nico-malkov/variometer/software/nRF5_SDK_17.1.0/examples/peripheral/variometer_v143/dfu/vario1d5/config/sdk_config.h

/**
 * Copyright (c) 2017 - 2020, Nordic Semiconductor ASA
 *
 * All rights reserved.
 *
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
 * 3. Neither the name of Nordic Semiconductor ASA nor the names of its
 *    contributors may be used to endorse or promote products derived from this
 *    software without specific prior written permission.
 *
 * 4. This software, with or without modification, must only be used with a
 *    Nordic Semiconductor ASA integrated circuit.
 *
 * 5. Any software provided in binary form under this license must not be reverse
 *    engineered, decompiled, modified and/or disassembled.
 *
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
 */



#ifndef SDK_CONFIG_H
#define SDK_CONFIG_H
// <<< Use Configuration Wizard in Context Menu >>>\n
#ifdef USE_APP_CONFIG
#include "app_config.h"
#endif
// <h> nRF_Bootloader 

//==========================================================
// <h> nrf_bootloader - Bootloader settings

//==========================================================
// <h> Application integrity checks 

//==========================================================
// <q> NRF_BL_APP_CRC_CHECK_SKIPPED_ON_GPREGRET2  - Skip CRC integrity check of the application when bit 1 (0-indexed) is set in the GPREGRET2 register.
 

// <i> Only CRC checks can be skipped. For other boot validation types, the GPREGRET2 register is ignored.

#ifndef NRF_BL_APP_CRC_CHECK_SKIPPED_ON_GPREGRET2
#define NRF_BL_APP_CRC_CHECK_SKIPPED_ON_GPREGRET2 1
#endif

// <q> NRF_BL_APP_CRC_CHECK_SKIPPED_ON_SYSTEMOFF_RESET  - Skip integrity check of the application when waking up from the System Off state.
 

// <i> Only CRC checks can be skipped. For other boot validation types, the reset state is ignored.

#ifndef NRF_BL_APP_CRC_CHECK_SKIPPED_ON_SYSTEMOFF_RESET
#define NRF_BL_APP_CRC_CHECK_SKIPPED_ON_SYSTEMOFF_RESET 1
#endif

// <q> NRF_BL_APP_SIGNATURE_CHECK_REQUIRED  - Perform signature check on the app. Requires the signature to be sent in the init packet.
 

#ifndef NRF_BL_APP_SIGNATURE_CHECK_REQUIRED
#define NRF_BL_APP_SIGNATURE_CHECK_REQUIRED 0
#endif

// <q> NRF_BL_DFU_ALLOW_UPDATE_FROM_APP  - Whether to allow the app to receive firmware updates for the bootloader to activate.
 

// <i> Enable this to allow the app to instruct the bootloader to activate firmware.
// <i> The bootloader will do its own postvalidation.

#ifndef NRF_BL_DFU_ALLOW_UPDATE_FROM_APP
#define NRF_BL_DFU_ALLOW_UPDATE_FROM_APP 0
#endif

// </h> 
//==========================================================

// <h> DFU mode enter method 

//==========================================================
// <e> NRF_BL_DFU_ENTER_METHOD_BUTTON - Enter DFU mode on button press.
//==========================================================
#ifndef NRF_BL_DFU_ENTER_METHOD_BUTTON
#define NRF_BL_DFU_ENTER_METHOD_BUTTON 1
#endif
// <o> NRF_BL_DFU_ENTER_METHOD_BUTTON_PIN  - Button for entering DFU mode.
 
// <0=> 0 (P0.0) 
// <1=> 1 (P0.1) 
// <2=> 2 (P0.2) 
// <3=> 3 (P0.3) 
// <4=> 4 (P0.4) 
// <5=> 5 (P0.5) 
// <6=> 6 (P0.6) 
// <7=> 7 (P0.7) 
// <8=> 8 (P0.8) 
// <9=> 9 (P0.9) 
// <10=> 10 (P0.10) 
// <11=> 11 (P0.11) 
// <12=> 12 (P0.12) 
// <13=> 13 (P0.13) 
// <14=> 14 (P0.14) 
// <15=> 15 (P0.15) 
// <16=> 16 (P0.16) 
// <17=> 17 (P0.17) 
// <18=> 18 (P0.18) 
// <19=> 19 (P0.19) 
// <20=> 20 (P0.20) 
// <21=> 21 (P0.21) 
// <22=> 22 (P0.22) 
// <23=> 23 (P0.23) 
// <24=> 24 (P0.24) 
// <25=> 25 (P0.25) 
// <26=> 26 (P0.26) 
// <27=> 27 (P0.27) 
// <28=> 28 (P0.28) 
// <29=> 29 (P0.29) 
// <30=> 30 (P0.30) 
// <31=> 31 (P0.31) 
// <32=> 32 (P1.0) 
// <33=> 33 (P1.1) 
// <34=> 34 (P1.2) 
// <35=> 35 (P1.3) 
// <36=> 36 (P1.4) 
// <37=> 37 (P1.5) 
// <38=> 38 (P1.6) 
// <39=> 39 (P1.7) 
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

#ifndef NRF_BL_DFU_ENTER_METHOD_BUTTON_PIN
#define NRF_BL_DFU_ENTER_METHOD_BUTTON_PIN 25
#endif

// </e>

// <q> NRF_BL_DFU_ENTER_METHOD_PINRESET  - Enter DFU mode on pin reset.
 

#ifndef NRF_BL_DFU_ENTER_METHOD_PINRESET
#define NRF_BL_DFU_ENTER_METHOD_PINRESET 0
#endif

// <q> NRF_BL_DFU_ENTER_METHOD_GPREGRET  - Enter DFU mode when bit 0 is set in the NRF_POWER_GPREGRET register.
 

#ifndef NRF_BL_DFU_ENTER_METHOD_GPREGRET
#define NRF_BL_DFU_ENTER_METHOD_GPREGRET 1
#endif

// <q> NRF_BL_DFU_ENTER_METHOD_BUTTONLESS  - Enter DFU mode when the Boolean enter_buttonless_dfu in DFU settings is true.
 

#ifndef NRF_BL_DFU_ENTER_METHOD_BUTTONLESS
#define NRF_BL_DFU_ENTER_METHOD_BUTTONLESS 0
#endif

// </h> 
//==========================================================

// <h> DFU timers 

//==========================================================
// <o> NRF_BL_DFU_CONTINUATION_TIMEOUT_MS - Timeout in ms when expecting an update immediately.  <100-60000000> 


// <i> This timeout is used after updating the SoftDevice, when there is
// <i> already a valid application present. The bootloader will enter DFU mode
// <i> for a short time instead of booting the old application to allow the host
// <i> to immediately transfer a new application if it wishes.

#ifndef NRF_BL_DFU_CONTINUATION_TIMEOUT_MS
#define NRF_BL_DFU_CONTINUATION_TIMEOUT_MS 10000
#endif

// <o> NRF_BL_DFU_INACTIVITY_TIMEOUT_MS - Timeout in ms before automatically starting a valid application due to inactivity.  <0-60000000> 


// <i> If 0, no inactivity timer will be used. Values 1-99 are invalid.

#ifndef NRF_BL_DFU_INACTIVITY_TIMEOUT_MS
#define NRF_BL_DFU_INACTIVITY_TIMEOUT_MS 120000
#endif

// </h> 
//==========================================================

// <h> Watchdog timer 

//==========================================================
// <o> NRF_BL_WDT_MAX_SCHEDULER_LATENCY_MS - Maximum latency of the scheduler in miliseconds 
// <i> Maximum latency of the scheduler is compared with
// <i> watchdog counter reload value (CRV). If latency is big
// <i> enough, the watchdog will be fed from internal timer
// <i> handler along with feed from user function. If latency
// <i> is smaller than CRV, the watchdog will not be internally fed once
// <i> it will be externally fed. Maximum latency is mainly affected
// <i> by flash operations.

#ifndef NRF_BL_WDT_MAX_SCHEDULER_LATENCY_MS
#define NRF_BL_WDT_MAX_SCHEDULER_LATENCY_MS 10000
#endif

// </h> 
//==========================================================

// <h> Misc Bootloader settings 

//==========================================================
// <q> NRF_BL_DEBUG_PORT_DISABLE  - Disable access to the chip via the debug port.
 

// <i> Disable access to the chip via the debug port.
// <i> This modifies the APPROTECT and DEBUGCTRL registers.
// <i> Enable this option in production code if such
// <i> access should be prohibited. Read about the registers
// <i> for more details.

#ifndef NRF_BL_DEBUG_PORT_DISABLE
#define NRF_BL_DEBUG_PORT_DISABLE 0
#endif

// <o> NRF_BL_FW_COPY_PROGRESS_STORE_STEP - Number of pages copied after which progress in the settings page is updated. 
// <i> Progress stored in the settings page allows the bootloader to resume
// <i> copying the new firmware in case of interruption (reset).
// <i> If the value is small, then the resume point is more accurate. However,
// <i>  it also impacts negatively on flash wear.

#ifndef NRF_BL_FW_COPY_PROGRESS_STORE_STEP
#define NRF_BL_FW_COPY_PROGRESS_STORE_STEP 8
#endif

// <o> NRF_BL_RESET_DELAY_MS - Time to wait before resetting the bootloader. 
// <i> Time (in ms) to wait before resetting the bootloader after DFU has been completed or aborted. This allows more time for e.g. disconnecting the BLE link or writing logs.

#ifndef NRF_BL_RESET_DELAY_MS
#define NRF_BL_RESET_DELAY_MS 0
#endif

// </h> 
//==========================================================

// </h> 
//==========================================================

// </h> 
//==========================================================

// <h> nRF_Crypto 

//==========================================================
// <e> NRF_CRYPTO_ENABLED - nrf_crypto - Cryptography library.
//==========================================================
#ifndef NRF_CRYPTO_ENABLED
#define NRF_CRYPTO_ENABLED 1
#endif
// <o> NRF_CRYPTO_ALLOCATOR  - Memory allocator
 

// <i> Choose memory allocator used by nrf_crypto. Default is alloca if possible or nrf_malloc otherwise. If 'User macros' are selected, the user has to create 'nrf_crypto_allocator.h' file that contains NRF_CRYPTO_ALLOC, NRF_CRYPTO_FREE, and NRF_CRYPTO_ALLOC_ON_STACK.
// <0=> Default 
// <1=> User macros 
// <2=> On stack (alloca) 
// <3=> C dynamic memory (malloc) 
// <4=> SDK Memory Manager (nrf_malloc) 

#ifndef NRF_CRYPTO_ALLOCATOR
#define NRF_CRYPTO_ALLOCATOR 1
#endif

// <e> NRF_CRYPTO_BACKEND_CC310_BL_ENABLED - Enable the ARM Cryptocell CC310 reduced backend.

// <i> The CC310 hardware-accelerated cryptography backend with reduced functionality and footprint (only available on nRF52840).
//==========================================================
#ifndef NRF_CRYPTO_BACKEND_CC310_BL_ENABLED
#define NRF_CRYPTO_BACKEND_CC310_BL_ENABLED 1
#endif
// <q> NRF_CRYPTO_BACKEND_CC310_BL_ECC_SECP224R1_ENABLED  - Enable the secp224r1 elliptic curve support using CC310_BL.
 

#ifndef NRF_CRYPTO_BACKEND_CC310_BL_ECC_SECP224R1_ENABLED
#define NRF_CRYPTO_BACKEND_CC310_BL_ECC_SECP224R1_ENABLED 0
#endif

// <q> NRF_CRYPTO_BACKEND_CC310_BL_ECC_SECP256R1_ENABLED  - Enable the secp256r1 elliptic curve support using CC310_BL.
 

#ifndef NRF_CRYPTO_BACKEND_CC310_BL_ECC_SECP256R1_ENABLED
#define NRF_CRYPTO_BACKEND_CC310_BL_ECC_SECP256R1_ENABLED 1
#endif

// <q> NRF_CRYPTO_BACKEND_CC310_BL_HASH_SHA256_ENABLED  - CC310_BL SHA-256 hash functionality.
 

// <i> CC310_BL backend implementation for hardware-accelerated SHA-256.

#ifndef NRF_CRYPTO_BACKEND_CC310_BL_HASH_SHA256_ENABLED
#define NRF_CRYPTO_BACKEND_CC310_BL_HASH_SHA256_ENABLED 1
#endif

// <q> NRF_CRYPTO_BACKEND_CC310_BL_HASH_AUTOMATIC_RAM_BUFFER_ENABLED  - nrf_cc310_bl buffers to RAM before running hash operation
 

// <i> Enabling this makes hashing of addresses in FLASH range possible. Size of buffer allocated for hashing is set by NRF_CRYPTO_BACKEND_CC310_BL_HASH_AUTOMATIC_RAM_BUFFER_SIZE

#ifndef NRF_CRYPTO_BACKEND_CC310_BL_HASH_AUTOMATIC_RAM_BUFFER_ENABLED
#define NRF_CRYPTO_BACKEND_CC310_BL_HASH_AUTOMATIC_RAM_BUFFER_ENABLED 1
#endif

// <o> NRF_CRYPTO_BACKEND_CC310_BL_HASH_AUTOMATIC_RAM_BUFFER_SIZE - nrf_cc310_bl hash outputs digests in little endian 
// <i> Makes the nrf_cc310_bl hash functions output digests in little endian format. Only for use in nRF SDK DFU!

#ifndef NRF_CRYPTO_BACKEND_CC310_BL_HASH_AUTOMATIC_RAM_BUFFER_SIZE
#define NRF_CRYPTO_BACKEND_CC310_BL_HASH_AUTOMATIC_RAM_BUFFER_SIZE 4096
#endif

// <q> NRF_CRYPTO_BACKEND_CC310_BL_INTERRUPTS_ENABLED  - Enable Interrupts while support using CC310 bl.
 

// <i> Select a library version compatible with the configuration. When interrupts are disable, a version named _noint must be used

#ifndef NRF_CRYPTO_BACKEND_CC310_BL_INTERRUPTS_ENABLED
#define NRF_CRYPTO_BACKEND_CC310_BL_INTERRUPTS_ENABLED 1
#endif

// </e>

// <e> NRF_CRYPTO_BACKEND_CC310_ENABLED - Enable the ARM Cryptocell CC310 backend.

// <i> The CC310 hardware-accelerated cryptography backend (only available on nRF52840).
//==========================================================
#ifndef NRF_CRYPTO_BACKEND_CC310_ENABLED
#define NRF_CRYPTO_BACKEND_CC310_ENABLED 0
#endif
// <q> NRF_CRYPTO_BACKEND_CC310_AES_CBC_ENABLED  - Enable the AES CBC mode using CC310.
 

#ifndef NRF_CRYPTO_BACKEND_CC310_AES_CBC_ENABLED
#define NRF_CRYPTO_BACKEND_CC310_AES_CBC_ENABLED 1
#endif

// <q> NRF_CRYPTO_BACKEND_CC310_AES_CTR_ENABLED  - Enable the AES CTR mode using CC310.
 

#ifndef NRF_CRYPTO_BACKEND_CC310_AES_CTR_ENABLED
#define NRF_CRYPTO_BACKEND_CC310_AES_CTR_ENABLED 1
#endif

// <q> NRF_CRYPTO_BACKEND_CC310_AES_ECB_ENABLED  - Enable the AES ECB mode using CC310.
 

#ifndef NRF_CRYPTO_BACKEND_CC310_AES_ECB_ENABLED
#define NRF_CRYPTO_BACKEND_CC310_AES_ECB_ENABLED 1
#endif

// <q> NRF_CRYPTO_BACKEND_CC310_AES_CBC_MAC_ENABLED  - Enable the AES CBC_MAC mode using CC310.
 

#ifndef NRF_CRYPTO_BACKEND_CC310_AES_CBC_MAC_ENABLED
#define NRF_CRYPTO_BACKEND_CC310_AES_CBC_MAC_ENABLED 1
#endif

// <q> NRF_CRYPTO_BACKEND_CC310_AES_CMAC_ENABLED  - Enable the AES CMAC mode using CC310.
 

#ifndef NRF_CRYPTO_BACKEND_CC310_AES_CMAC_ENABLED
#define NRF_CRYPTO_BACKEND_CC310_AES_CMAC_ENABLED 1
#endif

// <q> NRF_CRYPTO_BACKEND_CC310_AES_CCM_ENABLED  - Enable the AES CCM mode using CC310.
 

#ifndef NRF_CRYPTO_BACKEND_CC310_AES_CCM_ENABLED
#define NRF_CRYPTO_BACKEND_CC310_AES_CCM_ENABLED 1
#endif

// <q> NRF_CRYPTO_BACKEND_CC310_AES_CCM_STAR_ENABLED  - Enable the AES CCM* mode using CC310.
 

#ifndef NRF_CRYPTO_BACKEND_CC310_AES_CCM_STAR_ENABLED
#define NRF_CRYPTO_BACKEND_CC310_AES_CCM_STAR_ENABLED 1
#endif

// <q> NRF_CRYPTO_BACKEND_CC310_CHACHA_POLY_ENABLED  - Enable the CHACHA-POLY mode using CC310.
 

#ifndef NRF_CRYPTO_BACKEND_CC310_CHACHA_POLY_ENABLED
#define NRF_CRYPTO_BACKEND_CC310_CHACHA_POLY_ENABLED 1
#endif

// <q> NRF_CRYPTO_BACKEND_CC310_ECC_SECP160R1_ENABLED  - Enable the secp160r1 elliptic curve support using CC310.
 

#ifndef NRF_CRYPTO_BACKEND_CC310_ECC_SECP160R1_ENABLED
#define NRF_CRYPTO_BACKEND_CC310_ECC_SECP160R1_ENABLED 1
#endif

// <q> NRF_CRYPTO_BACKEND_CC310_ECC_SECP160R2_ENABLED  - Enable the secp160r2 elliptic curve support using CC310.
 

#ifndef NRF_CRYPTO_BACKEND_CC310_ECC_SECP160R2_ENABLED
#define NRF_CRYPTO_BACKEND_CC310_ECC_SECP160R2_ENABLED 1
#endif

// <q> NRF_CRYPTO_BACKEND_CC310_ECC_SECP192R1_ENABLED  - Enable the secp192r1 elliptic curve support using CC310.
 

#ifndef NRF_CRYPTO_BACKEND_CC310_ECC_SECP192R1_ENABLED
#define NRF_CRYPTO_BACKEND_CC310_ECC_SECP192R1_ENABLED 1
#endif

// <q> NRF_CRYPTO_BACKEND_CC310_ECC_SECP224R1_ENABLED  - Enable the secp224r1 elliptic curve support using CC310.
 

#ifndef NRF_CRYPTO_BACKEND_CC310_ECC_SECP224R1_ENABLED
#define NRF_CRYPTO_BACKEND_CC310_ECC_SECP224R1_ENABLED 1
#endif

// <q> NRF_CRYPTO_BACKEND_CC310_ECC_SECP256R1_ENABLED  - Enable the secp256r1 elliptic curve support using CC310.
 

#ifndef NRF_CRYPTO_BACKEND_CC310_ECC_SECP256R1_ENABLED
#define NRF_CRYPTO_BACKEND_CC310_ECC_SECP256R1_ENABLED 1
#endif

// <q> NRF_CRYPTO_BACKEND_CC310_ECC_SECP384R1_ENABLED  - Enable the secp384r1 elliptic curve support using CC310.
 

#ifndef NRF_CRYPTO_BACKEND_CC310_ECC_SECP384R1_ENABLED
#define NRF_CRYPTO_BACKEND_CC310_ECC_SECP384R1_ENABLED 1
#endif

// <q> NRF_CRYPTO_BACKEND_CC310_ECC_SECP521R1_ENABLED  - Enable the secp521r1 elliptic curve support using CC310.
 

#ifndef NRF_CRYPTO_BACKEND_CC310_ECC_SECP521R1_ENABLED
#define NRF_CRYPTO_BACKEND_CC310_ECC_SECP521R1_ENABLED 1
#endif

// <q> NRF_CRYPTO_BACKEND_CC310_ECC_SECP160K1_ENABLED  - Enable the secp160k1 elliptic curve support using CC310.
 

#ifndef NRF_CRYPTO_BACKEND_CC310_ECC_SECP160K1_ENABLED
#define NRF_CRYPTO_BACKEND_CC310_ECC_SECP160K1_ENABLED 1
#endif

// <q> NRF_CRYPTO_BACKEND_CC310_ECC_SECP192K1_ENABLED  - Enable the secp192k1 elliptic curve support using CC310.
 

#ifndef NRF_CRYPTO_BACKEND_CC310_ECC_SECP192K1_ENABLED
#define NRF_CRYPTO_BACKEND_CC310_ECC_SECP192K1_ENABLED 1
#endif

// <q> NRF_CRYPTO_BACKEND_CC310_ECC_SECP224K1_ENABLED  - Enable the secp224k1 elliptic curve support using CC310.
 

#ifndef NRF_CRYPTO_BACKEND_CC310_ECC_SECP224K1_ENABLED
#define NRF_CRYPTO_BACKEND_CC310_ECC_SECP224K1_ENABLED 1
#endif

// <q> NRF_CRYPTO_BACKEND_CC310_ECC_SECP256K1_ENABLED  - Enable the secp256k1 elliptic curve support using CC310.
 

#ifndef NRF_CRYPTO_BACKEND_CC310_ECC_SECP256K1_ENABLED
#define NRF_CRYPTO_BACKEND_CC310_ECC_SECP256K1_ENABLED 1
#endif

// <q> NRF_CRYPTO_BACKEND_CC310_ECC_CURVE25519_ENABLED  - Enable the Curve25519 curve support using CC310.
 

#ifndef NRF_CRYPTO_BACKEND_CC310_ECC_CURVE25519_ENABLED
#define NRF_CRYPTO_BACKEND_CC310_ECC_CURVE25519_ENABLED 1
#endif

// <q> NRF_CRYPTO_BACKEND_CC310_ECC_ED25519_ENABLED  - Enable the Ed25519 curve support using CC310.
 

#ifndef NRF_CRYPTO_BACKEND_CC310_ECC_ED25519_ENABLED
#define NRF_CRYPTO_BACKEND_CC310_ECC_ED25519_ENABLED 1
#endif

// <q> NRF_CRYPTO_BACKEND_CC310_HASH_SHA256_ENABLED  - CC310 SHA-256 hash functionality.
 

// <i> CC310 backend implementation for hardware-accelerated SHA-256.

#ifndef NRF_CRYPTO_BACKEND_CC310_HASH_SHA256_ENABLED
#define NRF_CRYPTO_BACKEND_CC310_HASH_SHA256_ENABLED 1
#endif

// <q> NRF_CRYPTO_BACKEND_CC310_HASH_SHA512_ENABLED  - CC310 SHA-512 hash functionality
 

// <i> CC310 backend implementation for SHA-512 (in software).

#ifndef NRF_CRYPTO_BACKEND_CC310_HASH_SHA512_ENABLED
#define NRF_CRYPTO_BACKEND_CC310_HASH_SHA512_ENABLED 1
#endif

// <q> NRF_CRYPTO_BACKEND_CC310_HMAC_SHA256_ENABLED  - CC310 HMAC using SHA-256
 

// <i> CC310 backend implementation for HMAC using hardware-accelerated SHA-256.

#ifndef NRF_CRYPTO_BACKEND_CC310_HMAC_SHA256_ENABLED
#define NRF_CRYPTO_BACKEND_CC310_HMAC_SHA256_ENABLED 1
#endif

// <q> NRF_CRYPTO_BACKEND_CC310_HMAC_SHA512_ENABLED  - CC310 HMAC using SHA-512
 

// <i> CC310 backend implementation for HMAC using SHA-512 (in software).

#ifndef NRF_CRYPTO_BACKEND_CC310_HMAC_SHA512_ENABLED
#define NRF_CRYPTO_BACKEND_CC310_HMAC_SHA512_ENABLED 1
#endif

// <q> NRF_CRYPTO_BACKEND_CC310_RNG_ENABLED  - Enable RNG support using CC310.
 

#ifndef NRF_CRYPTO_BACKEND_CC310_RNG_ENABLED
#define NRF_CRYPTO_BACKEND_CC310_RNG_ENABLED 1
#endif

// <q> NRF_CRYPTO_BACKEND_CC310_INTERRUPTS_ENABLED  - Enable Interrupts while support using CC310.
 

// <i> Select a library version compatible with the configuration. When interrupts are disable, a version named _noint must be used

#ifndef NRF_CRYPTO_BACKEND_CC310_INTERRUPTS_ENABLED
#define NRF_CRYPTO_BACKEND_CC310_INTERRUPTS_ENABLED 1
#endif

// </e>

// <e> NRF_CRYPTO_BACKEND_CIFRA_ENABLED - Enable the Cifra backend.
//==========================================================
#ifndef NRF_CRYPTO_BACKEND_CIFRA_ENABLED
#define NRF_CRYPTO_BACKEND_CIFRA_ENABLED 0
#endif
// <q> NRF_CRYPTO_BACKEND_CIFRA_AES_EAX_ENABLED  - Enable the AES EAX mode using Cifra.
 

#ifndef NRF_CRYPTO_BACKEND_CIFRA_AES_EAX_ENABLED
#define NRF_CRYPTO_BACKEND_CIFRA_AES_EAX_ENABLED 1
#endif

// </e>

// <e> NRF_CRYPTO_BACKEND_MBEDTLS_ENABLED - Enable the mbed TLS backend.
//==========================================================
#ifndef NRF_CRYPTO_BACKEND_MBEDTLS_ENABLED
#define NRF_CRYPTO_BACKEND_MBEDTLS_ENABLED 0
#endif
// <q> NRF_CRYPTO_BACKEND_MBEDTLS_AES_CBC_ENABLED  - Enable the AES CBC mode mbed TLS.
 

#ifndef NRF_CRYPTO_BACKEND_MBEDTLS_AES_CBC_ENABLED
#define NRF_CRYPTO_BACKEND_MBEDTLS_AES_CBC_ENABLED 1
#endif

// <q> NRF_CRYPTO_BACKEND_MBEDTLS_AES_CTR_ENABLED  - Enable the AES CTR mode using mbed TLS.
 

#ifndef NRF_CRYPTO_BACKEND_MBEDTLS_AES_CTR_ENABLED
#define NRF_CRYPTO_BACKEND_MBEDTLS_AES_CTR_ENABLED 1
#endif

// <q> NRF_CRYPTO_BACKEND_MBEDTLS_AES_CFB_ENABLED  - Enable the AES CFB mode using mbed TLS.
 

#ifndef NRF_CRYPTO_BACKEND_MBEDTLS_AES_CFB_ENABLED
#define NRF_CRYPTO_BACKEND_MBEDTLS_AES_CFB_ENABLED 1
#endif

// <q> NRF_CRYPTO_BACKEND_MBEDTLS_AES_ECB_ENABLED  - Enable the AES ECB mode using mbed TLS.
 

#ifndef NRF_CRYPTO_BACKEND_MBEDTLS_AES_ECB_ENABLED
#define NRF_CRYPTO_BACKEND_MBEDTLS_AES_ECB_ENABLED 1
#endif

// <q> NRF_CRYPTO_BACKEND_MBEDTLS_AES_CBC_MAC_ENABLED  - Enable the AES CBC MAC mode using mbed TLS.
 

#ifndef NRF_CRYPTO_BACKEND_MBEDTLS_AES_CBC_MAC_ENABLED
#define NRF_CRYPTO_BACKEND_MBEDTLS_AES_CBC_MAC_ENABLED 1
#endif

// <q> NRF_CRYPTO_BACKEND_MBEDTLS_AES_CMAC_ENABLED  - Enable the AES CMAC mode using mbed TLS.
 

#ifndef NRF_CRYPTO_BACKEND_MBEDTLS_AES_CMAC_ENABLED
#define NRF_CRYPTO_BACKEND_MBEDTLS_AES_CMAC_ENABLED 1
#endif

// <q> NRF_CRYPTO_BACKEND_MBEDTLS_AES_CCM_ENABLED  - Enable the AES CCM mode using mbed TLS.
 

#ifndef NRF_CRYPTO_BACKEND_MBEDTLS_AES_CCM_ENABLED
#define NRF_CRYPTO_BACKEND_MBEDTLS_AES_CCM_ENABLED 1
#endif

// <q> NRF_CRYPTO_BACKEND_MBEDTLS_AES_GCM_ENABLED  - Enable the AES GCM mode using mbed TLS.
 

#ifndef NRF_CRYPTO_BACKEND_MBEDTLS_AES_GCM_ENABLED
#define NRF_CRYPTO_BACKEND_MBEDTLS_AES_GCM_ENABLED 1
#endif

// <q> NRF_CRYPTO_BACKEND_MBEDTLS_ECC_SECP192R1_ENABLED  - Enable secp192r1 (NIST 192-bit) curve
 

// <i> Enable this setting if you need secp192r1 (NIST 192-bit) support using MBEDTLS

#ifndef NRF_CRYPTO_BACKEND_MBEDTLS_ECC_SECP192R1_ENABLED
#define NRF_CRYPTO_BACKEND_MBEDTLS_ECC_SECP192R1_ENABLED 1
#endif

// <q> NRF_CRYPTO_BACKEND_MBEDTLS_ECC_SECP224R1_ENABLED  - Enable secp224r1 (NIST 224-bit) curve
 

// <i> Enable this setting if you need secp224r1 (NIST 224-bit) support using MBEDTLS

#ifndef NRF_CRYPTO_BACKEND_MBEDTLS_ECC_SECP224R1_ENABLED
#define NRF_CRYPTO_BACKEND_MBEDTLS_ECC_SECP224R1_ENABLED 1
#endif

// <q> NRF_CRYPTO_BACKEND_MBEDTLS_ECC_SECP256R1_ENABLED  - Enable secp256r1 (NIST 256-bit) curve
 

// <i> Enable this setting if you need secp256r1 (NIST 256-bit) support using MBEDTLS

#ifndef NRF_CRYPTO_BACKEND_MBEDTLS_ECC_SECP256R1_ENABLED
#define NRF_CRYPTO_BACKEND_MBEDTLS_ECC_SECP256R1_ENABLED 1
#endif

// <q> NRF_CRYPTO_BACKEND_MBEDTLS_ECC_SECP384R1_ENABLED  - Enable secp384r1 (NIST 384-bit) curve
 

// <i> Enable this setting if you need secp384r1 (NIST 384-bit) support using MBEDTLS

#ifndef NRF_CRYPTO_BACKEND_MBEDTLS_ECC_SECP384R1_ENABLED
#define NRF_CRYPTO_BACKEND_MBEDTLS_ECC_SECP384R1_ENABLED 1
#endif

// <q> NRF_CRYPTO_BACKEND_MBEDTLS_ECC_SECP521R1_ENABLED  - Enable secp521r1 (NIST 521-bit) curve
 

// <i> Enable this setting if you need secp521r1 (NIST 521-bit) support using MBEDTLS

#ifndef NRF_CRYPTO_BACKEND_MBEDTLS_ECC_SECP521R1_ENABLED
#define NRF_CRYPTO_BACKEND_MBEDTLS_ECC_SECP521R1_ENABLED 1
#endif

// <q> NRF_CRYPTO_BACKEND_MBEDTLS_ECC_SECP192K1_ENABLED  - Enable secp192k1 (Koblitz 192-bit) curve
 

// <i> Enable this setting if you need secp192k1 (Koblitz 192-bit) support using MBEDTLS

#ifndef NRF_CRYPTO_BACKEND_MBEDTLS_ECC_SECP192K1_ENABLED
#define NRF_CRYPTO_BACKEND_MBEDTLS_ECC_SECP192K1_ENABLED 1
#endif

// <q> NRF_CRYPTO_BACKEND_MBEDTLS_ECC_SECP224K1_ENABLED  - Enable secp224k1 (Koblitz 224-bit) curve
 

// <i> Enable this setting if you need secp224k1 (Koblitz 224-bit) support using MBEDTLS

#ifndef NRF_CRYPTO_BACKEND_MBEDTLS_ECC_SECP224K1_ENABLED
#define NRF_CRYPTO_BACKEND_MBEDTLS_ECC_SECP224K1_ENABLED 1
#endif

// <q> NRF_CRYPTO_BACKEND_MBEDTLS_ECC_SECP256K1_ENABLED  - Enable secp256k1 (Koblitz 256-bit) curve
 

// <i> Enable this setting if you need secp256k1 (Koblitz 256-bit) support using MBEDTLS

#ifndef NRF_CRYPTO_BACKEND_MBEDTLS_ECC_SECP256K1_ENABLED
#define NRF_CRYPTO_BACKEND_MBEDTLS_ECC_SECP256K1_ENABLED 1
#endif

// <q> NRF_CRYPTO_BACKEND_MBEDTLS_ECC_BP256R1_ENABLED  - Enable bp256r1 (Brainpool 256-bit) curve
 

// <i> Enable this setting if you need bp256r1 (Brainpool 256-bit) support using MBEDTLS

#ifndef NRF_CRYPTO_BACKEND_MBEDTLS_ECC_BP256R1_ENABLED
#define NRF_CRYPTO_BACKEND_MBEDTLS_ECC_BP256R1_ENABLED 1
#endif

// <q> NRF_CRYPTO_BACKEND_MBEDTLS_ECC_BP384R1_ENABLED  - Enable bp384r1 (Brainpool 384-bit) curve
 

// <i> Enable this setting if you need bp384r1 (Brainpool 384-bit) support using MBEDTLS

#ifndef NRF_CRYPTO_BACKEND_MBEDTLS_ECC_BP384R1_ENABLED
#define NRF_CRYPTO_BACKEND_MBEDTLS_ECC_BP384R1_ENABLED 1
#endif

// <q> NRF_CRYPTO_BACKEND_MBEDTLS_ECC_BP512R1_ENABLED  - Enable bp512r1 (Brainpool 512-bit) curve
 

// <i> Enable this setting if you need bp512r1 (Brainpool 512-bit) support using MBEDTLS

#ifndef NRF_CRYPTO_BACKEND_MBEDTLS_ECC_BP512R1_ENABLED
#define NRF_CRYPTO_BACKEND_MBEDTLS_ECC_BP512R1_ENABLED 1
#endif

// <q> NRF_CRYPTO_BACKEND_MBEDTLS_ECC_CURVE25519_ENABLED  - Enable Curve25519 curve
 

// <i> Enable this setting if you need Curve25519 support using MBEDTLS

#ifndef NRF_CRYPTO_BACKEND_MBEDTLS_ECC_CURVE25519_ENABLED
#define NRF_CRYPTO_BACKEND_MBEDTLS_ECC_CURVE25519_ENABLED 1
#endif

// <q> NRF_CRYPTO_BACKEND_MBEDTLS_HASH_SHA256_ENABLED  - Enable mbed TLS SHA-256 hash functionality.
 

// <i> mbed TLS backend implementation for SHA-256.

#ifndef NRF_CRYPTO_BACKEND_MBEDTLS_HASH_SHA256_ENABLED
#define NRF_CRYPTO_BACKEND_MBEDTLS_HASH_SHA256_ENABLED 1
#endif

// <q> NRF_CRYPTO_BACKEND_MBEDTLS_HASH_SHA512_ENABLED  - Enable mbed TLS SHA-512 hash functionality.
 

// <i> mbed TLS backend implementation for SHA-512.

#ifndef NRF_CRYPTO_BACKEND_MBEDTLS_HASH_SHA512_ENABLED
#define NRF_CRYPTO_BACKEND_MBEDTLS_HASH_SHA512_ENABLED 1
#endif

// <q> NRF_CRYPTO_BACKEND_MBEDTLS_HMAC_SHA256_ENABLED  - Enable mbed TLS HMAC using SHA-256.
 

// <i> mbed TLS backend implementation for HMAC using SHA-256.

#ifndef NRF_CRYPTO_BACKEND_MBEDTLS_HMAC_SHA256_ENABLED
#define NRF_CRYPTO_BACKEND_MBEDTLS_HMAC_SHA256_ENABLED 1
#endif

// <q> NRF_CRYPTO_BACKEND_MBEDTLS_HMAC_SHA512_ENABLED  - Enable mbed TLS HMAC using SHA-512.
 

// <i> mbed TLS backend implementation for HMAC using SHA-512.

#ifndef NRF_CRYPTO_BACKEND_MBEDTLS_HMAC_SHA512_ENABLED
#define NRF_CRYPTO_BACKEND_MBEDTLS_HMAC_SHA512_ENABLED 1
#endif

// </e>

// <e> NRF_CRYPTO_BACKEND_MICRO_ECC_ENABLED - Enable the micro-ecc backend.
//==========================================================
#ifndef NRF_CRYPTO_BACKEND_MICRO_ECC_ENABLED
#define NRF_CRYPTO_BACKEND_MICRO_ECC_ENABLED 0
#endif
// <q> NRF_CRYPTO_BACKEND_MICRO_ECC_ECC_SECP192R1_ENABLED  - Enable secp192r1 (NIST 192-bit) curve
 

// <i> Enable this setting if you need secp192r1 (NIST 192-bit) support using micro-ecc

#ifndef NRF_CRYPTO_BACKEND_MICRO_ECC_ECC_SECP192R1_ENABLED
#define NRF_CRYPTO_BACKEND_MICRO_ECC_ECC_SECP192R1_ENABLED 1
#endif

// <q> NRF_CRYPTO_BACKEND_MICRO_ECC_ECC_SECP224R1_ENABLED  - Enable secp224r1 (NIST 224-bit) curve
 

// <i> Enable this setting if you need secp224r1 (NIST 224-bit) support using micro-ecc

#ifndef NRF_CRYPTO_BACKEND_MICRO_ECC_ECC_SECP224R1_ENABLED
#define NRF_CRYPTO_BACKEND_MICRO_ECC_ECC_SECP224R1_ENABLED 1
#endif

// <q> NRF_CRYPTO_BACKEND_MICRO_ECC_ECC_SECP256R1_ENABLED  - Enable secp256r1 (NIST 256-bit) curve
 

// <i> Enable this setting if you need secp256r1 (NIST 256-bit) support using micro-ecc

#ifndef NRF_CRYPTO_BACKEND_MICRO_ECC_ECC_SECP256R1_ENABLED
#define NRF_CRYPTO_BACKEND_MICRO_ECC_ECC_SECP256R1_ENABLED 1
#endif

// <q> NRF_CRYPTO_BACKEND_MICRO_ECC_ECC_SECP256K1_ENABLED  - Enable secp256k1 (Koblitz 256-bit) curve
 

// <i> Enable this setting if you need secp256k1 (Koblitz 256-bit) support using micro-ecc

#ifndef NRF_CRYPTO_BACKEND_MICRO_ECC_ECC_SECP256K1_ENABLED
#define NRF_CRYPTO_BACKEND_MICRO_ECC_ECC_SECP256K1_ENABLED 1
#endif

// </e>

// <e> NRF_CRYPTO_BACKEND_NRF_HW_RNG_ENABLED - Enable the nRF HW RNG backend.

// <i> The nRF HW backend provide access to RNG peripheral in nRF5x devices.
//==========================================================
#ifndef NRF_CRYPTO_BACKEND_NRF_HW_RNG_ENABLED
#define NRF_CRYPTO_BACKEND_NRF_HW_RNG_ENABLED 0
#endif
// <q> NRF_CRYPTO_BACKEND_NRF_HW_RNG_MBEDTLS_CTR_DRBG_ENABLED  - Enable mbed TLS CTR-DRBG algorithm.
 

// <i> Enable mbed TLS CTR-DRBG standardized by NIST (NIST SP 800-90A Rev. 1). The nRF HW RNG is used as an entropy source for seeding.

#ifndef NRF_CRYPTO_BACKEND_NRF_HW_RNG_MBEDTLS_CTR_DRBG_ENABLED
#define NRF_CRYPTO_BACKEND_NRF_HW_RNG_MBEDTLS_CTR_DRBG_ENABLED 1
#endif

// </e>

// <e> NRF_CRYPTO_BACKEND_NRF_SW_ENABLED - Enable the legacy nRFx sw for crypto.

// <i> The nRF SW cryptography backend (only used in bootloader context).
//==========================================================
#ifndef NRF_CRYPTO_BACKEND_NRF_SW_ENABLED
#define NRF_CRYPTO_BACKEND_NRF_SW_ENABLED 0
#endif
// <q> NRF_CRYPTO_BACKEND_NRF_SW_HASH_SHA256_ENABLED  - nRF SW hash backend support for SHA-256
 

// <i> The nRF SW backend provide access to nRF SDK legacy hash implementation of SHA-256.

#ifndef NRF_CRYPTO_BACKEND_NRF_SW_HASH_SHA256_ENABLED
#define NRF_CRYPTO_BACKEND_NRF_SW_HASH_SHA256_ENABLED 1
#endif

// </e>

// <e> NRF_CRYPTO_BACKEND_OBERON_ENABLED - Enable the Oberon backend

// <i> The Oberon backend
//==========================================================
#ifndef NRF_CRYPTO_BACKEND_OBERON_ENABLED
#define NRF_CRYPTO_BACKEND_OBERON_ENABLED 0
#endif
// <q> NRF_CRYPTO_BACKEND_OBERON_CHACHA_POLY_ENABLED  - Enable the CHACHA-POLY mode using Oberon.
 

#ifndef NRF_CRYPTO_BACKEND_OBERON_CHACHA_POLY_ENABLED
#define NRF_CRYPTO_BACKEND_OBERON_CHACHA_POLY_ENABLED 0
#endif

// <q> NRF_CRYPTO_BACKEND_OBERON_ECC_SECP256R1_ENABLED  - Enable secp256r1 curve
 

// <i> Enable this setting if you need secp256r1 curve support using Oberon library

#ifndef NRF_CRYPTO_BACKEND_OBERON_ECC_SECP256R1_ENABLED
#define NRF_CRYPTO_BACKEND_OBERON_ECC_SECP256R1_ENABLED 1
#endif

// <q> NRF_CRYPTO_BACKEND_OBERON_ECC_CURVE25519_ENABLED  - Enable Curve25519 ECDH
 

// <i> Enable this setting if you need Curve25519 ECDH support using Oberon library

#ifndef NRF_CRYPTO_BACKEND_OBERON_ECC_CURVE25519_ENABLED
#define NRF_CRYPTO_BACKEND_OBERON_ECC_CURVE25519_ENABLED 0
#endif

// <q> NRF_CRYPTO_BACKEND_OBERON_ECC_ED25519_ENABLED  - Enable Ed25519 signature scheme
 

// <i> Enable this setting if you need Ed25519 support using Oberon library

#ifndef NRF_CRYPTO_BACKEND_OBERON_ECC_ED25519_ENABLED
#define NRF_CRYPTO_BACKEND_OBERON_ECC_ED25519_ENABLED 0
#endif

// <q> NRF_CRYPTO_BACKEND_OBERON_HASH_SHA256_ENABLED  - Oberon SHA-256 hash functionality
 

// <i> Oberon backend implementation for SHA-256.

#ifndef NRF_CRYPTO_BACKEND_OBERON_HASH_SHA256_ENABLED
#define NRF_CRYPTO_BACKEND_OBERON_HASH_SHA256_ENABLED 1
#endif

// <q> NRF_CRYPTO_BACKEND_OBERON_HASH_SHA512_ENABLED  - Oberon SHA-512 hash functionality
 

// <i> Oberon backend implementation for SHA-512.

#ifndef NRF_CRYPTO_BACKEND_OBERON_HASH_SHA512_ENABLED
#define NRF_CRYPTO_BACKEND_OBERON_HASH_SHA512_ENABLED 0
#endif

// <q> NRF_CRYPTO_BACKEND_OBERON_HMAC_SHA256_ENABLED  - Oberon HMAC using SHA-256
 

// <i> Oberon backend implementation for HMAC using SHA-256.

#ifndef NRF_CRYPTO_BACKEND_OBERON_HMAC_SHA256_ENABLED
#define NRF_CRYPTO_BACKEND_OBERON_HMAC_SHA256_ENABLED 0
#endif

// <q> NRF_CRYPTO_BACKEND_OBERON_HMAC_SHA512_ENABLED  - Oberon HMAC using SHA-512
 

// <i> Oberon backend implementation for HMAC using SHA-512.

#ifndef NRF_CRYPTO_BACKEND_OBERON_HMAC_SHA512_ENABLED
#define NRF_CRYPTO_BACKEND_OBERON_HMAC_SHA512_ENABLED 0
#endif

// </e>

// <e> NRF_CRYPTO_BACKEND_OPTIGA_ENABLED - Enable the nrf_crypto Optiga Trust X backend.

// <i> Enables the nrf_crypto backend for Optiga Trust X devices.
//==========================================================
#ifndef NRF_CRYPTO_BACKEND_OPTIGA_ENABLED
#define NRF_CRYPTO_BACKEND_OPTIGA_ENABLED 0
#endif
// <q> NRF_CRYPTO_BACKEND_OPTIGA_RNG_ENABLED  - Optiga backend support for RNG
 

// <i> The Optiga backend provide external chip RNG.

#ifndef NRF_CRYPTO_BACKEND_OPTIGA_RNG_ENABLED
#define NRF_CRYPTO_BACKEND_OPTIGA_RNG_ENABLED 0
#endif

// <q> NRF_CRYPTO_BACKEND_OPTIGA_ECC_SECP256R1_ENABLED  - Optiga backend support for ECC secp256r1
 

// <i> The Optiga backend provide external chip ECC using secp256r1.

#ifndef NRF_CRYPTO_BACKEND_OPTIGA_ECC_SECP256R1_ENABLED
#define NRF_CRYPTO_BACKEND_OPTIGA_ECC_SECP256R1_ENABLED 1
#endif

// </e>

// <q> NRF_CRYPTO_CURVE25519_BIG_ENDIAN_ENABLED  - Big-endian byte order in raw Curve25519 data
 

// <i> Enable big-endian byte order in Curve25519 API, if set to 1. Use little-endian, if set to 0.

#ifndef NRF_CRYPTO_CURVE25519_BIG_ENDIAN_ENABLED
#define NRF_CRYPTO_CURVE25519_BIG_ENDIAN_ENABLED 0
#endif

// </e>

// <h> nrf_crypto_rng - RNG Configuration

//==========================================================
// <q> NRF_CRYPTO_RNG_STATIC_MEMORY_BUFFERS_ENABLED  - Use static memory buffers for context and temporary init buffer.
 

// <i> Always recommended when using the nRF HW RNG as the context and temporary buffers are small. Consider disabling if using the CC310 RNG in a RAM constrained application. In this case, memory must be provided to nrf_crypto_rng_init, or it can be allocated internally provided that NRF_CRYPTO_ALLOCATOR does not allocate memory on the stack.

#ifndef NRF_CRYPTO_RNG_STATIC_MEMORY_BUFFERS_ENABLED
#define NRF_CRYPTO_RNG_STATIC_MEMORY_BUFFERS_ENABLED 1
#endif

// <q> NRF_CRYPTO_RNG_AUTO_INIT_ENABLED  - Initialize the RNG module automatically when nrf_crypto is initialized.
 

// <i> Automatic initialization is only supported with static or internally allocated context and temporary memory.

#ifndef NRF_CRYPTO_RNG_AUTO_INIT_ENABLED
#define NRF_CRYPTO_RNG_AUTO_INIT_ENABLED 1
#endif

// </h> 
//==========================================================

// </h> 
//==========================================================

// <h> nRF_DFU 

//==========================================================
// <h> DFU security - nrf_dfu_validation - DFU validation

//==========================================================
// <q> NRF_DFU_APP_ACCEPT_SAME_VERSION  - Whether to accept application upgrades with the same version as the current application.
 

// <i> This applies to application updates, and possibly to SoftDevice updates.
// <i> Bootloader upgrades always require higher versions. SoftDevice upgrades
// <i> look at the sd_req field independently of this config.
// <i> Disabling this protects against replay attacks wearing out the flash of the device.
// <i> This config only has an effect when NRF_DFU_APP_DOWNGRADE_PREVENTION is enabled.

#ifndef NRF_DFU_APP_ACCEPT_SAME_VERSION
#define NRF_DFU_APP_ACCEPT_SAME_VERSION 1
#endif

// <q> NRF_DFU_APP_DOWNGRADE_PREVENTION  - Check the firmware version and SoftDevice requirements of application (and SoftDevice) updates.
 

// <i> Whether to check the incoming version against the version of the existing app and/or
// <i> the incoming SoftDevice requirements against the existing SoftDevice.
// <i> This applies to application updates, and possibly to SoftDevice updates.
// <i> Disabling this causes the checks to always ignore the incoming firmware version and
// <i> to ignore the SoftDevice requirements if the first requirement is 0.
// <i> This does not apply the bootloader updates. If the bootloader depends on the SoftDevice
// <i> e.g. for BLE transport, this does not apply to SoftDevice updates.
// <i> See @ref lib_bootloader_dfu_validation for more information.
// <i> When signed updates are required, version checking should always be enabled.

#ifndef NRF_DFU_APP_DOWNGRADE_PREVENTION
#define NRF_DFU_APP_DOWNGRADE_PREVENTION 1
#endif

// <q> NRF_DFU_EXTERNAL_APP_VERSIONING  - Require versioning for external applications.
 

// <i> This configuration is only used if NRF_DFU_SUPPORTS_EXTERNAL_APP is set to 1.
// <i> Setting this will require that any FW images using the FW upgrade type 
// <i> DFU_FW_TYPE_EXTERNAL_APPLICATION must follow a monotonic versioning scheme
// <i> where the FW version of an upgrade must always be larger than the previously stored 
// <i> FW version.

#ifndef NRF_DFU_EXTERNAL_APP_VERSIONING
#define NRF_DFU_EXTERNAL_APP_VERSIONING 1
#endif

// <q> NRF_DFU_FORCE_DUAL_BANK_APP_UPDATES  - Accept only dual-bank application updates.
 

// <i> If not enabled then if there is not enough space to perform dual-bank update
// <i> application is deleted and single-bank update is performed. In case it is considered
// <i> security concern user can prefer to discard update request rather than overwrite
// <i> current application.

#ifndef NRF_DFU_FORCE_DUAL_BANK_APP_UPDATES
#define NRF_DFU_FORCE_DUAL_BANK_APP_UPDATES 0
#endif

// <o> NRF_DFU_HW_VERSION - Device hardware version. 
// <i> This is used to determine if given update is targeting the device.
// <i> It is checked against the hw_version value in the init packet

#ifndef NRF_DFU_HW_VERSION
#define NRF_DFU_HW_VERSION 52
#endif

// <q> NRF_DFU_REQUIRE_SIGNED_APP_UPDATE  - Require a valid signature to update the application or SoftDevice.
 

#ifndef NRF_DFU_REQUIRE_SIGNED_APP_UPDATE
#define NRF_DFU_REQUIRE_SIGNED_APP_UPDATE 1
#endif

// <q> NRF_DFU_SINGLE_BANK_APP_UPDATES  - Place the application and the SoftDevice directly where they are supposed to be.
 

// <i> Note that this creates security concerns when signing and  version checks
// <i> are enabled. An attacker will be able to delete (but not replace)
// <i> the current app or SoftDevice without knowing the signature key.

#ifndef NRF_DFU_SINGLE_BANK_APP_UPDATES
#define NRF_DFU_SINGLE_BANK_APP_UPDATES 0
#endif

// </h> 
//==========================================================

// <q> NRF_DFU_SETTINGS_COMPATIBILITY_MODE  - nrf_dfu_settings - DFU Settings
 

#ifndef NRF_DFU_SETTINGS_COMPATIBILITY_MODE
#define NRF_DFU_SETTINGS_COMPATIBILITY_MODE 1
#endif

// <h> nrf_dfu - Device Firmware Upgrade

//==========================================================
// <h> DFU transport 

//==========================================================
// <e> NRF_DFU_TRANSPORT_ANT - ANT transport settings
//==========================================================
#ifndef NRF_DFU_TRANSPORT_ANT
#define NRF_DFU_TRANSPORT_ANT 0
#endif
// <o> NRF_DFU_ANT_MTU - MTU size used for firmware bursts. 
// <i> Sets the maximum burst size used for DFU write commands.

#ifndef NRF_DFU_ANT_MTU
#define NRF_DFU_ANT_MTU 1024
#endif

// <h> ANT DFU buffers 

//==========================================================
// <e> NRF_DFU_ANT_BUFFERS_OVERRIDE 

// <i> Check this option to override the default number of buffers.
//==========================================================
#ifndef NRF_DFU_ANT_BUFFERS_OVERRIDE
#define NRF_DFU_ANT_BUFFERS_OVERRIDE 0
#endif
// <o> NRF_DFU_ANT_BUFFERS - Number of buffers in the ANT transport. 
// <i> Number of buffers to store incoming data while it is being written to flash.
// <i> Reduce this value to save RAM. If this value is too low, the DFU process will fail.

#ifndef NRF_DFU_ANT_BUFFERS
#define NRF_DFU_ANT_BUFFERS 8
#endif

// </e>

// </h> 
//==========================================================

// <h> ANT DFU Channel Configuration 

//==========================================================
// <o> NRF_DFU_ANT_RF_FREQ - DFU RF channel. 
#ifndef NRF_DFU_ANT_RF_FREQ
#define NRF_DFU_ANT_RF_FREQ 66
#endif

// <o> NRF_DFU_ANT_DEV_TYPE - Device type field to use for DFU channel id. 
#ifndef NRF_DFU_ANT_DEV_TYPE
#define NRF_DFU_ANT_DEV_TYPE 10
#endif

// <o> NRF_DFU_ANT_CHANNEL_PERIOD - Channel period of DFU ANT channel. 
#ifndef NRF_DFU_ANT_CHANNEL_PERIOD
#define NRF_DFU_ANT_CHANNEL_PERIOD 2048
#endif

// </h> 
//==========================================================

// </e>

// <e> NRF_DFU_TRANSPORT_BLE - BLE transport settings
//==========================================================
#ifndef NRF_DFU_TRANSPORT_BLE
#define NRF_DFU_TRANSPORT_BLE 1
#endif
// <q> NRF_DFU_BLE_SKIP_SD_INIT  - Skip the SoftDevice and interrupt vector table initialization.
 

#ifndef NRF_DFU_BLE_SKIP_SD_INIT
#define NRF_DFU_BLE_SKIP_SD_INIT 0
#endif

// <s> NRF_DFU_BLE_ADV_NAME - Default advertising name.
#ifndef NRF_DFU_BLE_ADV_NAME
#define NRF_DFU_BLE_ADV_NAME "Vario DFU"
#endif

// <o> NRF_DFU_BLE_ADV_INTERVAL - Advertising interval (in units of 0.625 ms) 
#ifndef NRF_DFU_BLE_ADV_INTERVAL
#define NRF_DFU_BLE_ADV_INTERVAL 40
#endif

// <h> BLE DFU security 

//==========================================================
// <q> NRF_DFU_BLE_REQUIRES_BONDS  - Require bond with peer.
 

#ifndef NRF_DFU_BLE_REQUIRES_BONDS
#define NRF_DFU_BLE_REQUIRES_BONDS 0
#endif

// </h> 
//==========================================================

// <h> BLE DFU connection 

//==========================================================
// <o> NRF_DFU_BLE_MIN_CONN_INTERVAL - Minimum connection interval (units). 
// <i> Minimum GAP connection interval, in 1.25 ms units.

#ifndef NRF_DFU_BLE_MIN_CONN_INTERVAL
#define NRF_DFU_BLE_MIN_CONN_INTERVAL 12
#endif

// <o> NRF_DFU_BLE_MAX_CONN_INTERVAL - Maximum connection interval (units). 
// <i> Maximum GAP connection interval, in 1.25 ms units.

#ifndef NRF_DFU_BLE_MAX_CONN_INTERVAL
#define NRF_DFU_BLE_MAX_CONN_INTERVAL 12
#endif

// <o> NRF_DFU_BLE_CONN_SUP_TIMEOUT_MS - Supervision timeout (ms). 
// <i> GAP connection supervision timeout, in milliseconds.

#ifndef NRF_DFU_BLE_CONN_SUP_TIMEOUT_MS
#define NRF_DFU_BLE_CONN_SUP_TIMEOUT_MS 6000
#endif

// </h> 
//==========================================================

// <h> BLE DFU buffers 

//==========================================================
// <e> NRF_DFU_BLE_BUFFERS_OVERRIDE 

// <i> Check this option to override the default number of buffers.
//==========================================================
#ifndef NRF_DFU_BLE_BUFFERS_OVERRIDE
#define NRF_DFU_BLE_BUFFERS_OVERRIDE 0
#endif
// <o> NRF_DFU_BLE_BUFFERS - Number of buffers in the BLE transport. 
// <i> Number of buffers to store incoming data while it is being written to flash.
// <i> Reduce this value to save RAM. If this value is too low, the DFU process will fail.

#ifndef NRF_DFU_BLE_BUFFERS
#define NRF_DFU_BLE_BUFFERS 8
#endif

// </e>

// </h> 
//==========================================================

// </e>

// </h> 
//==========================================================

// <h> DFU protocol 

//==========================================================
// <q> NRF_DFU_PROTOCOL_FW_VERSION_MSG  - Firmware version message support.
 

// <i> Firmware version message support.
// <i> If disabled, firmware version requests will return NRF_DFU_RES_CODE_OP_CODE_NOT_SUPPORTED.

#ifndef NRF_DFU_PROTOCOL_FW_VERSION_MSG
#define NRF_DFU_PROTOCOL_FW_VERSION_MSG 1
#endif

// <q> NRF_DFU_PROTOCOL_REDUCED  - Reduced protocol opcode selection.
 

// <i> Only support a minimal set of opcodes; return NRF_DFU_RES_CODE_OP_CODE_NOT_SUPPORTED 
// <i> for unsupported opcodes. The supported opcodes are:NRF_DFU_OP_OBJECT_CREATE, 
// <i> NRF_DFU_OP_OBJECT_EXECUTE, NRF_DFU_OP_OBJECT_SELECT, NRF_DFU_OP_OBJECT_WRITE, 
// <i> NRF_DFU_OP_CRC_GET, NRF_DFU_OP_RECEIPT_NOTIF_SET, and NRF_DFU_OP_ABORT. 
// <i> This reduced feature set is used by the BLE transport to reduce flash usage.

#ifndef NRF_DFU_PROTOCOL_REDUCED
#define NRF_DFU_PROTOCOL_REDUCED 1
#endif

// <q> NRF_DFU_PROTOCOL_VERSION_MSG  - Protocol version message support.
 

// <i> Protocol version message support.
// <i> If disabled, protocol version requests will return NRF_DFU_RES_CODE_OP_CODE_NOT_SUPPORTED.

#ifndef NRF_DFU_PROTOCOL_VERSION_MSG
#define NRF_DFU_PROTOCOL_VERSION_MSG 1
#endif

// </h> 
//==========================================================

// <h> Misc DFU settings 

//==========================================================
// <o> NRF_DFU_APP_DATA_AREA_SIZE - The size (in bytes) of the flash area reserved for application data. 
// <i> This area is found at the end of the application area, next to the start of
// <i> the bootloader. This area will not be erased by the bootloader during a
// <i> firmware upgrade. The size must be a multiple of the flash page size.

#ifndef NRF_DFU_APP_DATA_AREA_SIZE
#define NRF_DFU_APP_DATA_AREA_SIZE 12288
#endif

// <q> NRF_DFU_IN_APP  - Specifies that this code is in the app, not the bootloader, so some settings are off-limits.
 

// <i> Enable this to disable writing to areas of the settings that are protected
// <i> by the bootlader. If this is not enabled in the app, certain settings write
// <i> operations will cause HardFaults or will be ignored. Enabling this option
// <i> also causes postvalidation to be disabled since this is meant to be done
// <i> in the bootloader. NRF_BL_DFU_ALLOW_UPDATE_FROM_APP must be enabled in the bootloader.

#ifndef NRF_DFU_IN_APP
#define NRF_DFU_IN_APP 0
#endif

// <q> NRF_DFU_SAVE_PROGRESS_IN_FLASH  - Save DFU progress in flash.
 

// <i> Save DFU progress to flash so that it can be resumed if interrupted, instead of being restarted.
// <i> Keep this setting disabled to maximize transfer speed and minimize flash wear.
// <i> The init packet is always saved in flash, regardless of this setting.

#ifndef NRF_DFU_SAVE_PROGRESS_IN_FLASH
#define NRF_DFU_SAVE_PROGRESS_IN_FLASH 0
#endif

// <q> NRF_DFU_SUPPORTS_EXTERNAL_APP  - [Experimental] Support for external app.
 

// <i> External apps are apps that will not be activated. They can 
// <i> e.g. be apps to be sent to a third party. External app updates 
// <i> are verified upon reception, but will remain in bank 1, and 
// <i> will never be booted. An external app will be overwritten if 
// <i> a new DFU procedure is performed. Note: This functionality is 
// <i> experimental and not yet used in any examples.

#ifndef NRF_DFU_SUPPORTS_EXTERNAL_APP
#define NRF_DFU_SUPPORTS_EXTERNAL_APP 0
#endif

// </h> 
//==========================================================

// </h> 
//==========================================================

// </h> 
//==========================================================

// <h> nRF_Libraries 

//==========================================================
// <e> APP_SCHEDULER_ENABLED - app_scheduler - Events scheduler
//==========================================================
#ifndef APP_SCHEDULER_ENABLED
#define APP_SCHEDULER_ENABLED 1
#endif
// <q> APP_SCHEDULER_WITH_PAUSE  - Enabling pause feature
 

#ifndef APP_SCHEDULER_WITH_PAUSE
#define APP_SCHEDULER_WITH_PAUSE 0
#endif

// <q> APP_SCHEDULER_WITH_PROFILER  - Enabling scheduler profiling
 

#ifndef APP_SCHEDULER_WITH_PROFILER
#define APP_SCHEDULER_WITH_PROFILER 0
#endif

// </e>

// <q> CRC32_ENABLED  - crc32 - CRC32 calculation routines
 

#ifndef CRC32_ENABLED
#define CRC32_ENABLED 1
#endif

// <e> MEM_MANAGER_ENABLED - mem_manager - Dynamic memory allocator
//==========================================================
#ifndef MEM_MANAGER_ENABLED
#define MEM_MANAGER_ENABLED 1
#endif
// <o> MEMORY_MANAGER_SMALL_BLOCK_COUNT - Size of each memory blocks identified as 'small' block.  <0-255> 


#ifndef MEMORY_MANAGER_SMALL_BLOCK_COUNT
#define MEMORY_MANAGER_SMALL_BLOCK_COUNT 1
#endif

// <o> MEMORY_MANAGER_SMALL_BLOCK_SIZE -  Size of each memory blocks identified as 'small' block. 
// <i>  Size of each memory blocks identified as 'small' block. Memory block are recommended to be word-sized.

#ifndef MEMORY_MANAGER_SMALL_BLOCK_SIZE
#define MEMORY_MANAGER_SMALL_BLOCK_SIZE 32
#endif

// <o> MEMORY_MANAGER_MEDIUM_BLOCK_COUNT - Size of each memory blocks identified as 'medium' block.  <0-255> 


#ifndef MEMORY_MANAGER_MEDIUM_BLOCK_COUNT
#define MEMORY_MANAGER_MEDIUM_BLOCK_COUNT 0
#endif

// <o> MEMORY_MANAGER_MEDIUM_BLOCK_SIZE -  Size of each memory blocks identified as 'medium' block. 
// <i>  Size of each memory blocks identified as 'medium' block. Memory block are recommended to be word-sized.

#ifndef MEMORY_MANAGER_MEDIUM_BLOCK_SIZE
#define MEMORY_MANAGER_MEDIUM_BLOCK_SIZE 256
#endif

// <o> MEMORY_MANAGER_LARGE_BLOCK_COUNT - Size of each memory blocks identified as 'large' block.  <0-255> 


#ifndef MEMORY_MANAGER_LARGE_BLOCK_COUNT
#define MEMORY_MANAGER_LARGE_BLOCK_COUNT 0
#endif

// <o> MEMORY_MANAGER_LARGE_BLOCK_SIZE -  Size of each memory blocks identified as 'large' block. 
// <i>  Size of each memory blocks identified as 'large' block. Memory block are recommended to be word-sized.

#ifndef MEMORY_MANAGER_LARGE_BLOCK_SIZE
#define MEMORY_MANAGER_LARGE_BLOCK_SIZE 256
#endif

// <o> MEMORY_MANAGER_XLARGE_BLOCK_COUNT - Size of each memory blocks identified as 'extra large' block.  <0-255> 


#ifndef MEMORY_MANAGER_XLARGE_BLOCK_COUNT
#define MEMORY_MANAGER_XLARGE_BLOCK_COUNT 0
#endif

// <o> MEMORY_MANAGER_XLARGE_BLOCK_SIZE -  Size of each memory blocks identified as 'extra large' block. 
// <i>  Size of each memory blocks identified as 'extra large' block. Memory block are recommended to be word-sized.

#ifndef MEMORY_MANAGER_XLARGE_BLOCK_SIZE
#define MEMORY_MANAGER_XLARGE_BLOCK_SIZE 1320
#endif

// <o> MEMORY_MANAGER_XXLARGE_BLOCK_COUNT - Size of each memory blocks identified as 'extra extra large' block.  <0-255> 


#ifndef MEMORY_MANAGER_XXLARGE_BLOCK_COUNT
#define MEMORY_MANAGER_XXLARGE_BLOCK_COUNT 0
#endif

// <o> MEMORY_MANAGER_XXLARGE_BLOCK_SIZE -  Size of each memory blocks identified as 'extra extra large' block. 
// <i>  Size of each memory blocks identified as 'extra extra large' block. Memory block are recommended to be word-sized.

#ifndef MEMORY_MANAGER_XXLARGE_BLOCK_SIZE
#define MEMORY_MANAGER_XXLARGE_BLOCK_SIZE 3444
#endif

// <o> MEMORY_MANAGER_XSMALL_BLOCK_COUNT - Size of each memory blocks identified as 'extra small' block.  <0-255> 


#ifndef MEMORY_MANAGER_XSMALL_BLOCK_COUNT
#define MEMORY_MANAGER_XSMALL_BLOCK_COUNT 0
#endif

// <o> MEMORY_MANAGER_XSMALL_BLOCK_SIZE -  Size of each memory blocks identified as 'extra small' block. 
// <i>  Size of each memory blocks identified as 'extra large' block. Memory block are recommended to be word-sized.

#ifndef MEMORY_MANAGER_XSMALL_BLOCK_SIZE
#define MEMORY_MANAGER_XSMALL_BLOCK_SIZE 64
#endif

// <o> MEMORY_MANAGER_XXSMALL_BLOCK_COUNT - Size of each memory blocks identified as 'extra extra small' block.  <0-255> 


#ifndef MEMORY_MANAGER_XXSMALL_BLOCK_COUNT
#define MEMORY_MANAGER_XXSMALL_BLOCK_COUNT 0
#endif

// <o> MEMORY_MANAGER_XXSMALL_BLOCK_SIZE -  Size of each memory blocks identified as 'extra extra small' block. 
// <i>  Size of each memory blocks identified as 'extra extra small' block. Memory block are recommended to be word-sized.

#ifndef MEMORY_MANAGER_XXSMALL_BLOCK_SIZE
#define MEMORY_MANAGER_XXSMALL_BLOCK_SIZE 32
#endif

// <e> MEM_MANAGER_CONFIG_LOG_ENABLED - Enables logging in the module.
//==========================================================
#ifndef MEM_MANAGER_CONFIG_LOG_ENABLED
#define MEM_MANAGER_CONFIG_LOG_ENABLED 0
#endif
// <o> MEM_MANAGER_CONFIG_LOG_LEVEL  - Default Severity level
 
// <0=> Off 
// <1=> Error 
// <2=> Warning 
// <3=> Info 
// <4=> Debug 

#ifndef MEM_MANAGER_CONFIG_LOG_LEVEL
#define MEM_MANAGER_CONFIG_LOG_LEVEL 3
#endif

// <o> MEM_MANAGER_CONFIG_INFO_COLOR  - ANSI escape code prefix.
 
// <0=> Default 
// <1=> Black 
// <2=> Red 
// <3=> Green 
// <4=> Yellow 
// <5=> Blue 
// <6=> Magenta 
// <7=> Cyan 
// <8=> White 

#ifndef MEM_MANAGER_CONFIG_INFO_COLOR
#define MEM_MANAGER_CONFIG_INFO_COLOR 0
#endif

// <o> MEM_MANAGER_CONFIG_DEBUG_COLOR  - ANSI escape code prefix.
 
// <0=> Default 
// <1=> Black 
// <2=> Red 
// <3=> Green 
// <4=> Yellow 
// <5=> Blue 
// <6=> Magenta 
// <7=> Cyan 
// <8=> White 

#ifndef MEM_MANAGER_CONFIG_DEBUG_COLOR
#define MEM_MANAGER_CONFIG_DEBUG_COLOR 0
#endif

// </e>

// <q> MEM_MANAGER_DISABLE_API_PARAM_CHECK  - Disable API parameter checks in the module.
 

#ifndef MEM_MANAGER_DISABLE_API_PARAM_CHECK
#define MEM_MANAGER_DISABLE_API_PARAM_CHECK 0
#endif

// </e>

// <e> NRF_BALLOC_ENABLED - nrf_balloc - Block allocator module
//==========================================================
#ifndef NRF_BALLOC_ENABLED
#define NRF_BALLOC_ENABLED 1
#endif
// <e> NRF_BALLOC_CONFIG_DEBUG_ENABLED - Enables debug mode in the module.
//==========================================================
#ifndef NRF_BALLOC_CONFIG_DEBUG_ENABLED
#define NRF_BALLOC_CONFIG_DEBUG_ENABLED 0
#endif
// <o> NRF_BALLOC_CONFIG_HEAD_GUARD_WORDS - Number of words used as head guard.  <0-255> 


#ifndef NRF_BALLOC_CONFIG_HEAD_GUARD_WORDS
#define NRF_BALLOC_CONFIG_HEAD_GUARD_WORDS 1
#endif

// <o> NRF_BALLOC_CONFIG_TAIL_GUARD_WORDS - Number of words used as tail guard.  <0-255> 


#ifndef NRF_BALLOC_CONFIG_TAIL_GUARD_WORDS
#define NRF_BALLOC_CONFIG_TAIL_GUARD_WORDS 1
#endif

// <q> NRF_BALLOC_CONFIG_BASIC_CHECKS_ENABLED  - Enables basic checks in this module.
 

#ifndef NRF_BALLOC_CONFIG_BASIC_CHECKS_ENABLED
#define NRF_BALLOC_CONFIG_BASIC_CHECKS_ENABLED 0
#endif

// <q> NRF_BALLOC_CONFIG_DOUBLE_FREE_CHECK_ENABLED  - Enables double memory free check in this module.
 

#ifndef NRF_BALLOC_CONFIG_DOUBLE_FREE_CHECK_ENABLED
#define NRF_BALLOC_CONFIG_DOUBLE_FREE_CHECK_ENABLED 0
#endif

// <q> NRF_BALLOC_CONFIG_DATA_TRASHING_CHECK_ENABLED  - Enables free memory corruption check in this module.
 

#ifndef NRF_BALLOC_CONFIG_DATA_TRASHING_CHECK_ENABLED
#define NRF_BALLOC_CONFIG_DATA_TRASHING_CHECK_ENABLED 0
#endif

// <q> NRF_BALLOC_CLI_CMDS  - Enable CLI commands specific to the module
 

#ifndef NRF_BALLOC_CLI_CMDS
#define NRF_BALLOC_CLI_CMDS 0
#endif

// </e>

// </e>

// <e> NRF_FSTORAGE_ENABLED - nrf_fstorage - Flash abstraction library
//==========================================================
#ifndef NRF_FSTORAGE_ENABLED
#define NRF_FSTORAGE_ENABLED 1
#endif
// <h> nrf_fstorage - Common settings

// <i> Common settings to all fstorage implementations
//==========================================================
// <q> NRF_FSTORAGE_PARAM_CHECK_DISABLED  - Disable user input validation
 

// <i> If selected, use ASSERT to validate user input.
// <i> This effectively removes user input validation in production code.
// <i> Recommended setting: OFF, only enable this setting if size is a major concern.

#ifndef NRF_FSTORAGE_PARAM_CHECK_DISABLED
#define NRF_FSTORAGE_PARAM_CHECK_DISABLED 1
#endif

// </h> 
//==========================================================

// <h> nrf_fstorage_sd - Implementation using the SoftDevice

// <i> Configuration options for the fstorage implementation using the SoftDevice
//==========================================================
// <o> NRF_FSTORAGE_SD_QUEUE_SIZE - Size of the internal queue of operations 
// <i> Increase this value if API calls frequently return the error @ref NRF_ERROR_NO_MEM.

#ifndef NRF_FSTORAGE_SD_QUEUE_SIZE
#define NRF_FSTORAGE_SD_QUEUE_SIZE 16
#endif

// <o> NRF_FSTORAGE_SD_MAX_RETRIES - Maximum number of attempts at executing an operation when the SoftDevice is busy 
// <i> Increase this value if events frequently return the @ref NRF_ERROR_TIMEOUT error.
// <i> The SoftDevice might fail to schedule flash access due to high BLE activity.

#ifndef NRF_FSTORAGE_SD_MAX_RETRIES
#define NRF_FSTORAGE_SD_MAX_RETRIES 8
#endif

// <o> NRF_FSTORAGE_SD_MAX_WRITE_SIZE - Maximum number of bytes to be written to flash in a single operation 
// <i> This value must be a multiple of four.
// <i> Lowering this value can increase the chances of the SoftDevice being able to execute flash operations in between radio activity.
// <i> This value is bound by the maximum number of bytes that can be written to flash in a single call to @ref sd_flash_write.
// <i> That is 1024 bytes for nRF51 ICs and 4096 bytes for nRF52 ICs.

#ifndef NRF_FSTORAGE_SD_MAX_WRITE_SIZE
#define NRF_FSTORAGE_SD_MAX_WRITE_SIZE 20
#endif

// </h> 
//==========================================================

// </e>

// <q> NRF_MEMOBJ_ENABLED  - nrf_memobj - Linked memory allocator module
 

#ifndef NRF_MEMOBJ_ENABLED
#define NRF_MEMOBJ_ENABLED 1
#endif

// <e> NRF_QUEUE_ENABLED - nrf_queue - Queue module
//==========================================================
#ifndef NRF_QUEUE_ENABLED
#define NRF_QUEUE_ENABLED 0
#endif
// <q> NRF_QUEUE_CLI_CMDS  - Enable CLI commands specific to the module
 

#ifndef NRF_QUEUE_CLI_CMDS
#define NRF_QUEUE_CLI_CMDS 0
#endif

// </e>

// <q> NRF_SECTION_ITER_ENABLED  - nrf_section_iter - Section iterator
 

#ifndef NRF_SECTION_ITER_ENABLED
#define NRF_SECTION_ITER_ENABLED 1
#endif

// <q> NRF_STRERROR_ENABLED  - nrf_strerror - Library for converting error code to string.
 

#ifndef NRF_STRERROR_ENABLED
#define NRF_STRERROR_ENABLED 1
#endif

// <h> nrf_fprintf - fprintf function.

//==========================================================
// <q> NRF_FPRINTF_ENABLED  - Enable/disable fprintf module.
 

#ifndef NRF_FPRINTF_ENABLED
#define NRF_FPRINTF_ENABLED 1
#endif

// <q> NRF_FPRINTF_FLAG_AUTOMATIC_CR_ON_LF_ENABLED  - For each printed LF, function will add CR.
 

#ifndef NRF_FPRINTF_FLAG_AUTOMATIC_CR_ON_LF_ENABLED
#define NRF_FPRINTF_FLAG_AUTOMATIC_CR_ON_LF_ENABLED 1
#endif

// <q> NRF_FPRINTF_DOUBLE_ENABLED  - Enable IEEE-754 double precision formatting.
 

#ifndef NRF_FPRINTF_DOUBLE_ENABLED
#define NRF_FPRINTF_DOUBLE_ENABLED 0
#endif

// </h> 
//==========================================================

// </h> 
//==========================================================

// <h> nRF_Log 

//==========================================================
// <e> NRF_LOG_ENABLED - nrf_log - Logger
//==========================================================
#ifndef NRF_LOG_ENABLED
#define NRF_LOG_ENABLED 0
#endif
// <h> Log message pool - Configuration of log message pool

//==========================================================
// <o> NRF_LOG_MSGPOOL_ELEMENT_SIZE - Size of a single element in the pool of memory objects. 
// <i> If a small value is set, then performance of logs processing
// <i> is degraded because data is fragmented. Bigger value impacts
// <i> RAM memory utilization. The size is set to fit a message with
// <i> a timestamp and up to 2 arguments in a single memory object.

#ifndef NRF_LOG_MSGPOOL_ELEMENT_SIZE
#define NRF_LOG_MSGPOOL_ELEMENT_SIZE 20
#endif

// <o> NRF_LOG_MSGPOOL_ELEMENT_COUNT - Number of elements in the pool of memory objects 
// <i> If a small value is set, then it may lead to a deadlock
// <i> in certain cases if backend has high latency and holds
// <i> multiple messages for long time. Bigger value impacts
// <i> RAM memory usage.

#ifndef NRF_LOG_MSGPOOL_ELEMENT_COUNT
#define NRF_LOG_MSGPOOL_ELEMENT_COUNT 8
#endif

// </h> 
//==========================================================

// <q> NRF_LOG_ALLOW_OVERFLOW  - Configures behavior when circular buffer is full.
 

// <i> If set then oldest logs are overwritten. Otherwise a 
// <i> marker is injected informing about overflow.

#ifndef NRF_LOG_ALLOW_OVERFLOW
#define NRF_LOG_ALLOW_OVERFLOW 1
#endif

// <o> NRF_LOG_BUFSIZE  - Size of the buffer for storing logs (in bytes).
 

// <i> Must be power of 2 and multiple of 4.
// <i> If NRF_LOG_DEFERRED = 0 then buffer size can be reduced to minimum.
// <128=> 128 
// <256=> 256 
// <512=> 512 
// <1024=> 1024 
// <2048=> 2048 
// <4096=> 4096 
// <8192=> 8192 
// <16384=> 16384 

#ifndef NRF_LOG_BUFSIZE
#define NRF_LOG_BUFSIZE 1024
#endif

// <q> NRF_LOG_CLI_CMDS  - Enable CLI commands for the module.
 

#ifndef NRF_LOG_CLI_CMDS
#define NRF_LOG_CLI_CMDS 0
#endif

// <o> NRF_LOG_DEFAULT_LEVEL  - Default Severity level
 
// <0=> Off 
// <1=> Error 
// <2=> Warning 
// <3=> Info 
// <4=> Debug 

#ifndef NRF_LOG_DEFAULT_LEVEL
#define NRF_LOG_DEFAULT_LEVEL 3
#endif

// <q> NRF_LOG_DEFERRED  - Enable deffered logger.
 

// <i> Log data is buffered and can be processed in idle.

#ifndef NRF_LOG_DEFERRED
#define NRF_LOG_DEFERRED 1
#endif

// <q> NRF_LOG_FILTERS_ENABLED  - Enable dynamic filtering of logs.
 

#ifndef NRF_LOG_FILTERS_ENABLED
#define NRF_LOG_FILTERS_ENABLED 0
#endif

// <q> NRF_LOG_NON_DEFFERED_CRITICAL_REGION_ENABLED  - Enable use of critical region for non deffered mode when flushing logs.
 

// <i> When enabled NRF_LOG_FLUSH is called from critical section when non deffered mode is used.
// <i> Log output will never be corrupted as access to the log backend is exclusive
// <i> but system will spend significant amount of time in critical section

#ifndef NRF_LOG_NON_DEFFERED_CRITICAL_REGION_ENABLED
#define NRF_LOG_NON_DEFFERED_CRITICAL_REGION_ENABLED 0
#endif

// <o> NRF_LOG_STR_PUSH_BUFFER_SIZE  - Size of the buffer dedicated for strings stored using @ref NRF_LOG_PUSH.
 
// <16=> 16 
// <32=> 32 
// <64=> 64 
// <128=> 128 
// <256=> 256 
// <512=> 512 
// <1024=> 1024 

#ifndef NRF_LOG_STR_PUSH_BUFFER_SIZE
#define NRF_LOG_STR_PUSH_BUFFER_SIZE 128
#endif

// <o> NRF_LOG_STR_PUSH_BUFFER_SIZE  - Size of the buffer dedicated for strings stored using @ref NRF_LOG_PUSH.
 
// <16=> 16 
// <32=> 32 
// <64=> 64 
// <128=> 128 
// <256=> 256 
// <512=> 512 
// <1024=> 1024 

#ifndef NRF_LOG_STR_PUSH_BUFFER_SIZE
#define NRF_LOG_STR_PUSH_BUFFER_SIZE 128
#endif

// <e> NRF_LOG_USES_COLORS - If enabled then ANSI escape code for colors is prefixed to every string
//==========================================================
#ifndef NRF_LOG_USES_COLORS
#define NRF_LOG_USES_COLORS 0
#endif
// <o> NRF_LOG_COLOR_DEFAULT  - ANSI escape code prefix.
 
// <0=> Default 
// <1=> Black 
// <2=> Red 
// <3=> Green 
// <4=> Yellow 
// <5=> Blue 
// <6=> Magenta 
// <7=> Cyan 
// <8=> White 

#ifndef NRF_LOG_COLOR_DEFAULT
#define NRF_LOG_COLOR_DEFAULT 0
#endif

// <o> NRF_LOG_ERROR_COLOR  - ANSI escape code prefix.
 
// <0=> Default 
// <1=> Black 
// <2=> Red 
// <3=> Green 
// <4=> Yellow 
// <5=> Blue 
// <6=> Magenta 
// <7=> Cyan 
// <8=> White 

#ifndef NRF_LOG_ERROR_COLOR
#define NRF_LOG_ERROR_COLOR 2
#endif

// <o> NRF_LOG_WARNING_COLOR  - ANSI escape code prefix.
 
// <0=> Default 
// <1=> Black 
// <2=> Red 
// <3=> Green 
// <4=> Yellow 
// <5=> Blue 
// <6=> Magenta 
// <7=> Cyan 
// <8=> White 

#ifndef NRF_LOG_WARNING_COLOR
#define NRF_LOG_WARNING_COLOR 4
#endif

// </e>

// <e> NRF_LOG_USES_TIMESTAMP - Enable timestamping

// <i> Function for getting the timestamp is provided by the user
//==========================================================
#ifndef NRF_LOG_USES_TIMESTAMP
#define NRF_LOG_USES_TIMESTAMP 0
#endif
// <o> NRF_LOG_TIMESTAMP_DEFAULT_FREQUENCY - Default frequency of the timestamp (in Hz) or 0 to use app_timer frequency. 
#ifndef NRF_LOG_TIMESTAMP_DEFAULT_FREQUENCY
#define NRF_LOG_TIMESTAMP_DEFAULT_FREQUENCY 0
#endif

// </e>

// <h> nrf_log module configuration 

//==========================================================
// <h> nrf_log in nRF_Core 

//==========================================================
// <e> NRF_MPU_LIB_CONFIG_LOG_ENABLED - Enables logging in the module.
//==========================================================
#ifndef NRF_MPU_LIB_CONFIG_LOG_ENABLED
#define NRF_MPU_LIB_CONFIG_LOG_ENABLED 0
#endif
// <o> NRF_MPU_LIB_CONFIG_LOG_LEVEL  - Default Severity level
 
// <0=> Off 
// <1=> Error 
// <2=> Warning 
// <3=> Info 
// <4=> Debug 

#ifndef NRF_MPU_LIB_CONFIG_LOG_LEVEL
#define NRF_MPU_LIB_CONFIG_LOG_LEVEL 3
#endif

// <o> NRF_MPU_LIB_CONFIG_INFO_COLOR  - ANSI escape code prefix.
 
// <0=> Default 
// <1=> Black 
// <2=> Red 
// <3=> Green 
// <4=> Yellow 
// <5=> Blue 
// <6=> Magenta 
// <7=> Cyan 
// <8=> White 

#ifndef NRF_MPU_LIB_CONFIG_INFO_COLOR
#define NRF_MPU_LIB_CONFIG_INFO_COLOR 0
#endif

// <o> NRF_MPU_LIB_CONFIG_DEBUG_COLOR  - ANSI escape code prefix.
 
// <0=> Default 
// <1=> Black 
// <2=> Red 
// <3=> Green 
// <4=> Yellow 
// <5=> Blue 
// <6=> Magenta 
// <7=> Cyan 
// <8=> White 

#ifndef NRF_MPU_LIB_CONFIG_DEBUG_COLOR
#define NRF_MPU_LIB_CONFIG_DEBUG_COLOR 0
#endif

// </e>

// <e> NRF_STACK_GUARD_CONFIG_LOG_ENABLED - Enables logging in the module.
//==========================================================
#ifndef NRF_STACK_GUARD_CONFIG_LOG_ENABLED
#define NRF_STACK_GUARD_CONFIG_LOG_ENABLED 0
#endif
// <o> NRF_STACK_GUARD_CONFIG_LOG_LEVEL  - Default Severity level
 
// <0=> Off 
// <1=> Error 
// <2=> Warning 
// <3=> Info 
// <4=> Debug 

#ifndef NRF_STACK_GUARD_CONFIG_LOG_LEVEL
#define NRF_STACK_GUARD_CONFIG_LOG_LEVEL 3
#endif

// <o> NRF_STACK_GUARD_CONFIG_INFO_COLOR  - ANSI escape code prefix.
 
// <0=> Default 
// <1=> Black 
// <2=> Red 
// <3=> Green 
// <4=> Yellow 
// <5=> Blue 
// <6=> Magenta 
// <7=> Cyan 
// <8=> White 

#ifndef NRF_STACK_GUARD_CONFIG_INFO_COLOR
#define NRF_STACK_GUARD_CONFIG_INFO_COLOR 0
#endif

// <o> NRF_STACK_GUARD_CONFIG_DEBUG_COLOR  - ANSI escape code prefix.
 
// <0=> Default 
// <1=> Black 
// <2=> Red 
// <3=> Green 
// <4=> Yellow 
// <5=> Blue 
// <6=> Magenta 
// <7=> Cyan 
// <8=> White 

#ifndef NRF_STACK_GUARD_CONFIG_DEBUG_COLOR
#define NRF_STACK_GUARD_CONFIG_DEBUG_COLOR 0
#endif

// </e>

// <e> TASK_MANAGER_CONFIG_LOG_ENABLED - Enables logging in the module.
//==========================================================
#ifndef TASK_MANAGER_CONFIG_LOG_ENABLED
#define TASK_MANAGER_CONFIG_LOG_ENABLED 0
#endif
// <o> TASK_MANAGER_CONFIG_LOG_LEVEL  - Default Severity level
 
// <0=> Off 
// <1=> Error 
// <2=> Warning 
// <3=> Info 
// <4=> Debug 

#ifndef TASK_MANAGER_CONFIG_LOG_LEVEL
#define TASK_MANAGER_CONFIG_LOG_LEVEL 3
#endif

// <o> TASK_MANAGER_CONFIG_INFO_COLOR  - ANSI escape code prefix.
 
// <0=> Default 
// <1=> Black 
// <2=> Red 
// <3=> Green 
// <4=> Yellow 
// <5=> Blue 
// <6=> Magenta 
// <7=> Cyan 
// <8=> White 

#ifndef TASK_MANAGER_CONFIG_INFO_COLOR
#define TASK_MANAGER_CONFIG_INFO_COLOR 0
#endif

// <o> TASK_MANAGER_CONFIG_DEBUG_COLOR  - ANSI escape code prefix.
 
// <0=> Default 
// <1=> Black 
// <2=> Red 
// <3=> Green 
// <4=> Yellow 
// <5=> Blue 
// <6=> Magenta 
// <7=> Cyan 
// <8=> White 

#ifndef TASK_MANAGER_CONFIG_DEBUG_COLOR
#define TASK_MANAGER_CONFIG_DEBUG_COLOR 0
#endif

// </e>

// </h> 
//==========================================================

// <h> nrf_log in nRF_Drivers 

//==========================================================
// <e> CLOCK_CONFIG_LOG_ENABLED - Enables logging in the module.
//==========================================================
#ifndef CLOCK_CONFIG_LOG_ENABLED
#define CLOCK_CONFIG_LOG_ENABLED 0
#endif
// <o> CLOCK_CONFIG_LOG_LEVEL  - Default Severity level
 
// <0=> Off 
// <1=> Error 
// <2=> Warning 
// <3=> Info 
// <4=> Debug 

#ifndef CLOCK_CONFIG_LOG_LEVEL
#define CLOCK_CONFIG_LOG_LEVEL 3
#endif

// <o> CLOCK_CONFIG_INFO_COLOR  - ANSI escape code prefix.
 
// <0=> Default 
// <1=> Black 
// <2=> Red 
// <3=> Green 
// <4=> Yellow 
// <5=> Blue 
// <6=> Magenta 
// <7=> Cyan 
// <8=> White 

#ifndef CLOCK_CONFIG_INFO_COLOR
#define CLOCK_CONFIG_INFO_COLOR 0
#endif

// <o> CLOCK_CONFIG_DEBUG_COLOR  - ANSI escape code prefix.
 
// <0=> Default 
// <1=> Black 
// <2=> Red 
// <3=> Green 
// <4=> Yellow 
// <5=> Blue 
// <6=> Magenta 
// <7=> Cyan 
// <8=> White 

#ifndef CLOCK_CONFIG_DEBUG_COLOR
#define CLOCK_CONFIG_DEBUG_COLOR 0
#endif

// </e>

// <e> COMP_CONFIG_LOG_ENABLED - Enables logging in the module.
//==========================================================
#ifndef COMP_CONFIG_LOG_ENABLED
#define COMP_CONFIG_LOG_ENABLED 0
#endif
// <o> COMP_CONFIG_LOG_LEVEL  - Default Severity level
 
// <0=> Off 
// <1=> Error 
// <2=> Warning 
// <3=> Info 
// <4=> Debug 

#ifndef COMP_CONFIG_LOG_LEVEL
#define COMP_CONFIG_LOG_LEVEL 3
#endif

// <o> COMP_CONFIG_INFO_COLOR  - ANSI escape code prefix.
 
// <0=> Default 
// <1=> Black 
// <2=> Red 
// <3=> Green 
// <4=> Yellow 
// <5=> Blue 
// <6=> Magenta 
// <7=> Cyan 
// <8=> White 

#ifndef COMP_CONFIG_INFO_COLOR
#define COMP_CONFIG_INFO_COLOR 0
#endif

// <o> COMP_CONFIG_DEBUG_COLOR  - ANSI escape code prefix.
 
// <0=> Default 
// <1=> Black 
// <2=> Red 
// <3=> Green 
// <4=> Yellow 
// <5=> Blue 
// <6=> Magenta 
// <7=> Cyan 
// <8=> White 

#ifndef COMP_CONFIG_DEBUG_COLOR
#define COMP_CONFIG_DEBUG_COLOR 0
#endif

// </e>

// <e> GPIOTE_CONFIG_LOG_ENABLED - Enables logging in the module.
//==========================================================
#ifndef GPIOTE_CONFIG_LOG_ENABLED
#define GPIOTE_CONFIG_LOG_ENABLED 0
#endif
// <o> GPIOTE_CONFIG_LOG_LEVEL  - Default Severity level
 
// <0=> Off 
// <1=> Error 
// <2=> Warning 
// <3=> Info 
// <4=> Debug 

#ifndef GPIOTE_CONFIG_LOG_LEVEL
#define GPIOTE_CONFIG_LOG_LEVEL 3
#endif

// <o> GPIOTE_CONFIG_INFO_COLOR  - ANSI escape code prefix.
 
// <0=> Default 
// <1=> Black 
// <2=> Red 
// <3=> Green 
// <4=> Yellow 
// <5=> Blue 
// <6=> Magenta 
// <7=> Cyan 
// <8=> White 

#ifndef GPIOTE_CONFIG_INFO_COLOR
#define GPIOTE_CONFIG_INFO_COLOR 0
#endif

// <o> GPIOTE_CONFIG_DEBUG_COLOR  - ANSI escape code prefix.
 
// <0=> Default 
// <1=> Black 
// <2=> Red 
// <3=> Green 
// <4=> Yellow 
// <5=> Blue 
// <6=> Magenta 
// <7=> Cyan 
// <8=> White 

#ifndef GPIOTE_CONFIG_DEBUG_COLOR
#define GPIOTE_CONFIG_DEBUG_COLOR 0
#endif

// </e>

// <e> LPCOMP_CONFIG_LOG_ENABLED - Enables logging in the module.
//==========================================================
#ifndef LPCOMP_CONFIG_LOG_ENABLED
#define LPCOMP_CONFIG_LOG_ENABLED 0
#endif
// <o> LPCOMP_CONFIG_LOG_LEVEL  - Default Severity level
 
// <0=> Off 
// <1=> Error 
// <2=> Warning 
// <3=> Info 
// <4=> Debug 

#ifndef LPCOMP_CONFIG_LOG_LEVEL
#define LPCOMP_CONFIG_LOG_LEVEL 3
#endif

// <o> LPCOMP_CONFIG_INFO_COLOR  - ANSI escape code prefix.
 
// <0=> Default 
// <1=> Black 
// <2=> Red 
// <3=> Green 
// <4=> Yellow 
// <5=> Blue 
// <6=> Magenta 
// <7=> Cyan 
// <8=> White 

#ifndef LPCOMP_CONFIG_INFO_COLOR
#define LPCOMP_CONFIG_INFO_COLOR 0
#endif

// <o> LPCOMP_CONFIG_DEBUG_COLOR  - ANSI escape code prefix.
 
// <0=> Default 
// <1=> Black 
// <2=> Red 
// <3=> Green 
// <4=> Yellow 
// <5=> Blue 
// <6=> Magenta 
// <7=> Cyan 
// <8=> White 

#ifndef LPCOMP_CONFIG_DEBUG_COLOR
#define LPCOMP_CONFIG_DEBUG_COLOR 0
#endif

// </e>

// <e> MAX3421E_HOST_CONFIG_LOG_ENABLED - Enable logging in the module
//==========================================================
#ifndef MAX3421E_HOST_CONFIG_LOG_ENABLED
#define MAX3421E_HOST_CONFIG_LOG_ENABLED 0
#endif
// <o> MAX3421E_HOST_CONFIG_LOG_LEVEL  - Default Severity level
 
// <0=> Off 
// <1=> Error 
// <2=> Warning 
// <3=> Info 
// <4=> Debug 

#ifndef MAX3421E_HOST_CONFIG_LOG_LEVEL
#define MAX3421E_HOST_CONFIG_LOG_LEVEL 3
#endif

// <o> MAX3421E_HOST_CONFIG_INFO_COLOR  - ANSI escape code prefix.
 
// <0=> Default 
// <1=> Black 
// <2=> Red 
// <3=> Green 
// <4=> Yellow 
// <5=> Blue 
// <6=> Magenta 
// <7=> Cyan 
// <8=> White 

#ifndef MAX3421E_HOST_CONFIG_INFO_COLOR
#define MAX3421E_HOST_CONFIG_INFO_COLOR 0
#endif

// <o> MAX3421E_HOST_CONFIG_DEBUG_COLOR  - ANSI escape code prefix.
 
// <0=> Default 
// <1=> Black 
// <2=> Red 
// <3=> Green 
// <4=> Yellow 
// <5=> Blue 
// <6=> Magenta 
// <7=> Cyan 
// <8=> White 

#ifndef MAX3421E_HOST_CONFIG_DEBUG_COLOR
#define MAX3421E_HOST_CONFIG_DEBUG_COLOR 0
#endif

// </e>

// <e> NRFX_USBD_CONFIG_LOG_ENABLED - Enable logging in the module
//==========================================================
#ifndef NRFX_USBD_CONFIG_LOG_ENABLED
#define NRFX_USBD_CONFIG_LOG_ENABLED 0
#endif
// <o> NRFX_USBD_CONFIG_LOG_LEVEL  - Default Severity level
 
// <0=> Off 
// <1=> Error 
// <2=> Warning 
// <3=> Info 
// <4=> Debug 

#ifndef NRFX_USBD_CONFIG_LOG_LEVEL
#define NRFX_USBD_CONFIG_LOG_LEVEL 3
#endif

// <o> NRFX_USBD_CONFIG_INFO_COLOR  - ANSI escape code prefix.
 
// <0=> Default 
// <1=> Black 
// <2=> Red 
// <3=> Green 
// <4=> Yellow 
// <5=> Blue 
// <6=> Magenta 
// <7=> Cyan 
// <8=> White 

#ifndef NRFX_USBD_CONFIG_INFO_COLOR
#define NRFX_USBD_CONFIG_INFO_COLOR 0
#endif

// <o> NRFX_USBD_CONFIG_DEBUG_COLOR  - ANSI escape code prefix.
 
// <0=> Default 
// <1=> Black 
// <2=> Red 
// <3=> Green 
// <4=> Yellow 
// <5=> Blue 
// <6=> Magenta 
// <7=> Cyan 
// <8=> White 

#ifndef NRFX_USBD_CONFIG_DEBUG_COLOR
#define NRFX_USBD_CONFIG_DEBUG_COLOR 0
#endif

// </e>

// <e> PDM_CONFIG_LOG_ENABLED - Enables logging in the module.
//==========================================================
#ifndef PDM_CONFIG_LOG_ENABLED
#define PDM_CONFIG_LOG_ENABLED 0
#endif
// <o> PDM_CONFIG_LOG_LEVEL  - Default Severity level
 
// <0=> Off 
// <1=> Error 
// <2=> Warning 
// <3=> Info 
// <4=> Debug 

#ifndef PDM_CONFIG_LOG_LEVEL
#define PDM_CONFIG_LOG_LEVEL 3
#endif

// <o> PDM_CONFIG_INFO_COLOR  - ANSI escape code prefix.
 
// <0=> Default 
// <1=> Black 
// <2=> Red 
// <3=> Green 
// <4=> Yellow 
// <5=> Blue 
// <6=> Magenta 
// <7=> Cyan 
// <8=> White 

#ifndef PDM_CONFIG_INFO_COLOR
#define PDM_CONFIG_INFO_COLOR 0
#endif

// <o> PDM_CONFIG_DEBUG_COLOR  - ANSI escape code prefix.
 
// <0=> Default 
// <1=> Black 
// <2=> Red 
// <3=> Green 
// <4=> Yellow 
// <5=> Blue 
// <6=> Magenta 
// <7=> Cyan 
// <8=> White 

#ifndef PDM_CONFIG_DEBUG_COLOR
#define PDM_CONFIG_DEBUG_COLOR 0
#endif

// </e>

// <e> PPI_CONFIG_LOG_ENABLED - Enables logging in the module.
//==========================================================
#ifndef PPI_CONFIG_LOG_ENABLED
#define PPI_CONFIG_LOG_ENABLED 0
#endif
// <o> PPI_CONFIG_LOG_LEVEL  - Default Severity level
 
// <0=> Off 
// <1=> Error 
// <2=> Warning 
// <3=> Info 
// <4=> Debug 

#ifndef PPI_CONFIG_LOG_LEVEL
#define PPI_CONFIG_LOG_LEVEL 3
#endif

// <o> PPI_CONFIG_INFO_COLOR  - ANSI escape code prefix.
 
// <0=> Default 
// <1=> Black 
// <2=> Red 
// <3=> Green 
// <4=> Yellow 
// <5=> Blue 
// <6=> Magenta 
// <7=> Cyan 
// <8=> White 

#ifndef PPI_CONFIG_INFO_COLOR
#define PPI_CONFIG_INFO_COLOR 0
#endif

// <o> PPI_CONFIG_DEBUG_COLOR  - ANSI escape code prefix.
 
// <0=> Default 
// <1=> Black 
// <2=> Red 
// <3=> Green 
// <4=> Yellow 
// <5=> Blue 
// <6=> Magenta 
// <7=> Cyan 
// <8=> White 

#ifndef PPI_CONFIG_DEBUG_COLOR
#define PPI_CONFIG_DEBUG_COLOR 0
#endif

// </e>

// <e> PWM_CONFIG_LOG_ENABLED - Enables logging in the module.
//==========================================================
#ifndef PWM_CONFIG_LOG_ENABLED
#define PWM_CONFIG_LOG_ENABLED 0
#endif
// <o> PWM_CONFIG_LOG_LEVEL  - Default Severity level
 
// <0=> Off 
// <1=> Error 
// <2=> Warning 
// <3=> Info 
// <4=> Debug 

#ifndef PWM_CONFIG_LOG_LEVEL
#define PWM_CONFIG_LOG_LEVEL 3
#endif

// <o> PWM_CONFIG_INFO_COLOR  - ANSI escape code prefix.
 
// <0=> Default 
// <1=> Black 
// <2=> Red 
// <3=> Green 
// <4=> Yellow 
// <5=> Blue 
// <6=> Magenta 
// <7=> Cyan 
// <8=> White 

#ifndef PWM_CONFIG_INFO_COLOR
#define PWM_CONFIG_INFO_COLOR 0
#endif

// <o> PWM_CONFIG_DEBUG_COLOR  - ANSI escape code prefix.
 
// <0=> Default 
// <1=> Black 
// <2=> Red 
// <3=> Green 
// <4=> Yellow 
// <5=> Blue 
// <6=> Magenta 
// <7=> Cyan 
// <8=> White 

#ifndef PWM_CONFIG_DEBUG_COLOR
#define PWM_CONFIG_DEBUG_COLOR 0
#endif

// </e>

// <e> QDEC_CONFIG_LOG_ENABLED - Enables logging in the module.
//==========================================================
#ifndef QDEC_CONFIG_LOG_ENABLED
#define QDEC_CONFIG_LOG_ENABLED 0
#endif
// <o> QDEC_CONFIG_LOG_LEVEL  - Default Severity level
 
// <0=> Off 
// <1=> Error 
// <2=> Warning 
// <3=> Info 
// <4=> Debug 

#ifndef QDEC_CONFIG_LOG_LEVEL
#define QDEC_CONFIG_LOG_LEVEL 3
#endif

// <o> QDEC_CONFIG_INFO_COLOR  - ANSI escape code prefix.
 
// <0=> Default 
// <1=> Black 
// <2=> Red 
// <3=> Green 
// <4=> Yellow 
// <5=> Blue 
// <6=> Magenta 
// <7=> Cyan 
// <8=> White 

#ifndef QDEC_CONFIG_INFO_COLOR
#define QDEC_CONFIG_INFO_COLOR 0
#endif

// <o> QDEC_CONFIG_DEBUG_COLOR  - ANSI escape code prefix.
 
// <0=> Default 
// <1=> Black 
// <2=> Red 
// <3=> Green 
// <4=> Yellow 
// <5=> Blue 
// <6=> Magenta 
// <7=> Cyan 
// <8=> White 

#ifndef QDEC_CONFIG_DEBUG_COLOR
#define QDEC_CONFIG_DEBUG_COLOR 0
#endif

// </e>

// <e> RNG_CONFIG_LOG_ENABLED - Enables logging in the module.
//==========================================================
#ifndef RNG_CONFIG_LOG_ENABLED
#define RNG_CONFIG_LOG_ENABLED 0
#endif
// <o> RNG_CONFIG_LOG_LEVEL  - Default Severity level
 
// <0=> Off 
// <1=> Error 
// <2=> Warning 
// <3=> Info 
// <4=> Debug 

#ifndef RNG_CONFIG_LOG_LEVEL
#define RNG_CONFIG_LOG_LEVEL 3
#endif

// <o> RNG_CONFIG_INFO_COLOR  - ANSI escape code prefix.
 
// <0=> Default 
// <1=> Black 
// <2=> Red 
// <3=> Green 
// <4=> Yellow 
// <5=> Blue 
// <6=> Magenta 
// <7=> Cyan 
// <8=> White 

#ifndef RNG_CONFIG_INFO_COLOR
#define RNG_CONFIG_INFO_COLOR 0
#endif

// <o> RNG_CONFIG_DEBUG_COLOR  - ANSI escape code prefix.
 
// <0=> Default 
// <1=> Black 
// <2=> Red 
// <3=> Green 
// <4=> Yellow 
// <5=> Blue 
// <6=> Magenta 
// <7=> Cyan 
// <8=> White 

#ifndef RNG_CONFIG_DEBUG_COLOR
#define RNG_CONFIG_DEBUG_COLOR 0
#endif

// <q> RNG_CONFIG_RANDOM_NUMBER_LOG_ENABLED  - Enables logging of random numbers.
 

#ifndef RNG_CONFIG_RANDOM_NUMBER_LOG_ENABLED
#define RNG_CONFIG_RANDOM_NUMBER_LOG_ENABLED 0
#endif

// </e>

// <e> RTC_CONFIG_LOG_ENABLED - Enables logging in the module.
//==========================================================
#ifndef RTC_CONFIG_LOG_ENABLED
#define RTC_CONFIG_LOG_ENABLED 0
#endif
// <o> RTC_CONFIG_LOG_LEVEL  - Default Severity level
 
// <0=> Off 
// <1=> Error 
// <2=> Warning 
// <3=> Info 
// <4=> Debug 

#ifndef RTC_CONFIG_LOG_LEVEL
#define RTC_CONFIG_LOG_LEVEL 3
#endif

// <o> RTC_CONFIG_INFO_COLOR  - ANSI escape code prefix.
 
// <0=> Default 
// <1=> Black 
// <2=> Red 
// <3=> Green 
// <4=> Yellow 
// <5=> Blue 
// <6=> Magenta 
// <7=> Cyan 
// <8=> White 

#ifndef RTC_CONFIG_INFO_COLOR
#define RTC_CONFIG_INFO_COLOR 0
#endif

// <o> RTC_CONFIG_DEBUG_COLOR  - ANSI escape code prefix.
 
// <0=> Default 
// <1=> Black 
// <2=> Red 
// <3=> Green 
// <4=> Yellow 
// <5=> Blue 
// <6=> Magenta 
// <7=> Cyan 
// <8=> White 

#ifndef RTC_CONFIG_DEBUG_COLOR
#define RTC_CONFIG_DEBUG_COLOR 0
#endif

// </e>

// <e> SAADC_CONFIG_LOG_ENABLED - Enables logging in the module.
//==========================================================
#ifndef SAADC_CONFIG_LOG_ENABLED
#define SAADC_CONFIG_LOG_ENABLED 0
#endif
// <o> SAADC_CONFIG_LOG_LEVEL  - Default Severity level
 
// <0=> Off 
// <1=> Error 
// <2=> Warning 
// <3=> Info 
// <4=> Debug 

#ifndef SAADC_CONFIG_LOG_LEVEL
#define SAADC_CONFIG_LOG_LEVEL 3
#endif

// <o> SAADC_CONFIG_INFO_COLOR  - ANSI escape code prefix.
 
// <0=> Default 
// <1=> Black 
// <2=> Red 
// <3=> Green 
// <4=> Yellow 
// <5=> Blue 
// <6=> Magenta 
// <7=> Cyan 
// <8=> White 

#ifndef SAADC_CONFIG_INFO_COLOR
#define SAADC_CONFIG_INFO_COLOR 0
#endif

// <o> SAADC_CONFIG_DEBUG_COLOR  - ANSI escape code prefix.
 
// <0=> Default 
// <1=> Black 
// <2=> Red 
// <3=> Green 
// <4=> Yellow 
// <5=> Blue 
// <6=> Magenta 
// <7=> Cyan 
// <8=> White 

#ifndef SAADC_CONFIG_DEBUG_COLOR
#define SAADC_CONFIG_DEBUG_COLOR 0
#endif

// </e>

// <e> SPIS_CONFIG_LOG_ENABLED - Enables logging in the module.
//==========================================================
#ifndef SPIS_CONFIG_LOG_ENABLED
#define SPIS_CONFIG_LOG_ENABLED 0
#endif
// <o> SPIS_CONFIG_LOG_LEVEL  - Default Severity level
 
// <0=> Off 
// <1=> Error 
// <2=> Warning 
// <3=> Info 
// <4=> Debug 

#ifndef SPIS_CONFIG_LOG_LEVEL
#define SPIS_CONFIG_LOG_LEVEL 3
#endif

// <o> SPIS_CONFIG_INFO_COLOR  - ANSI escape code prefix.
 
// <0=> Default 
// <1=> Black 
// <2=> Red 
// <3=> Green 
// <4=> Yellow 
// <5=> Blue 
// <6=> Magenta 
// <7=> Cyan 
// <8=> White 

#ifndef SPIS_CONFIG_INFO_COLOR
#define SPIS_CONFIG_INFO_COLOR 0
#endif

// <o> SPIS_CONFIG_DEBUG_COLOR  - ANSI escape code prefix.
 
// <0=> Default 
// <1=> Black 
// <2=> Red 
// <3=> Green 
// <4=> Yellow 
// <5=> Blue 
// <6=> Magenta 
// <7=> Cyan 
// <8=> White 

#ifndef SPIS_CONFIG_DEBUG_COLOR
#define SPIS_CONFIG_DEBUG_COLOR 0
#endif

// </e>

// <e> SPI_CONFIG_LOG_ENABLED - Enables logging in the module.
//==========================================================
#ifndef SPI_CONFIG_LOG_ENABLED
#define SPI_CONFIG_LOG_ENABLED 0
#endif
// <o> SPI_CONFIG_LOG_LEVEL  - Default Severity level
 
// <0=> Off 
// <1=> Error 
// <2=> Warning 
// <3=> Info 
// <4=> Debug 

#ifndef SPI_CONFIG_LOG_LEVEL
#define SPI_CONFIG_LOG_LEVEL 3
#endif

// <o> SPI_CONFIG_INFO_COLOR  - ANSI escape code prefix.
 
// <0=> Default 
// <1=> Black 
// <2=> Red 
// <3=> Green 
// <4=> Yellow 
// <5=> Blue 
// <6=> Magenta 
// <7=> Cyan 
// <8=> White 

#ifndef SPI_CONFIG_INFO_COLOR
#define SPI_CONFIG_INFO_COLOR 0
#endif

// <o> SPI_CONFIG_DEBUG_COLOR  - ANSI escape code prefix.
 
// <0=> Default 
// <1=> Black 
// <2=> Red 
// <3=> Green 
// <4=> Yellow 
// <5=> Blue 
// <6=> Magenta 
// <7=> Cyan 
// <8=> White 

#ifndef SPI_CONFIG_DEBUG_COLOR
#define SPI_CONFIG_DEBUG_COLOR 0
#endif

// </e>

// <e> TIMER_CONFIG_LOG_ENABLED - Enables logging in the module.
//==========================================================
#ifndef TIMER_CONFIG_LOG_ENABLED
#define TIMER_CONFIG_LOG_ENABLED 0
#endif
// <o> TIMER_CONFIG_LOG_LEVEL  - Default Severity level
 
// <0=> Off 
// <1=> Error 
// <2=> Warning 
// <3=> Info 
// <4=> Debug 

#ifndef TIMER_CONFIG_LOG_LEVEL
#define TIMER_CONFIG_LOG_LEVEL 3
#endif

// <o> TIMER_CONFIG_INFO_COLOR  - ANSI escape code prefix.
 
// <0=> Default 
// <1=> Black 
// <2=> Red 
// <3=> Green 
// <4=> Yellow 
// <5=> Blue 
// <6=> Magenta 
// <7=> Cyan 
// <8=> White 

#ifndef TIMER_CONFIG_INFO_COLOR
#define TIMER_CONFIG_INFO_COLOR 0
#endif

// <o> TIMER_CONFIG_DEBUG_COLOR  - ANSI escape code prefix.
 
// <0=> Default 
// <1=> Black 
// <2=> Red 
// <3=> Green 
// <4=> Yellow 
// <5=> Blue 
// <6=> Magenta 
// <7=> Cyan 
// <8=> White 

#ifndef TIMER_CONFIG_DEBUG_COLOR
#define TIMER_CONFIG_DEBUG_COLOR 0
#endif

// </e>

// <e> TWIS_CONFIG_LOG_ENABLED - Enables logging in the module.
//==========================================================
#ifndef TWIS_CONFIG_LOG_ENABLED
#define TWIS_CONFIG_LOG_ENABLED 0
#endif
// <o> TWIS_CONFIG_LOG_LEVEL  - Default Severity level
 
// <0=> Off 
// <1=> Error 
// <2=> Warning 
// <3=> Info 
// <4=> Debug 

#ifndef TWIS_CONFIG_LOG_LEVEL
#define TWIS_CONFIG_LOG_LEVEL 3
#endif

// <o> TWIS_CONFIG_INFO_COLOR  - ANSI escape code prefix.
 
// <0=> Default 
// <1=> Black 
// <2=> Red 
// <3=> Green 
// <4=> Yellow 
// <5=> Blue 
// <6=> Magenta 
// <7=> Cyan 
// <8=> White 

#ifndef TWIS_CONFIG_INFO_COLOR
#define TWIS_CONFIG_INFO_COLOR 0
#endif

// <o> TWIS_CONFIG_DEBUG_COLOR  - ANSI escape code prefix.
 
// <0=> Default 
// <1=> Black 
// <2=> Red 
// <3=> Green 
// <4=> Yellow 
// <5=> Blue 
// <6=> Magenta 
// <7=> Cyan 
// <8=> White 

#ifndef TWIS_CONFIG_DEBUG_COLOR
#define TWIS_CONFIG_DEBUG_COLOR 0
#endif

// </e>

// <e> TWI_CONFIG_LOG_ENABLED - Enables logging in the module.
//==========================================================
#ifndef TWI_CONFIG_LOG_ENABLED
#define TWI_CONFIG_LOG_ENABLED 0
#endif
// <o> TWI_CONFIG_LOG_LEVEL  - Default Severity level
 
// <0=> Off 
// <1=> Error 
// <2=> Warning 
// <3=> Info 
// <4=> Debug 

#ifndef TWI_CONFIG_LOG_LEVEL
#define TWI_CONFIG_LOG_LEVEL 3
#endif

// <o> TWI_CONFIG_INFO_COLOR  - ANSI escape code prefix.
 
// <0=> Default 
// <1=> Black 
// <2=> Red 
// <3=> Green 
// <4=> Yellow 
// <5=> Blue 
// <6=> Magenta 
// <7=> Cyan 
// <8=> White 

#ifndef TWI_CONFIG_INFO_COLOR
#define TWI_CONFIG_INFO_COLOR 0
#endif

// <o> TWI_CONFIG_DEBUG_COLOR  - ANSI escape code prefix.
 
// <0=> Default 
// <1=> Black 
// <2=> Red 
// <3=> Green 
// <4=> Yellow 
// <5=> Blue 
// <6=> Magenta 
// <7=> Cyan 
// <8=> White 

#ifndef TWI_CONFIG_DEBUG_COLOR
#define TWI_CONFIG_DEBUG_COLOR 0
#endif

// </e>

// <e> UART_CONFIG_LOG_ENABLED - Enables logging in the module.
//==========================================================
#ifndef UART_CONFIG_LOG_ENABLED
#define UART_CONFIG_LOG_ENABLED 0
#endif
// <o> UART_CONFIG_LOG_LEVEL  - Default Severity level
 
// <0=> Off 
// <1=> Error 
// <2=> Warning 
// <3=> Info 
// <4=> Debug 

#ifndef UART_CONFIG_LOG_LEVEL
#define UART_CONFIG_LOG_LEVEL 3
#endif

// <o> UART_CONFIG_INFO_COLOR  - ANSI escape code prefix.
 
// <0=> Default 
// <1=> Black 
// <2=> Red 
// <3=> Green 
// <4=> Yellow 
// <5=> Blue 
// <6=> Magenta 
// <7=> Cyan 
// <8=> White 

#ifndef UART_CONFIG_INFO_COLOR
#define UART_CONFIG_INFO_COLOR 0
#endif

// <o> UART_CONFIG_DEBUG_COLOR  - ANSI escape code prefix.
 
// <0=> Default 
// <1=> Black 
// <2=> Red 
// <3=> Green 
// <4=> Yellow 
// <5=> Blue 
// <6=> Magenta 
// <7=> Cyan 
// <8=> White 

#ifndef UART_CONFIG_DEBUG_COLOR
#define UART_CONFIG_DEBUG_COLOR 0
#endif

// </e>

// <e> USBD_CONFIG_LOG_ENABLED - Enable logging in the module
//==========================================================
#ifndef USBD_CONFIG_LOG_ENABLED
#define USBD_CONFIG_LOG_ENABLED 0
#endif
// <o> USBD_CONFIG_LOG_LEVEL  - Default Severity level
 
// <0=> Off 
// <1=> Error 
// <2=> Warning 
// <3=> Info 
// <4=> Debug 

#ifndef USBD_CONFIG_LOG_LEVEL
#define USBD_CONFIG_LOG_LEVEL 3
#endif

// <o> USBD_CONFIG_INFO_COLOR  - ANSI escape code prefix.
 
// <0=> Default 
// <1=> Black 
// <2=> Red 
// <3=> Green 
// <4=> Yellow 
// <5=> Blue 
// <6=> Magenta 
// <7=> Cyan 
// <8=> White 

#ifndef USBD_CONFIG_INFO_COLOR
#define USBD_CONFIG_INFO_COLOR 0
#endif

// <o> USBD_CONFIG_DEBUG_COLOR  - ANSI escape code prefix.
 
// <0=> Default 
// <1=> Black 
// <2=> Red 
// <3=> Green 
// <4=> Yellow 
// <5=> Blue 
// <6=> Magenta 
// <7=> Cyan 
// <8=> White 

#ifndef USBD_CONFIG_DEBUG_COLOR
#define USBD_CONFIG_DEBUG_COLOR 0
#endif

// </e>

// <e> WDT_CONFIG_LOG_ENABLED - Enables logging in the module.
//==========================================================
#ifndef WDT_CONFIG_LOG_ENABLED
#define WDT_CONFIG_LOG_ENABLED 0
#endif
// <o> WDT_CONFIG_LOG_LEVEL  - Default Severity level
 
// <0=> Off 
// <1=> Error 
// <2=> Warning 
// <3=> Info 
// <4=> Debug 

#ifndef WDT_CONFIG_LOG_LEVEL
#define WDT_CONFIG_LOG_LEVEL 3
#endif

// <o> WDT_CONFIG_INFO_COLOR  - ANSI escape code prefix.
 
// <0=> Default 
// <1=> Black 
// <2=> Red 
// <3=> Green 
// <4=> Yellow 
// <5=> Blue 
// <6=> Magenta 
// <7=> Cyan 
// <8=> White 

#ifndef WDT_CONFIG_INFO_COLOR
#define WDT_CONFIG_INFO_COLOR 0
#endif

// <o> WDT_CONFIG_DEBUG_COLOR  - ANSI escape code prefix.
 
// <0=> Default 
// <1=> Black 
// <2=> Red 
// <3=> Green 
// <4=> Yellow 
// <5=> Blue 
// <6=> Magenta 
// <7=> Cyan 
// <8=> White 

#ifndef WDT_CONFIG_DEBUG_COLOR
#define WDT_CONFIG_DEBUG_COLOR 0
#endif

// </e>

// </h> 
//==========================================================

// <h> nrf_log in nRF_Libraries 

//==========================================================
// <e> APP_BUTTON_CONFIG_LOG_ENABLED - Enables logging in the module.
//==========================================================
#ifndef APP_BUTTON_CONFIG_LOG_ENABLED
#define APP_BUTTON_CONFIG_LOG_ENABLED 0
#endif
// <o> APP_BUTTON_CONFIG_LOG_LEVEL  - Default Severity level
 
// <0=> Off 
// <1=> Error 
// <2=> Warning 
// <3=> Info 
// <4=> Debug 

#ifndef APP_BUTTON_CONFIG_LOG_LEVEL
#define APP_BUTTON_CONFIG_LOG_LEVEL 3
#endif

// <o> APP_BUTTON_CONFIG_INITIAL_LOG_LEVEL  - Initial severity level if dynamic filtering is enabled.
 

// <i> If module generates a lot of logs, initial log level can
// <i> be decreased to prevent flooding. Severity level can be
// <i> increased on instance basis.
// <0=> Off 
// <1=> Error 
// <2=> Warning 
// <3=> Info 
// <4=> Debug 

#ifndef APP_BUTTON_CONFIG_INITIAL_LOG_LEVEL
#define APP_BUTTON_CONFIG_INITIAL_LOG_LEVEL 3
#endif

// <o> APP_BUTTON_CONFIG_INFO_COLOR  - ANSI escape code prefix.
 
// <0=> Default 
// <1=> Black 
// <2=> Red 
// <3=> Green 
// <4=> Yellow 
// <5=> Blue 
// <6=> Magenta 
// <7=> Cyan 
// <8=> White 

#ifndef APP_BUTTON_CONFIG_INFO_COLOR
#define APP_BUTTON_CONFIG_INFO_COLOR 0
#endif

// <o> APP_BUTTON_CONFIG_DEBUG_COLOR  - ANSI escape code prefix.
 
// <0=> Default 
// <1=> Black 
// <2=> Red 
// <3=> Green 
// <4=> Yellow 
// <5=> Blue 
// <6=> Magenta 
// <7=> Cyan 
// <8=> White 

#ifndef APP_BUTTON_CONFIG_DEBUG_COLOR
#define APP_BUTTON_CONFIG_DEBUG_COLOR 0
#endif

// </e>

// <e> APP_TIMER_CONFIG_LOG_ENABLED - Enables logging in the module.
//==========================================================
#ifndef APP_TIMER_CONFIG_LOG_ENABLED
#define APP_TIMER_CONFIG_LOG_ENABLED 0
#endif
// <o> APP_TIMER_CONFIG_LOG_LEVEL  - Default Severity level
 
// <0=> Off 
// <1=> Error 
// <2=> Warning 
// <3=> Info 
// <4=> Debug 

#ifndef APP_TIMER_CONFIG_LOG_LEVEL
#define APP_TIMER_CONFIG_LOG_LEVEL 3
#endif

// <o> APP_TIMER_CONFIG_INITIAL_LOG_LEVEL  - Initial severity level if dynamic filtering is enabled.
 

// <i> If module generates a lot of logs, initial log level can
// <i> be decreased to prevent flooding. Severity level can be
// <i> increased on instance basis.
// <0=> Off 
// <1=> Error 
// <2=> Warning 
// <3=> Info 
// <4=> Debug 

#ifndef APP_TIMER_CONFIG_INITIAL_LOG_LEVEL
#define APP_TIMER_CONFIG_INITIAL_LOG_LEVEL 3
#endif

// <o> APP_TIMER_CONFIG_INFO_COLOR  - ANSI escape code prefix.
 
// <0=> Default 
// <1=> Black 
// <2=> Red 
// <3=> Green 
// <4=> Yellow 
// <5=> Blue 
// <6=> Magenta 
// <7=> Cyan 
// <8=> White 

#ifndef APP_TIMER_CONFIG_INFO_COLOR
#define APP_TIMER_CONFIG_INFO_COLOR 0
#endif

// <o> APP_TIMER_CONFIG_DEBUG_COLOR  - ANSI escape code prefix.
 
// <0=> Default 
// <1=> Black 
// <2=> Red 
// <3=> Green 
// <4=> Yellow 
// <5=> Blue 
// <6=> Magenta 
// <7=> Cyan 
// <8=> White 

#ifndef APP_TIMER_CONFIG_DEBUG_COLOR
#define APP_TIMER_CONFIG_DEBUG_COLOR 0
#endif

// </e>

// <e> APP_USBD_CDC_ACM_CONFIG_LOG_ENABLED - Enables logging in the module.
//==========================================================
#ifndef APP_USBD_CDC_ACM_CONFIG_LOG_ENABLED
#define APP_USBD_CDC_ACM_CONFIG_LOG_ENABLED 0
#endif
// <o> APP_USBD_CDC_ACM_CONFIG_LOG_LEVEL  - Default Severity level
 
// <0=> Off 
// <1=> Error 
// <2=> Warning 
// <3=> Info 
// <4=> Debug 

#ifndef APP_USBD_CDC_ACM_CONFIG_LOG_LEVEL
#define APP_USBD_CDC_ACM_CONFIG_LOG_LEVEL 3
#endif

// <o> APP_USBD_CDC_ACM_CONFIG_INFO_COLOR  - ANSI escape code prefix.
 
// <0=> Default 
// <1=> Black 
// <2=> Red 
// <3=> Green 
// <4=> Yellow 
// <5=> Blue 
// <6=> Magenta 
// <7=> Cyan 
// <8=> White 

#ifndef APP_USBD_CDC_ACM_CONFIG_INFO_COLOR
#define APP_USBD_CDC_ACM_CONFIG_INFO_COLOR 0
#endif

// <o> APP_USBD_CDC_ACM_CONFIG_DEBUG_COLOR  - ANSI escape code prefix.
 
// <0=> Default 
// <1=> Black 
// <2=> Red 
// <3=> Green 
// <4=> Yellow 
// <5=> Blue 
// <6=> Magenta 
// <7=> Cyan 
// <8=> White 

#ifndef APP_USBD_CDC_ACM_CONFIG_DEBUG_COLOR
#define APP_USBD_CDC_ACM_CONFIG_DEBUG_COLOR 0
#endif

// </e>

// <e> APP_USBD_CONFIG_LOG_ENABLED - Enable logging in the module.
//==========================================================
#ifndef APP_USBD_CONFIG_LOG_ENABLED
#define APP_USBD_CONFIG_LOG_ENABLED 0
#endif
// <o> APP_USBD_CONFIG_LOG_LEVEL  - Default Severity level
 
// <0=> Off 
// <1=> Error 
// <2=> Warning 
// <3=> Info 
// <4=> Debug 

#ifndef APP_USBD_CONFIG_LOG_LEVEL
#define APP_USBD_CONFIG_LOG_LEVEL 3
#endif

// <o> APP_USBD_CONFIG_INFO_COLOR  - ANSI escape code prefix.
 
// <0=> Default 
// <1=> Black 
// <2=> Red 
// <3=> Green 
// <4=> Yellow 
// <5=> Blue 
// <6=> Magenta 
// <7=> Cyan 
// <8=> White 

#ifndef APP_USBD_CONFIG_INFO_COLOR
#define APP_USBD_CONFIG_INFO_COLOR 0
#endif

// <o> APP_USBD_CONFIG_DEBUG_COLOR  - ANSI escape code prefix.
 
// <0=> Default 
// <1=> Black 
// <2=> Red 
// <3=> Green 
// <4=> Yellow 
// <5=> Blue 
// <6=> Magenta 
// <7=> Cyan 
// <8=> White 

#ifndef APP_USBD_CONFIG_DEBUG_COLOR
#define APP_USBD_CONFIG_DEBUG_COLOR 0
#endif

// </e>

// <e> APP_USBD_DUMMY_CONFIG_LOG_ENABLED - Enables logging in the module.
//==========================================================
#ifndef APP_USBD_DUMMY_CONFIG_LOG_ENABLED
#define APP_USBD_DUMMY_CONFIG_LOG_ENABLED 0
#endif
// <o> APP_USBD_DUMMY_CONFIG_LOG_LEVEL  - Default Severity level
 
// <0=> Off 
// <1=> Error 
// <2=> Warning 
// <3=> Info 
// <4=> Debug 

#ifndef APP_USBD_DUMMY_CONFIG_LOG_LEVEL
#define APP_USBD_DUMMY_CONFIG_LOG_LEVEL 3
#endif

// <o> APP_USBD_DUMMY_CONFIG_INFO_COLOR  - ANSI escape code prefix.
 
// <0=> Default 
// <1=> Black 
// <2=> Red 
// <3=> Green 
// <4=> Yellow 
// <5=> Blue 
// <6=> Magenta 
// <7=> Cyan 
// <8=> White 

#ifndef APP_USBD_DUMMY_CONFIG_INFO_COLOR
#define APP_USBD_DUMMY_CONFIG_INFO_COLOR 0
#endif

// <o> APP_USBD_DUMMY_CONFIG_DEBUG_COLOR  - ANSI escape code prefix.
 
// <0=> Default 
// <1=> Black 
// <2=> Red 
// <3=> Green 
// <4=> Yellow 
// <5=> Blue 
// <6=> Magenta 
// <7=> Cyan 
// <8=> White 

#ifndef APP_USBD_DUMMY_CONFIG_DEBUG_COLOR
#define APP_USBD_DUMMY_CONFIG_DEBUG_COLOR 0
#endif

// </e>

// <e> APP_USBD_MSC_CONFIG_LOG_ENABLED - Enables logging in the module.
//==========================================================
#ifndef APP_USBD_MSC_CONFIG_LOG_ENABLED
#define APP_USBD_MSC_CONFIG_LOG_ENABLED 0
#endif
// <o> APP_USBD_MSC_CONFIG_LOG_LEVEL  - Default Severity level
 
// <0=> Off 
// <1=> Error 
// <2=> Warning 
// <3=> Info 
// <4=> Debug 

#ifndef APP_USBD_MSC_CONFIG_LOG_LEVEL
#define APP_USBD_MSC_CONFIG_LOG_LEVEL 3
#endif

// <o> APP_USBD_MSC_CONFIG_INFO_COLOR  - ANSI escape code prefix.
 
// <0=> Default 
// <1=> Black 
// <2=> Red 
// <3=> Green 
// <4=> Yellow 
// <5=> Blue 
// <6=> Magenta 
// <7=> Cyan 
// <8=> White 

#ifndef APP_USBD_MSC_CONFIG_INFO_COLOR
#define APP_USBD_MSC_CONFIG_INFO_COLOR 0
#endif

// <o> APP_USBD_MSC_CONFIG_DEBUG_COLOR  - ANSI escape code prefix.
 
// <0=> Default 
// <1=> Black 
// <2=> Red 
// <3=> Green 
// <4=> Yellow 
// <5=> Blue 
// <6=> Magenta 
// <7=> Cyan 
// <8=> White 

#ifndef APP_USBD_MSC_CONFIG_DEBUG_COLOR
#define APP_USBD_MSC_CONFIG_DEBUG_COLOR 0
#endif

// </e>

// <e> APP_USBD_NRF_DFU_TRIGGER_CONFIG_LOG_ENABLED - Enables logging in the module.
//==========================================================
#ifndef APP_USBD_NRF_DFU_TRIGGER_CONFIG_LOG_ENABLED
#define APP_USBD_NRF_DFU_TRIGGER_CONFIG_LOG_ENABLED 0
#endif
// <o> APP_USBD_NRF_DFU_TRIGGER_CONFIG_LOG_LEVEL  - Default Severity level
 
// <0=> Off 
// <1=> Error 
// <2=> Warning 
// <3=> Info 
// <4=> Debug 

#ifndef APP_USBD_NRF_DFU_TRIGGER_CONFIG_LOG_LEVEL
#define APP_USBD_NRF_DFU_TRIGGER_CONFIG_LOG_LEVEL 3
#endif

// <o> APP_USBD_NRF_DFU_TRIGGER_CONFIG_INFO_COLOR  - ANSI escape code prefix.
 
// <0=> Default 
// <1=> Black 
// <2=> Red 
// <3=> Green 
// <4=> Yellow 
// <5=> Blue 
// <6=> Magenta 
// <7=> Cyan 
// <8=> White 

#ifndef APP_USBD_NRF_DFU_TRIGGER_CONFIG_INFO_COLOR
#define APP_USBD_NRF_DFU_TRIGGER_CONFIG_INFO_COLOR 0
#endif

// <o> APP_USBD_NRF_DFU_TRIGGER_CONFIG_DEBUG_COLOR  - ANSI escape code prefix.
 
// <0=> Default 
// <1=> Black 
// <2=> Red 
// <3=> Green 
// <4=> Yellow 
// <5=> Blue 
// <6=> Magenta 
// <7=> Cyan 
// <8=> White 

#ifndef APP_USBD_NRF_DFU_TRIGGER_CONFIG_DEBUG_COLOR
#define APP_USBD_NRF_DFU_TRIGGER_CONFIG_DEBUG_COLOR 0
#endif

// </e>

// <e> NRF_ATFIFO_CONFIG_LOG_ENABLED - Enables logging in the module.
//==========================================================
#ifndef NRF_ATFIFO_CONFIG_LOG_ENABLED
#define NRF_ATFIFO_CONFIG_LOG_ENABLED 0
#endif
// <o> NRF_ATFIFO_CONFIG_LOG_LEVEL  - Default Severity level
 
// <0=> Off 
// <1=> Error 
// <2=> Warning 
// <3=> Info 
// <4=> Debug 

#ifndef NRF_ATFIFO_CONFIG_LOG_LEVEL
#define NRF_ATFIFO_CONFIG_LOG_LEVEL 3
#endif

// <o> NRF_ATFIFO_CONFIG_LOG_INIT_FILTER_LEVEL  - Initial severity level if dynamic filtering is enabled
 
// <0=> Off 
// <1=> Error 
// <2=> Warning 
// <3=> Info 
// <4=> Debug 

#ifndef NRF_ATFIFO_CONFIG_LOG_INIT_FILTER_LEVEL
#define NRF_ATFIFO_CONFIG_LOG_INIT_FILTER_LEVEL 3
#endif

// <o> NRF_ATFIFO_CONFIG_INFO_COLOR  - ANSI escape code prefix.
 
// <0=> Default 
// <1=> Black 
// <2=> Red 
// <3=> Green 
// <4=> Yellow 
// <5=> Blue 
// <6=> Magenta 
// <7=> Cyan 
// <8=> White 

#ifndef NRF_ATFIFO_CONFIG_INFO_COLOR
#define NRF_ATFIFO_CONFIG_INFO_COLOR 0
#endif

// <o> NRF_ATFIFO_CONFIG_DEBUG_COLOR  - ANSI escape code prefix.
 
// <0=> Default 
// <1=> Black 
// <2=> Red 
// <3=> Green 
// <4=> Yellow 
// <5=> Blue 
// <6=> Magenta 
// <7=> Cyan 
// <8=> White 

#ifndef NRF_ATFIFO_CONFIG_DEBUG_COLOR
#define NRF_ATFIFO_CONFIG_DEBUG_COLOR 0
#endif

// </e>

// <e> NRF_BALLOC_CONFIG_LOG_ENABLED - Enables logging in the module.
//==========================================================
#ifndef NRF_BALLOC_CONFIG_LOG_ENABLED
#define NRF_BALLOC_CONFIG_LOG_ENABLED 0
#endif
// <o> NRF_BALLOC_CONFIG_LOG_LEVEL  - Default Severity level
 
// <0=> Off 
// <1=> Error 
// <2=> Warning 
// <3=> Info 
// <4=> Debug 

#ifndef NRF_BALLOC_CONFIG_LOG_LEVEL
#define NRF_BALLOC_CONFIG_LOG_LEVEL 3
#endif

// <o> NRF_BALLOC_CONFIG_INITIAL_LOG_LEVEL  - Initial severity level if dynamic filtering is enabled.
 

// <i> If module generates a lot of logs, initial log level can
// <i> be decreased to prevent flooding. Severity level can be
// <i> increased on instance basis.
// <0=> Off 
// <1=> Error 
// <2=> Warning 
// <3=> Info 
// <4=> Debug 

#ifndef NRF_BALLOC_CONFIG_INITIAL_LOG_LEVEL
#define NRF_BALLOC_CONFIG_INITIAL_LOG_LEVEL 3
#endif

// <o> NRF_BALLOC_CONFIG_INFO_COLOR  - ANSI escape code prefix.
 
// <0=> Default 
// <1=> Black 
// <2=> Red 
// <3=> Green 
// <4=> Yellow 
// <5=> Blue 
// <6=> Magenta 
// <7=> Cyan 
// <8=> White 

#ifndef NRF_BALLOC_CONFIG_INFO_COLOR
#define NRF_BALLOC_CONFIG_INFO_COLOR 0
#endif

// <o> NRF_BALLOC_CONFIG_DEBUG_COLOR  - ANSI escape code prefix.
 
// <0=> Default 
// <1=> Black 
// <2=> Red 
// <3=> Green 
// <4=> Yellow 
// <5=> Blue 
// <6=> Magenta 
// <7=> Cyan 
// <8=> White 

#ifndef NRF_BALLOC_CONFIG_DEBUG_COLOR
#define NRF_BALLOC_CONFIG_DEBUG_COLOR 0
#endif

// </e>

// <e> NRF_BLOCK_DEV_EMPTY_CONFIG_LOG_ENABLED - Enables logging in the module.
//==========================================================
#ifndef NRF_BLOCK_DEV_EMPTY_CONFIG_LOG_ENABLED
#define NRF_BLOCK_DEV_EMPTY_CONFIG_LOG_ENABLED 0
#endif
// <o> NRF_BLOCK_DEV_EMPTY_CONFIG_LOG_LEVEL  - Default Severity level
 
// <0=> Off 
// <1=> Error 
// <2=> Warning 
// <3=> Info 
// <4=> Debug 

#ifndef NRF_BLOCK_DEV_EMPTY_CONFIG_LOG_LEVEL
#define NRF_BLOCK_DEV_EMPTY_CONFIG_LOG_LEVEL 3
#endif

// <o> NRF_BLOCK_DEV_EMPTY_CONFIG_LOG_INIT_FILTER_LEVEL  - Initial severity level if dynamic filtering is enabled
 
// <0=> Off 
// <1=> Error 
// <2=> Warning 
// <3=> Info 
// <4=> Debug 

#ifndef NRF_BLOCK_DEV_EMPTY_CONFIG_LOG_INIT_FILTER_LEVEL
#define NRF_BLOCK_DEV_EMPTY_CONFIG_LOG_INIT_FILTER_LEVEL 3
#endif

// <o> NRF_BLOCK_DEV_EMPTY_CONFIG_INFO_COLOR  - ANSI escape code prefix.
 
// <0=> Default 
// <1=> Black 
// <2=> Red 
// <3=> Green 
// <4=> Yellow 
// <5=> Blue 
// <6=> Magenta 
// <7=> Cyan 
// <8=> White 

#ifndef NRF_BLOCK_DEV_EMPTY_CONFIG_INFO_COLOR
#define NRF_BLOCK_DEV_EMPTY_CONFIG_INFO_COLOR 0
#endif

// <o> NRF_BLOCK_DEV_EMPTY_CONFIG_DEBUG_COLOR  - ANSI escape code prefix.
 
// <0=> Default 
// <1=> Black 
// <2=> Red 
// <3=> Green 
// <4=> Yellow 
// <5=> Blue 
// <6=> Magenta 
// <7=> Cyan 
// <8=> White 

#ifndef NRF_BLOCK_DEV_EMPTY_CONFIG_DEBUG_COLOR
#define NRF_BLOCK_DEV_EMPTY_CONFIG_DEBUG_COLOR 0
#endif

// </e>

// <e> NRF_BLOCK_DEV_QSPI_CONFIG_LOG_ENABLED - Enables logging in the module.
//==========================================================
#ifndef NRF_BLOCK_DEV_QSPI_CONFIG_LOG_ENABLED
#define NRF_BLOCK_DEV_QSPI_CONFIG_LOG_ENABLED 0
#endif
// <o> NRF_BLOCK_DEV_QSPI_CONFIG_LOG_LEVEL  - Default Severity level
 
// <0=> Off 
// <1=> Error 
// <2=> Warning 
// <3=> Info 
// <4=> Debug 

#ifndef NRF_BLOCK_DEV_QSPI_CONFIG_LOG_LEVEL
#define NRF_BLOCK_DEV_QSPI_CONFIG_LOG_LEVEL 3
#endif

// <o> NRF_BLOCK_DEV_QSPI_CONFIG_LOG_INIT_FILTER_LEVEL  - Initial severity level if dynamic filtering is enabled
 
// <0=> Off 
// <1=> Error 
// <2=> Warning 
// <3=> Info 
// <4=> Debug 

#ifndef NRF_BLOCK_DEV_QSPI_CONFIG_LOG_INIT_FILTER_LEVEL
#define NRF_BLOCK_DEV_QSPI_CONFIG_LOG_INIT_FILTER_LEVEL 3
#endif

// <o> NRF_BLOCK_DEV_QSPI_CONFIG_INFO_COLOR  - ANSI escape code prefix.
 
// <0=> Default 
// <1=> Black 
// <2=> Red 
// <3=> Green 
// <4=> Yellow 
// <5=> Blue 
// <6=> Magenta 
// <7=> Cyan 
// <8=> White 

#ifndef NRF_BLOCK_DEV_QSPI_CONFIG_INFO_COLOR
#define NRF_BLOCK_DEV_QSPI_CONFIG_INFO_COLOR 0
#endif

// <o> NRF_BLOCK_DEV_QSPI_CONFIG_DEBUG_COLOR  - ANSI escape code prefix.
 
// <0=> Default 
// <1=> Black 
// <2=> Red 
// <3=> Green 
// <4=> Yellow 
// <5=> Blue 
// <6=> Magenta 
// <7=> Cyan 
// <8=> White 

#ifndef NRF_BLOCK_DEV_QSPI_CONFIG_DEBUG_COLOR
#define NRF_BLOCK_DEV_QSPI_CONFIG_DEBUG_COLOR 0
#endif

// </e>

// <e> NRF_BLOCK_DEV_RAM_CONFIG_LOG_ENABLED - Enables logging in the module.
//==========================================================
#ifndef NRF_BLOCK_DEV_RAM_CONFIG_LOG_ENABLED
#define NRF_BLOCK_DEV_RAM_CONFIG_LOG_ENABLED 0
#endif
// <o> NRF_BLOCK_DEV_RAM_CONFIG_LOG_LEVEL  - Default Severity level
 
// <0=> Off 
// <1=> Error 
// <2=> Warning 
// <3=> Info 
// <4=> Debug 

#ifndef NRF_BLOCK_DEV_RAM_CONFIG_LOG_LEVEL
#define NRF_BLOCK_DEV_RAM_CONFIG_LOG_LEVEL 3
#endif

// <o> NRF_BLOCK_DEV_RAM_CONFIG_LOG_INIT_FILTER_LEVEL  - Initial severity level if dynamic filtering is enabled
 
// <0=> Off 
// <1=> Error 
// <2=> Warning 
// <3=> Info 
// <4=> Debug 

#ifndef NRF_BLOCK_DEV_RAM_CONFIG_LOG_INIT_FILTER_LEVEL
#define NRF_BLOCK_DEV_RAM_CONFIG_LOG_INIT_FILTER_LEVEL 3
#endif

// <o> NRF_BLOCK_DEV_RAM_CONFIG_INFO_COLOR  - ANSI escape code prefix.
 
// <0=> Default 
// <1=> Black 
// <2=> Red 
// <3=> Green 
// <4=> Yellow 
// <5=> Blue 
// <6=> Magenta 
// <7=> Cyan 
// <8=> White 

#ifndef NRF_BLOCK_DEV_RAM_CONFIG_INFO_COLOR
#define NRF_BLOCK_DEV_RAM_CONFIG_INFO_COLOR 0
#endif

// <o> NRF_BLOCK_DEV_RAM_CONFIG_DEBUG_COLOR  - ANSI escape code prefix.
 
// <0=> Default 
// <1=> Black 
// <2=> Red 
// <3=> Green 
// <4=> Yellow 
// <5=> Blue 
// <6=> Magenta 
// <7=> Cyan 
// <8=> White 

#ifndef NRF_BLOCK_DEV_RAM_CONFIG_DEBUG_COLOR
#define NRF_BLOCK_DEV_RAM_CONFIG_DEBUG_COLOR 0
#endif

// </e>

// <e> NRF_CLI_BLE_UART_CONFIG_LOG_ENABLED - Enables logging in the module.
//==========================================================
#ifndef NRF_CLI_BLE_UART_CONFIG_LOG_ENABLED
#define NRF_CLI_BLE_UART_CONFIG_LOG_ENABLED 0
#endif
// <o> NRF_CLI_BLE_UART_CONFIG_LOG_LEVEL  - Default Severity level
 
// <0=> Off 
// <1=> Error 
// <2=> Warning 
// <3=> Info 
// <4=> Debug 

#ifndef NRF_CLI_BLE_UART_CONFIG_LOG_LEVEL
#define NRF_CLI_BLE_UART_CONFIG_LOG_LEVEL 3
#endif

// <o> NRF_CLI_BLE_UART_CONFIG_INFO_COLOR  - ANSI escape code prefix.
 
// <0=> Default 
// <1=> Black 
// <2=> Red 
// <3=> Green 
// <4=> Yellow 
// <5=> Blue 
// <6=> Magenta 
// <7=> Cyan 
// <8=> White 

#ifndef NRF_CLI_BLE_UART_CONFIG_INFO_COLOR
#define NRF_CLI_BLE_UART_CONFIG_INFO_COLOR 0
#endif

// <o> NRF_CLI_BLE_UART_CONFIG_DEBUG_COLOR  - ANSI escape code prefix.
 
// <0=> Default 
// <1=> Black 
// <2=> Red 
// <3=> Green 
// <4=> Yellow 
// <5=> Blue 
// <6=> Magenta 
// <7=> Cyan 
// <8=> White 

#ifndef NRF_CLI_BLE_UART_CONFIG_DEBUG_COLOR
#define NRF_CLI_BLE_UART_CONFIG_DEBUG_COLOR 0
#endif

// </e>

// <e> NRF_CLI_LIBUARTE_CONFIG_LOG_ENABLED - Enables logging in the module.
//==========================================================
#ifndef NRF_CLI_LIBUARTE_CONFIG_LOG_ENABLED
#define NRF_CLI_LIBUARTE_CONFIG_LOG_ENABLED 0
#endif
// <o> NRF_CLI_LIBUARTE_CONFIG_LOG_LEVEL  - Default Severity level
 
// <0=> Off 
// <1=> Error 
// <2=> Warning 
// <3=> Info 
// <4=> Debug 

#ifndef NRF_CLI_LIBUARTE_CONFIG_LOG_LEVEL
#define NRF_CLI_LIBUARTE_CONFIG_LOG_LEVEL 3
#endif

// <o> NRF_CLI_LIBUARTE_CONFIG_INFO_COLOR  - ANSI escape code prefix.
 
// <0=> Default 
// <1=> Black 
// <2=> Red 
// <3=> Green 
// <4=> Yellow 
// <5=> Blue 
// <6=> Magenta 
// <7=> Cyan 
// <8=> White 

#ifndef NRF_CLI_LIBUARTE_CONFIG_INFO_COLOR
#define NRF_CLI_LIBUARTE_CONFIG_INFO_COLOR 0
#endif

// <o> NRF_CLI_LIBUARTE_CONFIG_DEBUG_COLOR  - ANSI escape code prefix.
 
// <0=> Default 
// <1=> Black 
// <2=> Red 
// <3=> Green 
// <4=> Yellow 
// <5=> Blue 
// <6=> Magenta 
// <7=> Cyan 
// <8=> White 

#ifndef NRF_CLI_LIBUARTE_CONFIG_DEBUG_COLOR
#define NRF_CLI_LIBUARTE_CONFIG_DEBUG_COLOR 0
#endif

// </e>

// <e> NRF_CLI_UART_CONFIG_LOG_ENABLED - Enables logging in the module.
//==========================================================
#ifndef NRF_CLI_UART_CONFIG_LOG_ENABLED
#define NRF_CLI_UART_CONFIG_LOG_ENABLED 0
#endif
// <o> NRF_CLI_UART_CONFIG_LOG_LEVEL  - Default Severity level
 
// <0=> Off 
// <1=> Error 
// <2=> Warning 
// <3=> Info 
// <4=> Debug 

#ifndef NRF_CLI_UART_CONFIG_LOG_LEVEL
#define NRF_CLI_UART_CONFIG_LOG_LEVEL 3
#endif

// <o> NRF_CLI_UART_CONFIG_INFO_COLOR  - ANSI escape code prefix.
 
// <0=> Default 
// <1=> Black 
// <2=> Red 
// <3=> Green 
// <4=> Yellow 
// <5=> Blue 
// <6=> Magenta 
// <7=> Cyan 
// <8=> White 

#ifndef NRF_CLI_UART_CONFIG_INFO_COLOR
#define NRF_CLI_UART_CONFIG_INFO_COLOR 0
#endif

// <o> NRF_CLI_UART_CONFIG_DEBUG_COLOR  - ANSI escape code prefix.
 
// <0=> Default 
// <1=> Black 
// <2=> Red 
// <3=> Green 
// <4=> Yellow 
// <5=> Blue 
// <6=> Magenta 
// <7=> Cyan 
// <8=> White 

#ifndef NRF_CLI_UART_CONFIG_DEBUG_COLOR
#define NRF_CLI_UART_CONFIG_DEBUG_COLOR 0
#endif

// </e>

// <e> NRF_LIBUARTE_CONFIG_LOG_ENABLED - Enables logging in the module.
//==========================================================
#ifndef NRF_LIBUARTE_CONFIG_LOG_ENABLED
#define NRF_LIBUARTE_CONFIG_LOG_ENABLED 0
#endif
// <o> NRF_LIBUARTE_CONFIG_LOG_LEVEL  - Default Severity level
 
// <0=> Off 
// <1=> Error 
// <2=> Warning 
// <3=> Info 
// <4=> Debug 

#ifndef NRF_LIBUARTE_CONFIG_LOG_LEVEL
#define NRF_LIBUARTE_CONFIG_LOG_LEVEL 3
#endif

// <o> NRF_LIBUARTE_CONFIG_INFO_COLOR  - ANSI escape code prefix.
 
// <0=> Default 
// <1=> Black 
// <2=> Red 
// <3=> Green 
// <4=> Yellow 
// <5=> Blue 
// <6=> Magenta 
// <7=> Cyan 
// <8=> White 

#ifndef NRF_LIBUARTE_CONFIG_INFO_COLOR
#define NRF_LIBUARTE_CONFIG_INFO_COLOR 0
#endif

// <o> NRF_LIBUARTE_CONFIG_DEBUG_COLOR  - ANSI escape code prefix.
 
// <0=> Default 
// <1=> Black 
// <2=> Red 
// <3=> Green 
// <4=> Yellow 
// <5=> Blue 
// <6=> Magenta 
// <7=> Cyan 
// <8=> White 

#ifndef NRF_LIBUARTE_CONFIG_DEBUG_COLOR
#define NRF_LIBUARTE_CONFIG_DEBUG_COLOR 0
#endif

// </e>

// <e> NRF_MEMOBJ_CONFIG_LOG_ENABLED - Enables logging in the module.
//==========================================================
#ifndef NRF_MEMOBJ_CONFIG_LOG_ENABLED
#define NRF_MEMOBJ_CONFIG_LOG_ENABLED 0
#endif
// <o> NRF_MEMOBJ_CONFIG_LOG_LEVEL  - Default Severity level
 
// <0=> Off 
// <1=> Error 
// <2=> Warning 
// <3=> Info 
// <4=> Debug 

#ifndef NRF_MEMOBJ_CONFIG_LOG_LEVEL
#define NRF_MEMOBJ_CONFIG_LOG_LEVEL 3
#endif

// <o> NRF_MEMOBJ_CONFIG_INFO_COLOR  - ANSI escape code prefix.
 
// <0=> Default 
// <1=> Black 
// <2=> Red 
// <3=> Green 
// <4=> Yellow 
// <5=> Blue 
// <6=> Magenta 
// <7=> Cyan 
// <8=> White 

#ifndef NRF_MEMOBJ_CONFIG_INFO_COLOR
#define NRF_MEMOBJ_CONFIG_INFO_COLOR 0
#endif

// <o> NRF_MEMOBJ_CONFIG_DEBUG_COLOR  - ANSI escape code prefix.
 
// <0=> Default 
// <1=> Black 
// <2=> Red 
// <3=> Green 
// <4=> Yellow 
// <5=> Blue 
// <6=> Magenta 
// <7=> Cyan 
// <8=> White 

#ifndef NRF_MEMOBJ_CONFIG_DEBUG_COLOR
#define NRF_MEMOBJ_CONFIG_DEBUG_COLOR 0
#endif

// </e>

// <e> NRF_PWR_MGMT_CONFIG_LOG_ENABLED - Enables logging in the module.
//==========================================================
#ifndef NRF_PWR_MGMT_CONFIG_LOG_ENABLED
#define NRF_PWR_MGMT_CONFIG_LOG_ENABLED 0
#endif
// <o> NRF_PWR_MGMT_CONFIG_LOG_LEVEL  - Default Severity level
 
// <0=> Off 
// <1=> Error 
// <2=> Warning 
// <3=> Info 
// <4=> Debug 

#ifndef NRF_PWR_MGMT_CONFIG_LOG_LEVEL
#define NRF_PWR_MGMT_CONFIG_LOG_LEVEL 3
#endif

// <o> NRF_PWR_MGMT_CONFIG_INFO_COLOR  - ANSI escape code prefix.
 
// <0=> Default 
// <1=> Black 
// <2=> Red 
// <3=> Green 
// <4=> Yellow 
// <5=> Blue 
// <6=> Magenta 
// <7=> Cyan 
// <8=> White 

#ifndef NRF_PWR_MGMT_CONFIG_INFO_COLOR
#define NRF_PWR_MGMT_CONFIG_INFO_COLOR 0
#endif

// <o> NRF_PWR_MGMT_CONFIG_DEBUG_COLOR  - ANSI escape code prefix.
 
// <0=> Default 
// <1=> Black 
// <2=> Red 
// <3=> Green 
// <4=> Yellow 
// <5=> Blue 
// <6=> Magenta 
// <7=> Cyan 
// <8=> White 

#ifndef NRF_PWR_MGMT_CONFIG_DEBUG_COLOR
#define NRF_PWR_MGMT_CONFIG_DEBUG_COLOR 0
#endif

// </e>

// <e> NRF_QUEUE_CONFIG_LOG_ENABLED - Enables logging in the module.
//==========================================================
#ifndef NRF_QUEUE_CONFIG_LOG_ENABLED
#define NRF_QUEUE_CONFIG_LOG_ENABLED 0
#endif
// <o> NRF_QUEUE_CONFIG_LOG_LEVEL  - Default Severity level
 
// <0=> Off 
// <1=> Error 
// <2=> Warning 
// <3=> Info 
// <4=> Debug 

#ifndef NRF_QUEUE_CONFIG_LOG_LEVEL
#define NRF_QUEUE_CONFIG_LOG_LEVEL 3
#endif

// <o> NRF_QUEUE_CONFIG_LOG_INIT_FILTER_LEVEL  - Initial severity level if dynamic filtering is enabled
 
// <0=> Off 
// <1=> Error 
// <2=> Warning 
// <3=> Info 
// <4=> Debug 

#ifndef NRF_QUEUE_CONFIG_LOG_INIT_FILTER_LEVEL
#define NRF_QUEUE_CONFIG_LOG_INIT_FILTER_LEVEL 3
#endif

// <o> NRF_QUEUE_CONFIG_INFO_COLOR  - ANSI escape code prefix.
 
// <0=> Default 
// <1=> Black 
// <2=> Red 
// <3=> Green 
// <4=> Yellow 
// <5=> Blue 
// <6=> Magenta 
// <7=> Cyan 
// <8=> White 

#ifndef NRF_QUEUE_CONFIG_INFO_COLOR
#define NRF_QUEUE_CONFIG_INFO_COLOR 0
#endif

// <o> NRF_QUEUE_CONFIG_DEBUG_COLOR  - ANSI escape code prefix.
 
// <0=> Default 
// <1=> Black 
// <2=> Red 
// <3=> Green 
// <4=> Yellow 
// <5=> Blue 
// <6=> Magenta 
// <7=> Cyan 
// <8=> White 

#ifndef NRF_QUEUE_CONFIG_DEBUG_COLOR
#define NRF_QUEUE_CONFIG_DEBUG_COLOR 0
#endif

// </e>

// <e> NRF_SDH_ANT_LOG_ENABLED - Enable logging in SoftDevice handler (ANT) module.
//==========================================================
#ifndef NRF_SDH_ANT_LOG_ENABLED
#define NRF_SDH_ANT_LOG_ENABLED 0
#endif
// <o> NRF_SDH_ANT_LOG_LEVEL  - Default Severity level
 
// <0=> Off 
// <1=> Error 
// <2=> Warning 
// <3=> Info 
// <4=> Debug 

#ifndef NRF_SDH_ANT_LOG_LEVEL
#define NRF_SDH_ANT_LOG_LEVEL 3
#endif

// <o> NRF_SDH_ANT_INFO_COLOR  - ANSI escape code prefix.
 
// <0=> Default 
// <1=> Black 
// <2=> Red 
// <3=> Green 
// <4=> Yellow 
// <5=> Blue 
// <6=> Magenta 
// <7=> Cyan 
// <8=> White 

#ifndef NRF_SDH_ANT_INFO_COLOR
#define NRF_SDH_ANT_INFO_COLOR 0
#endif

// <o> NRF_SDH_ANT_DEBUG_COLOR  - ANSI escape code prefix.
 
// <0=> Default 
// <1=> Black 
// <2=> Red 
// <3=> Green 
// <4=> Yellow 
// <5=> Blue 
// <6=> Magenta 
// <7=> Cyan 
// <8=> White 

#ifndef NRF_SDH_ANT_DEBUG_COLOR
#define NRF_SDH_ANT_DEBUG_COLOR 0
#endif

// </e>

// <e> NRF_SDH_BLE_LOG_ENABLED - Enable logging in SoftDevice handler (BLE) module.
//==========================================================
#ifndef NRF_SDH_BLE_LOG_ENABLED
#define NRF_SDH_BLE_LOG_ENABLED 1
#endif
// <o> NRF_SDH_BLE_LOG_LEVEL  - Default Severity level
 
// <0=> Off 
// <1=> Error 
// <2=> Warning 
// <3=> Info 
// <4=> Debug 

#ifndef NRF_SDH_BLE_LOG_LEVEL
#define NRF_SDH_BLE_LOG_LEVEL 3
#endif

// <o> NRF_SDH_BLE_INFO_COLOR  - ANSI escape code prefix.
 
// <0=> Default 
// <1=> Black 
// <2=> Red 
// <3=> Green 
// <4=> Yellow 
// <5=> Blue 
// <6=> Magenta 
// <7=> Cyan 
// <8=> White 

#ifndef NRF_SDH_BLE_INFO_COLOR
#define NRF_SDH_BLE_INFO_COLOR 0
#endif

// <o> NRF_SDH_BLE_DEBUG_COLOR  - ANSI escape code prefix.
 
// <0=> Default 
// <1=> Black 
// <2=> Red 
// <3=> Green 
// <4=> Yellow 
// <5=> Blue 
// <6=> Magenta 
// <7=> Cyan 
// <8=> White 

#ifndef NRF_SDH_BLE_DEBUG_COLOR
#define NRF_SDH_BLE_DEBUG_COLOR 0
#endif

// </e>

// <e> NRF_SDH_LOG_ENABLED - Enable logging in SoftDevice handler module.
//==========================================================
#ifndef NRF_SDH_LOG_ENABLED
#define NRF_SDH_LOG_ENABLED 1
#endif
// <o> NRF_SDH_LOG_LEVEL  - Default Severity level
 
// <0=> Off 
// <1=> Error 
// <2=> Warning 
// <3=> Info 
// <4=> Debug 

#ifndef NRF_SDH_LOG_LEVEL
#define NRF_SDH_LOG_LEVEL 3
#endif

// <o> NRF_SDH_INFO_COLOR  - ANSI escape code prefix.
 
// <0=> Default 
// <1=> Black 
// <2=> Red 
// <3=> Green 
// <4=> Yellow 
// <5=> Blue 
// <6=> Magenta 
// <7=> Cyan 
// <8=> White 

#ifndef NRF_SDH_INFO_COLOR
#define NRF_SDH_INFO_COLOR 0
#endif

// <o> NRF_SDH_DEBUG_COLOR  - ANSI escape code prefix.
 
// <0=> Default 
// <1=> Black 
// <2=> Red 
// <3=> Green 
// <4=> Yellow 
// <5=> Blue 
// <6=> Magenta 
// <7=> Cyan 
// <8=> White 

#ifndef NRF_SDH_DEBUG_COLOR
#define NRF_SDH_DEBUG_COLOR 0
#endif

// </e>

// <e> NRF_SDH_SOC_LOG_ENABLED - Enable logging in SoftDevice handler (SoC) module.
//==========================================================
#ifndef NRF_SDH_SOC_LOG_ENABLED
#define NRF_SDH_SOC_LOG_ENABLED 1
#endif
// <o> NRF_SDH_SOC_LOG_LEVEL  - Default Severity level
 
// <0=> Off 
// <1=> Error 
// <2=> Warning 
// <3=> Info 
// <4=> Debug 

#ifndef NRF_SDH_SOC_LOG_LEVEL
#define NRF_SDH_SOC_LOG_LEVEL 3
#endif

// <o> NRF_SDH_SOC_INFO_COLOR  - ANSI escape code prefix.
 
// <0=> Default 
// <1=> Black 
// <2=> Red 
// <3=> Green 
// <4=> Yellow 
// <5=> Blue 
// <6=> Magenta 
// <7=> Cyan 
// <8=> White 

#ifndef NRF_SDH_SOC_INFO_COLOR
#define NRF_SDH_SOC_INFO_COLOR 0
#endif

// <o> NRF_SDH_SOC_DEBUG_COLOR  - ANSI escape code prefix.
 
// <0=> Default 
// <1=> Black 
// <2=> Red 
// <3=> Green 
// <4=> Yellow 
// <5=> Blue 
// <6=> Magenta 
// <7=> Cyan 
// <8=> White 

#ifndef NRF_SDH_SOC_DEBUG_COLOR
#define NRF_SDH_SOC_DEBUG_COLOR 0
#endif

// </e>

// <e> NRF_SORTLIST_CONFIG_LOG_ENABLED - Enables logging in the module.
//==========================================================
#ifndef NRF_SORTLIST_CONFIG_LOG_ENABLED
#define NRF_SORTLIST_CONFIG_LOG_ENABLED 0
#endif
// <o> NRF_SORTLIST_CONFIG_LOG_LEVEL  - Default Severity level
 
// <0=> Off 
// <1=> Error 
// <2=> Warning 
// <3=> Info 
// <4=> Debug 

#ifndef NRF_SORTLIST_CONFIG_LOG_LEVEL
#define NRF_SORTLIST_CONFIG_LOG_LEVEL 3
#endif

// <o> NRF_SORTLIST_CONFIG_INFO_COLOR  - ANSI escape code prefix.
 
// <0=> Default 
// <1=> Black 
// <2=> Red 
// <3=> Green 
// <4=> Yellow 
// <5=> Blue 
// <6=> Magenta 
// <7=> Cyan 
// <8=> White 

#ifndef NRF_SORTLIST_CONFIG_INFO_COLOR
#define NRF_SORTLIST_CONFIG_INFO_COLOR 0
#endif

// <o> NRF_SORTLIST_CONFIG_DEBUG_COLOR  - ANSI escape code prefix.
 
// <0=> Default 
// <1=> Black 
// <2=> Red 
// <3=> Green 
// <4=> Yellow 
// <5=> Blue 
// <6=> Magenta 
// <7=> Cyan 
// <8=> White 

#ifndef NRF_SORTLIST_CONFIG_DEBUG_COLOR
#define NRF_SORTLIST_CONFIG_DEBUG_COLOR 0
#endif

// </e>

// <e> NRF_TWI_SENSOR_CONFIG_LOG_ENABLED - Enables logging in the module.
//==========================================================
#ifndef NRF_TWI_SENSOR_CONFIG_LOG_ENABLED
#define NRF_TWI_SENSOR_CONFIG_LOG_ENABLED 0
#endif
// <o> NRF_TWI_SENSOR_CONFIG_LOG_LEVEL  - Default Severity level
 
// <0=> Off 
// <1=> Error 
// <2=> Warning 
// <3=> Info 
// <4=> Debug 

#ifndef NRF_TWI_SENSOR_CONFIG_LOG_LEVEL
#define NRF_TWI_SENSOR_CONFIG_LOG_LEVEL 3
#endif

// <o> NRF_TWI_SENSOR_CONFIG_INFO_COLOR  - ANSI escape code prefix.
 
// <0=> Default 
// <1=> Black 
// <2=> Red 
// <3=> Green 
// <4=> Yellow 
// <5=> Blue 
// <6=> Magenta 
// <7=> Cyan 
// <8=> White 

#ifndef NRF_TWI_SENSOR_CONFIG_INFO_COLOR
#define NRF_TWI_SENSOR_CONFIG_INFO_COLOR 0
#endif

// <o> NRF_TWI_SENSOR_CONFIG_DEBUG_COLOR  - ANSI escape code prefix.
 
// <0=> Default 
// <1=> Black 
// <2=> Red 
// <3=> Green 
// <4=> Yellow 
// <5=> Blue 
// <6=> Magenta 
// <7=> Cyan 
// <8=> White 

#ifndef NRF_TWI_SENSOR_CONFIG_DEBUG_COLOR
#define NRF_TWI_SENSOR_CONFIG_DEBUG_COLOR 0
#endif

// </e>

// <e> PM_LOG_ENABLED - Enable logging in Peer Manager and its submodules.
//==========================================================
#ifndef PM_LOG_ENABLED
#define PM_LOG_ENABLED 1
#endif
// <o> PM_LOG_LEVEL  - Default Severity level
 
// <0=> Off 
// <1=> Error 
// <2=> Warning 
// <3=> Info 
// <4=> Debug 

#ifndef PM_LOG_LEVEL
#define PM_LOG_LEVEL 3
#endif

// <o> PM_LOG_INFO_COLOR  - ANSI escape code prefix.
 
// <0=> Default 
// <1=> Black 
// <2=> Red 
// <3=> Green 
// <4=> Yellow 
// <5=> Blue 
// <6=> Magenta 
// <7=> Cyan 
// <8=> White 

#ifndef PM_LOG_INFO_COLOR
#define PM_LOG_INFO_COLOR 0
#endif

// <o> PM_LOG_DEBUG_COLOR  - ANSI escape code prefix.
 
// <0=> Default 
// <1=> Black 
// <2=> Red 
// <3=> Green 
// <4=> Yellow 
// <5=> Blue 
// <6=> Magenta 
// <7=> Cyan 
// <8=> White 

#ifndef PM_LOG_DEBUG_COLOR
#define PM_LOG_DEBUG_COLOR 0
#endif

// </e>

// </h> 
//==========================================================

// <h> nrf_log in nRF_Serialization 

//==========================================================
// <e> SER_HAL_TRANSPORT_CONFIG_LOG_ENABLED - Enables logging in the module.
//==========================================================
#ifndef SER_HAL_TRANSPORT_CONFIG_LOG_ENABLED
#define SER_HAL_TRANSPORT_CONFIG_LOG_ENABLED 0
#endif
// <o> SER_HAL_TRANSPORT_CONFIG_LOG_LEVEL  - Default Severity level
 
// <0=> Off 
// <1=> Error 
// <2=> Warning 
// <3=> Info 
// <4=> Debug 

#ifndef SER_HAL_TRANSPORT_CONFIG_LOG_LEVEL
#define SER_HAL_TRANSPORT_CONFIG_LOG_LEVEL 3
#endif

// <o> SER_HAL_TRANSPORT_CONFIG_INFO_COLOR  - ANSI escape code prefix.
 
// <0=> Default 
// <1=> Black 
// <2=> Red 
// <3=> Green 
// <4=> Yellow 
// <5=> Blue 
// <6=> Magenta 
// <7=> Cyan 
// <8=> White 

#ifndef SER_HAL_TRANSPORT_CONFIG_INFO_COLOR
#define SER_HAL_TRANSPORT_CONFIG_INFO_COLOR 0
#endif

// <o> SER_HAL_TRANSPORT_CONFIG_DEBUG_COLOR  - ANSI escape code prefix.
 
// <0=> Default 
// <1=> Black 
// <2=> Red 
// <3=> Green 
// <4=> Yellow 
// <5=> Blue 
// <6=> Magenta 
// <7=> Cyan 
// <8=> White 

#ifndef SER_HAL_TRANSPORT_CONFIG_DEBUG_COLOR
#define SER_HAL_TRANSPORT_CONFIG_DEBUG_COLOR 0
#endif

// </e>

// </h> 
//==========================================================

// </h> 
//==========================================================

// </e>

// <q> NRF_LOG_STR_FORMATTER_TIMESTAMP_FORMAT_ENABLED  - nrf_log_str_formatter - Log string formatter
 

#ifndef NRF_LOG_STR_FORMATTER_TIMESTAMP_FORMAT_ENABLED
#define NRF_LOG_STR_FORMATTER_TIMESTAMP_FORMAT_ENABLED 1
#endif

// </h> 
//==========================================================

// <h> nRF_SoftDevice 

//==========================================================
// <e> NRF_SDH_BLE_ENABLED - nrf_sdh_ble - SoftDevice BLE event handler
//==========================================================
#ifndef NRF_SDH_BLE_ENABLED
#define NRF_SDH_BLE_ENABLED 1
#endif
// <h> BLE Stack configuration - Stack configuration parameters

// <i> The SoftDevice handler will configure the stack with these parameters when calling @ref nrf_sdh_ble_default_cfg_set.
// <i> Other libraries might depend on these values; keep them up-to-date even if you are not explicitely calling @ref nrf_sdh_ble_default_cfg_set.
//==========================================================
// <o> NRF_SDH_BLE_GAP_DATA_LENGTH   <27-251> 


// <i> Requested BLE GAP data length to be negotiated.

#ifndef NRF_SDH_BLE_GAP_DATA_LENGTH
#define NRF_SDH_BLE_GAP_DATA_LENGTH 27
#endif

// <o> NRF_SDH_BLE_PERIPHERAL_LINK_COUNT - Maximum number of peripheral links. 
#ifndef NRF_SDH_BLE_PERIPHERAL_LINK_COUNT
#define NRF_SDH_BLE_PERIPHERAL_LINK_COUNT 1
#endif

// <o> NRF_SDH_BLE_CENTRAL_LINK_COUNT - Maximum number of central links. 
#ifndef NRF_SDH_BLE_CENTRAL_LINK_COUNT
#define NRF_SDH_BLE_CENTRAL_LINK_COUNT 0
#endif

// <o> NRF_SDH_BLE_TOTAL_LINK_COUNT - Total link count. 
// <i> Maximum number of total concurrent connections using the default configuration.

#ifndef NRF_SDH_BLE_TOTAL_LINK_COUNT
#define NRF_SDH_BLE_TOTAL_LINK_COUNT 1
#endif

// <o> NRF_SDH_BLE_GAP_EVENT_LENGTH - GAP event length. 
// <i> The time set aside for this connection on every connection interval in 1.25 ms units.

#ifndef NRF_SDH_BLE_GAP_EVENT_LENGTH
#define NRF_SDH_BLE_GAP_EVENT_LENGTH 6
#endif

// <o> NRF_SDH_BLE_GATT_MAX_MTU_SIZE - Static maximum MTU size. 
#ifndef NRF_SDH_BLE_GATT_MAX_MTU_SIZE
#define NRF_SDH_BLE_GATT_MAX_MTU_SIZE 247
#endif

// <o> NRF_SDH_BLE_GATTS_ATTR_TAB_SIZE - Attribute Table size in bytes. The size must be a multiple of 4. 
#ifndef NRF_SDH_BLE_GATTS_ATTR_TAB_SIZE
#define NRF_SDH_BLE_GATTS_ATTR_TAB_SIZE 1408
#endif

// <o> NRF_SDH_BLE_VS_UUID_COUNT - The number of vendor-specific UUIDs. 
#ifndef NRF_SDH_BLE_VS_UUID_COUNT
#define NRF_SDH_BLE_VS_UUID_COUNT 1
#endif

// <q> NRF_SDH_BLE_SERVICE_CHANGED  - Include the Service Changed characteristic in the Attribute Table.
 

#ifndef NRF_SDH_BLE_SERVICE_CHANGED
#define NRF_SDH_BLE_SERVICE_CHANGED 0
#endif

// </h> 
//==========================================================

// <h> BLE Observers - Observers and priority levels

//==========================================================
// <o> NRF_SDH_BLE_OBSERVER_PRIO_LEVELS - Total number of priority levels for BLE observers. 
// <i> This setting configures the number of priority levels available for BLE event handlers.
// <i> The priority level of a handler determines the order in which it receives events, with respect to other handlers.

#ifndef NRF_SDH_BLE_OBSERVER_PRIO_LEVELS
#define NRF_SDH_BLE_OBSERVER_PRIO_LEVELS 4
#endif

// <h> BLE Observers priorities - Invididual priorities

//==========================================================
// <o> BLE_ADV_BLE_OBSERVER_PRIO  
// <i> Priority with which BLE events are dispatched to the Advertising module.

#ifndef BLE_ADV_BLE_OBSERVER_PRIO
#define BLE_ADV_BLE_OBSERVER_PRIO 1
#endif

// <o> BLE_ANCS_C_BLE_OBSERVER_PRIO  
// <i> Priority with which BLE events are dispatched to the Apple Notification Service Client.

#ifndef BLE_ANCS_C_BLE_OBSERVER_PRIO
#define BLE_ANCS_C_BLE_OBSERVER_PRIO 2
#endif
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
