nico-malkov/variometer/software/nRF5_SDK_17.1.0/examples/peripheral/variometer_v143/icm20948/invensense/Icm20948Setup.c

/** ________________________________________________________________________________________________________
 * Copyright (c) 2015-2015 InvenSense Inc. All rights reserved.
 *
 * This software, related documentation and any modifications thereto (collectively “Software”) is subject
 * to InvenSense and its licensors' intellectual property rights under U.S. and international copyright
 * and other intellectual property rights laws.
 *
 * InvenSense and its licensors retain all intellectual property and proprietary rights in and to the Software
 * and any use, reproduction, disclosure or distribution of the Software without an express license agreement
 * from InvenSense is strictly prohibited.
 *
 * EXCEPT AS OTHERWISE PROVIDED IN A LICENSE AGREEMENT BETWEEN THE PARTIES, THE SOFTWARE IS
 * PROVIDED "AS IS", WITHOUT WARRANTY OF ANY KIND, EXPRESS OR IMPLIED, INCLUDING BUT NOT LIMITED
 * TO THE WARRANTIES OF MERCHANTABILITY, FITNESS FOR A PARTICULAR PURPOSE AND NON-INFRINGEMENT.
 * EXCEPT AS OTHERWISE PROVIDED IN A LICENSE AGREEMENT BETWEEN THE PARTIES, IN NO EVENT SHALL
 * INVENSENSE BE LIABLE FOR ANY DIRECT, SPECIAL, INDIRECT, INCIDENTAL, OR CONSEQUENTIAL DAMAGES, OR ANY
 * DAMAGES WHATSOEVER RESULTING FROM LOSS OF USE, DATA OR PROFITS, WHETHER IN AN ACTION OF CONTRACT,
 * NEGLIGENCE OR OTHER TORTIOUS ACTION, ARISING OUT OF OR IN CONNECTION WITH THE USE OR PERFORMANCE
 * OF THE SOFTWARE.
 * ________________________________________________________________________________________________________
 */
#include "SensorTypes.h"

#include "Icm20948Setup.h"
#include "Icm20948.h"
#include "Icm20948Defs.h"
#include "Icm20948DataBaseDriver.h"
#include "Icm20948DataBaseControl.h"
#include "Icm20948MPUFifoControl.h"
#include "Icm20948Augmented.h"
#include "Icm20948LoadFirmware.h"
#include "Icm20948Dmp3Driver.h"

//#include "nrf_log.h" // does not work



#include <assert.h>

/** @brief Set of flags for BAC state */
#define BAC_DRIVE   0x01
#define BAC_WALK    0x02
#define BAC_RUN     0x04
#define BAC_BIKE    0x08
#define BAC_TILT    0x10
#define BAC_STILL   0x20

/** @brief Conversion from DMP units to float format for compass scale */
#define DMP_UNIT_TO_FLOAT_COMPASS_CONVERSION      (1/(float)(1UL<<16))
//! Convert the \a value from QN value to float. \ingroup invn_macro 
#define INVN_FXP_TO_FLT(value, shift)	( (float)  (int32_t)(value) / (float)(1ULL << (shift)) ) 
static uint8_t sensor_type_2_android_sensor(enum inv_icm20948_sensor sensor)
{
	switch(sensor) {
	case INV_ICM20948_SENSOR_ACCELEROMETER:                 return ANDROID_SENSOR_ACCELEROMETER;
	case INV_ICM20948_SENSOR_GYROSCOPE:                     return ANDROID_SENSOR_GYROSCOPE;
	case INV_ICM20948_SENSOR_RAW_ACCELEROMETER:             return ANDROID_SENSOR_RAW_ACCELEROMETER;
	case INV_ICM20948_SENSOR_RAW_GYROSCOPE:                 return ANDROID_SENSOR_RAW_GYROSCOPE;
	case INV_ICM20948_SENSOR_MAGNETIC_FIELD_UNCALIBRATED:   return ANDROID_SENSOR_MAGNETIC_FIELD_UNCALIBRATED;
	case INV_ICM20948_SENSOR_GYROSCOPE_UNCALIBRATED:        return ANDROID_SENSOR_GYROSCOPE_UNCALIBRATED;
	case INV_ICM20948_SENSOR_ACTIVITY_CLASSIFICATON:        return ANDROID_SENSOR_ACTIVITY_CLASSIFICATON;
	case INV_ICM20948_SENSOR_STEP_DETECTOR:                 return ANDROID_SENSOR_STEP_DETECTOR;
	case INV_ICM20948_SENSOR_STEP_COUNTER:                  return ANDROID_SENSOR_STEP_COUNTER;
	case INV_ICM20948_SENSOR_GAME_ROTATION_VECTOR:          return ANDROID_SENSOR_GAME_ROTATION_VECTOR;
	case INV_ICM20948_SENSOR_ROTATION_VECTOR:               return ANDROID_SENSOR_ROTATION_VECTOR;
	case INV_ICM20948_SENSOR_GEOMAGNETIC_ROTATION_VECTOR:   return ANDROID_SENSOR_GEOMAGNETIC_ROTATION_VECTOR;
	case INV_ICM20948_SENSOR_GEOMAGNETIC_FIELD:             return ANDROID_SENSOR_GEOMAGNETIC_FIELD;
	case INV_ICM20948_SENSOR_WAKEUP_SIGNIFICANT_MOTION:     return ANDROID_SENSOR_WAKEUP_SIGNIFICANT_MOTION;
	case INV_ICM20948_SENSOR_FLIP_PICKUP:                   return ANDROID_SENSOR_FLIP_PICKUP;
	case INV_ICM20948_SENSOR_WAKEUP_TILT_DETECTOR:          return ANDROID_SENSOR_WAKEUP_TILT_DETECTOR;
	case INV_ICM20948_SENSOR_GRAVITY:                       return ANDROID_SENSOR_GRAVITY;
	case INV_ICM20948_SENSOR_LINEAR_ACCELERATION:           return ANDROID_SENSOR_LINEAR_ACCELERATION;
	case INV_ICM20948_SENSOR_ORIENTATION:                   return ANDROID_SENSOR_ORIENTATION;
	case INV_ICM20948_SENSOR_B2S:                           return ANDROID_SENSOR_B2S;
	default:                                                return ANDROID_SENSOR_NUM_MAX;
	}
}

enum inv_icm20948_sensor inv_icm20948_sensor_android_2_sensor_type(int sensor)
{
	switch(sensor) {
	case ANDROID_SENSOR_ACCELEROMETER:                    return INV_ICM20948_SENSOR_ACCELEROMETER;
	case ANDROID_SENSOR_GYROSCOPE:                        return INV_ICM20948_SENSOR_GYROSCOPE;
	case ANDROID_SENSOR_RAW_ACCELEROMETER:                return INV_ICM20948_SENSOR_RAW_ACCELEROMETER;
	case ANDROID_SENSOR_RAW_GYROSCOPE:                    return INV_ICM20948_SENSOR_RAW_GYROSCOPE;
	case ANDROID_SENSOR_MAGNETIC_FIELD_UNCALIBRATED:      return INV_ICM20948_SENSOR_MAGNETIC_FIELD_UNCALIBRATED;
	case ANDROID_SENSOR_GYROSCOPE_UNCALIBRATED:           return INV_ICM20948_SENSOR_GYROSCOPE_UNCALIBRATED;
	case ANDROID_SENSOR_ACTIVITY_CLASSIFICATON:           return INV_ICM20948_SENSOR_ACTIVITY_CLASSIFICATON;
	case ANDROID_SENSOR_STEP_DETECTOR:                    return INV_ICM20948_SENSOR_STEP_DETECTOR;
	case ANDROID_SENSOR_STEP_COUNTER:                     return INV_ICM20948_SENSOR_STEP_COUNTER;
	case ANDROID_SENSOR_GAME_ROTATION_VECTOR:             return INV_ICM20948_SENSOR_GAME_ROTATION_VECTOR;
	case ANDROID_SENSOR_ROTATION_VECTOR:                  return INV_ICM20948_SENSOR_ROTATION_VECTOR;
	case ANDROID_SENSOR_GEOMAGNETIC_ROTATION_VECTOR:      return INV_ICM20948_SENSOR_GEOMAGNETIC_ROTATION_VECTOR;
	case ANDROID_SENSOR_GEOMAGNETIC_FIELD:                return INV_ICM20948_SENSOR_GEOMAGNETIC_FIELD;
	case ANDROID_SENSOR_WAKEUP_SIGNIFICANT_MOTION:        return INV_ICM20948_SENSOR_WAKEUP_SIGNIFICANT_MOTION;
	case ANDROID_SENSOR_FLIP_PICKUP:                      return INV_ICM20948_SENSOR_FLIP_PICKUP;
	case ANDROID_SENSOR_WAKEUP_TILT_DETECTOR:             return INV_ICM20948_SENSOR_WAKEUP_TILT_DETECTOR;
	case ANDROID_SENSOR_GRAVITY:                          return INV_ICM20948_SENSOR_GRAVITY;
	case ANDROID_SENSOR_LINEAR_ACCELERATION:              return INV_ICM20948_SENSOR_LINEAR_ACCELERATION;
	case ANDROID_SENSOR_ORIENTATION:                      return INV_ICM20948_SENSOR_ORIENTATION;
	case ANDROID_SENSOR_B2S:                              return INV_ICM20948_SENSOR_B2S;
	default:                                              return INV_ICM20948_SENSOR_MAX;
	}
}

static int skip_sensor(struct inv_icm20948 * s, unsigned char androidSensor)
{
	enum inv_icm20948_sensor icm20948_sensor_id = inv_icm20948_sensor_android_2_sensor_type(androidSensor);
	uint8_t skip_sample = s->skip_sample[icm20948_sensor_id];
	
	if (s->skip_sample[icm20948_sensor_id])
		s->skip_sample[icm20948_sensor_id]--;

	return skip_sample;
}

/* Identification related functions */
int inv_icm20948_get_whoami(struct inv_icm20948 * s, uint8_t * whoami)
{
	return inv_icm20948_read_reg_one(s, REG_WHO_AM_I, whoami);
}

void inv_icm20948_init_matrix(struct inv_icm20948 * s)
{
	// initialize chip to body
	s->s_quat_chip_to_body[0] = (1L<<30);
	s->s_quat_chip_to_body[1] = 0;
	s->s_quat_chip_to_body[2] = 0;
	s->s_quat_chip_to_body[3] = 0;


	//initialize mounting matrix
	memset(s->mounting_matrix, 0, sizeof(s->mounting_matrix));
	s->mounting_matrix[0] = 1;
	s->mounting_matrix[4] = 1;
	s->mounting_matrix[8] = 1;
	//initialize soft iron matrix
	s->soft_iron_matrix[0] = (1L<<30);
	s->soft_iron_matrix[4] = (1L<<30);
	s->soft_iron_matrix[8] = (1L<<30);

	inv_icm20948_set_chip_to_body_axis_quaternion(s, s->mounting_matrix, 0.0);
}

int inv_icm20948_init_structure(struct inv_icm20948 * s)
{
	int i;
	inv_icm20948_base_control_init(s);
	inv_icm20948_transport_init(s);
	inv_icm20948_augmented_init(s);
	//Init state
	s->set_accuracy = 0;
	s->new_accuracy = 0;
	for(i = 0; i < GENERAL_SENSORS_MAX; i ++){
		s->timestamp[inv_icm20948_sensor_android_2_sensor_type(i)] = 0;
	}
	return 0;
}

int inv_icm20948_initialize(struct inv_icm20948 * s, const uint8_t *dmp3_image, uint32_t dmp3_image_size)
{
	if(s->serif.is_spi) {
		/* Hardware initialization */
		// No image to be loaded from flash, no pointer to pass.
		if (inv_icm20948_initialize_lower_driver(s, SERIAL_INTERFACE_SPI, dmp3_image, dmp3_image_size)) {
			return -1;
		}
	}
	else {
		/* Hardware initialization */
		// No image to be loaded from flash, no pointer to pass.
		if (inv_icm20948_initialize_lower_driver(s, SERIAL_INTERFACE_I2C, dmp3_image, dmp3_image_size)) {
			return -1;
		}
	}
	return 0;
}

int inv_icm20948_init_scale(struct inv_icm20948 * s)
{
	/* Force accelero fullscale to 4g and gyr to 200dps */
	inv_icm20948_set_accel_fullscale(s, MPU_FS_4G);
	inv_icm20948_set_gyro_fullscale(s, MPU_FS_2000dps);

	return 0;
}

int inv_icm20948_set_fsr(struct inv_icm20948 * s, enum inv_icm20948_sensor sensor, const void * fsr)
{
	int result = 0;
	int * castedvalue = (int*) fsr;
	if((sensor == INV_ICM20948_SENSOR_RAW_ACCELEROMETER) ||
	   (sensor == INV_ICM20948_SENSOR_ACCELEROMETER)){
		enum mpu_accel_fs afsr;
		if(*castedvalue == 2)
			afsr = MPU_FS_2G;
		else if(*castedvalue == 4)
			afsr = MPU_FS_4G;
		else if(*castedvalue == 8)
			afsr = MPU_FS_8G;
		else if(*castedvalue == 16)
			afsr = MPU_FS_16G;
		else 
			return -1;
		result |= inv_icm20948_set_accel_fullscale(s, afsr);
	}
	else if((sensor == INV_ICM20948_SENSOR_GYROSCOPE) ||
			(sensor == INV_ICM20948_SENSOR_RAW_GYROSCOPE) ||
			(sensor == INV_ICM20948_SENSOR_GYROSCOPE_UNCALIBRATED)) {
		enum mpu_gyro_fs gfsr;
		if(*castedvalue == 250)
			gfsr = MPU_FS_250dps;
		else if(*castedvalue == 500)
			gfsr = MPU_FS_500dps;
		else if(*castedvalue == 1000)
		 	gfsr = MPU_FS_1000dps;
		else if(*castedvalue == 2000)
		 	gfsr = MPU_FS_2000dps;
		else 
			return -1;
		result |= inv_icm20948_set_gyro_fullscale(s, gfsr);
	}
	return result;
}

int inv_icm20948_get_fsr(struct inv_icm20948 * s, enum inv_icm20948_sensor sensor, const void * fsr)
{
	
	if((sensor == INV_ICM20948_SENSOR_RAW_ACCELEROMETER) ||
	   (sensor == INV_ICM20948_SENSOR_ACCELEROMETER)){
		unsigned char * castedvalue = (unsigned char*) fsr;
		int afsr = inv_icm20948_get_accel_fullscale(s);
		if(afsr == MPU_FS_2G)
			* castedvalue = 2;
		else if(afsr == MPU_FS_4G)
			* castedvalue = 4;
		else if(afsr == MPU_FS_8G)
			* castedvalue = 8;
		else if(afsr == MPU_FS_16G)
			* castedvalue = 16;
		else 
			return -1;
		
		return 1;
	}
	else if((sensor == INV_ICM20948_SENSOR_GYROSCOPE) ||
			(sensor == INV_ICM20948_SENSOR_RAW_GYROSCOPE) ||
			(sensor == INV_ICM20948_SENSOR_GYROSCOPE_UNCALIBRATED)) {
		unsigned short * castedvalue = (unsigned short*) fsr;
		int gfsr = inv_icm20948_get_gyro_fullscale(s);
		if(gfsr == MPU_FS_250dps)
			* castedvalue = 250;
		else if(gfsr == MPU_FS_500dps)
			* castedvalue = 500;
		else if(gfsr == MPU_FS_1000dps)
		 	* castedvalue = 1000;
		else if(gfsr == MPU_FS_2000dps)
		 	* castedvalue = 2000;
		else 
			return -1;
		
		return 2;
	}
	
	return 0;
}

int inv_icm20948_set_bias(struct inv_icm20948 * s, enum inv_icm20948_sensor sensor, const void * bias)
{
	int bias_q16[3];
	int bias_in[3];
	int rc = 0;
	short shift;
	switch(sensor) {
		case INV_ICM20948_SENSOR_ACCELEROMETER :
			memcpy(bias_q16, bias, sizeof(bias_q16));
			//convert from q16 to q25
			bias_in[0] = bias_q16[0] << (25 - 16);
			bias_in[1] = bias_q16[1] << (25 - 16);
			bias_in[2] = bias_q16[2] << (25 - 16);
			rc |= inv_icm20948_ctrl_set_acc_bias(s, bias_in);
			break;
		case INV_ICM20948_SENSOR_GYROSCOPE_UNCALIBRATED:
		case INV_ICM20948_SENSOR_GYROSCOPE:
			memcpy(bias_q16, bias, sizeof(bias_q16));
			//convert from q16 to :
			//Q19 => 2000dps
			//Q20 => 1000dps
			//Q21 => 500dps
			//Q22 => 250dps
			shift = ((20 + (MPU_FS_1000dps - inv_icm20948_get_gyro_fullscale(s))) - 16);
			bias_in[0] = bias_q16[0] << shift;
			bias_in[1] = bias_q16[1] << shift;
			bias_in[2] = bias_q16[2] << shift;
			
			rc |= inv_icm20948_ctrl_set_gyr_bias(s, bias_in);
			break;
		case INV_ICM20948_SENSOR_MAGNETIC_FIELD_UNCALIBRATED:
		case INV_ICM20948_SENSOR_GEOMAGNETIC_FIELD:
			memcpy(bias_q16, bias, sizeof(bias_q16));
			// bias is already in q16
			rc |= inv_icm20948_ctrl_set_mag_bias(s, bias_q16);
			break;
		default :
			rc = -1;
			break;
	}
	return (rc == 0) ? 1 : rc;
}

int inv_icm20948_get_bias(struct inv_icm20948 * s, enum inv_icm20948_sensor sensor, void * bias)
{
	int bias_qx[3];
	int bias_out[3];
	int rc = 0;
	short shift;
	switch(sensor) {
		case INV_ICM20948_SENSOR_ACCELEROMETER :
			rc |= inv_icm20948_ctrl_get_acc_bias(s, bias_qx);
			//convert from q25 to q16 
			bias_out[0] = bias_qx[0] >> (25 - 16);
			bias_out[1] = bias_qx[1] >> (25 - 16);
			bias_out[2] = bias_qx[2] >> (25 - 16);
			memcpy(bias, bias_out, sizeof(bias_out));
			break;
		case INV_ICM20948_SENSOR_GYROSCOPE_UNCALIBRATED:
		case INV_ICM20948_SENSOR_GYROSCOPE:
			rc |= inv_icm20948_ctrl_get_gyr_bias(s, bias_qx);
			//convert from qn to q16:
			//Q19 => 2000dps
			//Q20 => 1000dps
			//Q21 => 500dps
			//Q22 => 250dps
			shift = ((20 + (MPU_FS_1000dps - inv_icm20948_get_gyro_fullscale(s))) - 16);
			bias_out[0] = bias_qx[0] >> shift;
			bias_out[1] = bias_qx[1] >> shift;
			bias_out[2] = bias_qx[2] >> shift;

			memcpy(bias, bias_out, sizeof(bias_out));
			break;
		case INV_ICM20948_SENSOR_MAGNETIC_FIELD_UNCALIBRATED:
		case INV_ICM20948_SENSOR_GEOMAGNETIC_FIELD:
			rc |= inv_icm20948_ctrl_get_mag_bias(s, bias_qx);
			// bias is already in q16
			memcpy(bias, bias_qx, sizeof(bias_qx));
			break;
		default:
			rc = -1;
			break;
	}
	return (rc == 0) ? 3*sizeof(float) : rc;
}

int inv_icm20948_set_lowpower_or_highperformance(struct inv_icm20948 * s, uint8_t lowpower_or_highperformance)
{
	s->go_back_lp_when_odr_low = 0;
	if(lowpower_or_highperformance)
		return inv_icm20948_enter_low_noise_mode(s);
	else
		return inv_icm20948_enter_duty_cycle_mode(s);
}


int inv_icm20948_get_lowpower_or_highperformance(struct inv_icm20948 * s, uint8_t * lowpower_or_highperformance)
{
	(void)s;
	*lowpower_or_highperformance = CHIP_LOW_NOISE_ICM20948;
	return 1;
}

static void DmpDriver_convertion(signed char transformedtochar[9],
                                 const int32_t MatrixInQ30[9])
{
	// To convert Q30 to signed char value
	uint8_t iter;
	for (iter = 0; iter < 9; ++iter)
		transformedtochar[iter] = MatrixInQ30[iter] >> 30;
}

int inv_icm20948_set_matrix(struct inv_icm20948 * s, const float matrix[9], enum inv_icm20948_sensor sensor)
{
	int32_t mounting_mq30[9];
	int32_t compass_mq30[9];
	int result = 0;
	int i;

	if ((sensor == INV_ICM20948_SENSOR_GEOMAGNETIC_FIELD)||
		(sensor == INV_ICM20948_SENSOR_MAGNETIC_FIELD_UNCALIBRATED)){
		for(i = 0; i < 9; ++i)
			compass_mq30[i] = (int32_t)(matrix[i] * (1 << 30));
		// Convert compass mounting matrix in char
		DmpDriver_convertion(s->mounting_matrix_secondary_compass, compass_mq30);
		//Notify new matrix to mag calculation with accgyr mountingmatrix
		result |= inv_icm20948_compass_dmp_cal(s, s->mounting_matrix, s->mounting_matrix_secondary_compass);
	} else if ((sensor == INV_ICM20948_SENSOR_RAW_ACCELEROMETER) || 
		(sensor == INV_ICM20948_SENSOR_ACCELEROMETER) || 
		(sensor == INV_ICM20948_SENSOR_RAW_GYROSCOPE) ||
		(sensor == INV_ICM20948_SENSOR_GYROSCOPE) ||
		(sensor == INV_ICM20948_SENSOR_GYROSCOPE_UNCALIBRATED)) {
		for(i = 0; i < 9; ++i)
			mounting_mq30[i] = (int32_t)(matrix[i] * (1 << 30));
		// Convert mounting matrix in char
		DmpDriver_convertion(s->mounting_matrix, mounting_mq30);
		/*Apply new matrix */
		inv_icm20948_set_chip_to_body_axis_quaternion(s, s->mounting_matrix, 0.0);
		//Update Dmp B2S according to new mmatrix in q30
		result |= dmp_icm20948_set_B2S_matrix(s, (int*)mounting_mq30);
		//Notify new matrix to mag calculation with accgyr mountingmatrix
		result |= inv_icm20948_compass_dmp_cal(s, s->mounting_matrix, s->mounting_matrix_secondary_compass);
	}

	return result;
}

int inv_icm20948_initialize_auxiliary(struct inv_icm20948 * s)
{
	if (inv_icm20948_set_slave_compass_id(s, s->secondary_state.compass_slave_id) )
		return -1;
	return 0;
}

int inv_icm20948_soft_reset(struct inv_icm20948 * s)
{
	//soft reset like
	int rc = inv_icm20948_write_single_mems_reg(s, REG_PWR_MGMT_1, BIT_H_RESET);
	// max start-up time is 100 msec
	inv_icm20948_sleep_us(100000);
	return rc;
}

int inv_icm20948_enable_sensor(struct inv_icm20948 * s, enum inv_icm20948_sensor sensor, inv_bool_t state)
{
	uint8_t androidSensor = sensor_type_2_android_sensor(sensor);

	if(0!=inv_icm20948_ctrl_enable_sensor(s, androidSensor, state))
		return -1;

	//In case we disable a sensor, we reset his timestamp
	if(state == 0)
		s->timestamp[sensor] = 0;

	return 0;
}

int inv_icm20948_set_sensor_period(struct inv_icm20948 * s, enum inv_icm20948_sensor sensor, uint32_t period)
{
	uint8_t androidSensor = sensor_type_2_android_sensor(sensor);

	if(0!=inv_icm20948_set_odr(s, androidSensor, period))
		return -1;
	
	// reset timestamp value and save current odr
	s->timestamp[sensor] = 0;
	s->sensorlist[sensor].odr_us = period * 1000;
	return 0; 
}

int inv_icm20948_enable_batch_timeout(struct inv_icm20948 * s, unsigned short batchTimeoutMs)
{
	int rc;
	/* Configure batch timeout */
	if (inv_icm20948_ctrl_set_batch_timeout_ms(s, batchTimeoutMs) == 0) {
		/* If configuration was succesful then we enable it */
		if((rc = inv_icm20948_ctrl_enable_batch(s, 1)) != 0)
			return rc;
	} else {         
		/* Else we disable it */
		if((rc = inv_icm20948_ctrl_enable_batch(s, 0)) != 0)
			return rc;                     
	}
	return 0;
}

int inv_icm20948_load(struct inv_icm20948 * s, const uint8_t * image, unsigned short size)
{
	return inv_icm20948_firmware_load(s, image, size, DMP_LOAD_START);
}

/** @brief Returns 1 if the sensor id is a streamed sensor and not an event-based sensor */
static int inv_icm20948_is_streamed_sensor(uint8_t id)
{
	switch(id)
	{
	case ANDROID_SENSOR_WAKEUP_TILT_DETECTOR :
	case ANDROID_SENSOR_ACTIVITY_CLASSIFICATON :
	case ANDROID_SENSOR_FLIP_PICKUP :
	case ANDROID_SENSOR_B2S :
	case ANDROID_SENSOR_STEP_COUNTER:
	case ANDROID_SENSOR_WAKEUP_SIGNIFICANT_MOTION :
	case ANDROID_SENSOR_STEP_DETECTOR :
			return 0;
	default :
			return 1;
	}
}

/** @brief Preprocess all timestamps so that they either contain very last time at which MEMS IRQ was fired 
 * or last time sent for the sensor + ODR */
static uint8_t inv_icm20948_updateTs(struct inv_icm20948 * s, int * data_left_in_fifo, 
	unsigned short * total_sample_cnt, uint64_t * lastIrqTimeUs)
{
	/** @brief Very last time in us at which IRQ was fired since flushing FIFO process was started */
	unsigned short sample_cnt_array[GENERAL_SENSORS_MAX] = {0};
	uint8_t i;
	
	if (inv_icm20948_fifo_swmirror(s, data_left_in_fifo, total_sample_cnt, sample_cnt_array)) {
		for(i = 0; i< GENERAL_SENSORS_MAX; i++) {
			if (inv_icm20948_is_streamed_sensor(i)) {
				s->timestamp[inv_icm20948_sensor_android_2_sensor_type(i)] = *lastIrqTimeUs;
			}
		}
		return -1;
	}
	// we parse all senosr according to android type
	for (i = 0; i < GENERAL_SENSORS_MAX; i++) {
		if (inv_icm20948_is_streamed_sensor(i)) {
			if (sample_cnt_array[i]) {
				/** Number of samples present in MEMS FIFO last time we mirrored it */
				unsigned short fifo_sample_cnt = sample_cnt_array[i];

				/** In case of first batch we have less than the expected number of samples in the batch */
				/** To avoid a bad timestamping we recompute the startup time based on the theorical ODR and the number of samples */
				if (s->sFirstBatch[inv_icm20948_sensor_android_2_sensor_type(i)]) {
					s->timestamp[inv_icm20948_sensor_android_2_sensor_type(i)] += *lastIrqTimeUs-s->timestamp[inv_icm20948_sensor_android_2_sensor_type(i)] 
																	- fifo_sample_cnt*s->sensorlist[inv_icm20948_sensor_android_2_sensor_type(i)].odr_us;
					s->sFirstBatch[inv_icm20948_sensor_android_2_sensor_type(i)] = 0;
				}

				/** In case it's the first time timestamp is set we create a factice one,
				In other cases, update timestamp for all streamed sensors depending on number of samples available in FIFO
				first time to be printed is t1+(t2-t1)/N
				- t1 is last time we sent data
				- t2 is when IRQ was fired so that we pop the FIFO
				- N is number of samples */
				
				if(s->timestamp[inv_icm20948_sensor_android_2_sensor_type(i)] == 0) {
					s->timestamp[inv_icm20948_sensor_android_2_sensor_type(i)] = *lastIrqTimeUs;
					s->timestamp[inv_icm20948_sensor_android_2_sensor_type(i)] -= s->sensorlist[inv_icm20948_sensor_android_2_sensor_type(i)].odr_us*(fifo_sample_cnt);
					s->sensorlist[inv_icm20948_sensor_android_2_sensor_type(i)].odr_applied_us = s->sensorlist[inv_icm20948_sensor_android_2_sensor_type(i)].odr_us;
				}
				else {
					s->sensorlist[inv_icm20948_sensor_android_2_sensor_type(i)].odr_applied_us = (*lastIrqTimeUs-s->timestamp[inv_icm20948_sensor_android_2_sensor_type(i)])/fifo_sample_cnt;
				}
			}
		} else {
			/** update timestamp for all event sensors with time at which MEMS IRQ was fired */
			s->timestamp[inv_icm20948_sensor_android_2_sensor_type(i)] = *lastIrqTimeUs;
		}
	}
	
	return 0;
}
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
