nico-malkov/variometer/software/nRF5_SDK_17.1.0/examples/peripheral/variometer_v143/icm20948/invensense/Device.h

/*
 * ________________________________________________________________________________________________________
 * Copyright (c) 2015-2015 InvenSense Inc. All rights reserved.
 *
 * This software, related documentation and any modifications thereto (collectively “Software”) is subject
 * to InvenSense and its licensors' intellectual property rights under U.S. and international copyright
 * and other intellectual property rights laws.
 *
 * InvenSense and its licensors retain all intellectual property and proprietary rights in and to the Software
 * and any use, reproduction, disclosure or distribution of the Software without an express license agreement
 * from InvenSense is strictly prohibited.
 *
 * EXCEPT AS OTHERWISE PROVIDED IN A LICENSE AGREEMENT BETWEEN THE PARTIES, THE SOFTWARE IS
 * PROVIDED "AS IS", WITHOUT WARRANTY OF ANY KIND, EXPRESS OR IMPLIED, INCLUDING BUT NOT LIMITED
 * TO THE WARRANTIES OF MERCHANTABILITY, FITNESS FOR A PARTICULAR PURPOSE AND NON-INFRINGEMENT.
 * EXCEPT AS OTHERWISE PROVIDED IN A LICENSE AGREEMENT BETWEEN THE PARTIES, IN NO EVENT SHALL
 * INVENSENSE BE LIABLE FOR ANY DIRECT, SPECIAL, INDIRECT, INCIDENTAL, OR CONSEQUENTIAL DAMAGES, OR ANY
 * DAMAGES WHATSOEVER RESULTING FROM LOSS OF USE, DATA OR PROFITS, WHETHER IN AN ACTION OF CONTRACT,
 * NEGLIGENCE OR OTHER TORTIOUS ACTION, ARISING OUT OF OR IN CONNECTION WITH THE USE OR PERFORMANCE
 * OF THE SOFTWARE.
 * ________________________________________________________________________________________________________
 */

/** @defgroup Device Device
 *	@brief    Abstract device interface definition
 *
 *            All functions declared in this file are virtual.
 *            They aim to provide a unified way of accessing InvenSense devices.
 *            All functions shall return a int for which 0 indicates success and
 *            a negative value indicates an error as described by enum inv_error
 *
 *            If a particular device implementation does not support any of the
 *            method declared here, it shall return INV_ERROR_NIMPL.
 *
 *            Implementation is not expected to be thread-safe.
 *
 *            Refer to concrete device implementation for additionnal and specific
 *            information about API usage related to a particular device.
 *
 *	@{
 */

#ifndef _INV_DEVICE_H_
#define _INV_DEVICE_H_

#ifdef __cplusplus
extern "C" {
#endif

#include "InvBool.h"
#include "InvError.h"
#include "SensorTypes.h"
#include "SensorConfig.h"
#include "HostSerif.h"

#include <assert.h>

/** @brief FW version structure definition
 */
typedef struct inv_fw_version
{
	uint8_t  major, minor, patch; /**< major, minor, patch version number */
	char     suffix[16];          /**< version suffix string (always terminated by '\0') */
	uint32_t crc;                 /**< FW checksum */
} inv_fw_version_t;

/** @brief Device virtual table definition
 */
typedef struct inv_device_vt {
	int (*whoami)(void * self, uint8_t * whoami);
	int (*reset)(void * self);
	int (*setup)(void * self);
	int (*cleanup)(void * self);
	int (*load)(void * self, int type, const uint8_t * image, uint32_t size,
			inv_bool_t verify, inv_bool_t force);
	int (*poll)(void * self);
	int (*self_test)(void * self, int sensor);
	int (*get_fw_info)(void * self, struct inv_fw_version * version);
	int (*ping_sensor)(void * self, int sensor);
	int (*set_running_state)(void * self, inv_bool_t state);
	int (*enable_sensor)(void * self, int sensor, inv_bool_t start);
	int (*set_sensor_period_us)(void * self, int sensor, uint32_t period);
	int (*set_sensor_timeout)(void * self, int sensor, uint32_t timeout);
	int (*flush_sensor)(void * self, int sensor);
	int (*set_sensor_bias)(void * self, int sensor, const float bias[3]);
	int (*get_sensor_bias)(void * self, int sensor, float bias[3]);
	int (*set_sensor_mounting_matrix)(void * self, int sensor, const float matrix[9]);
	int (*get_sensor_data)(void * self, int sensor, inv_sensor_event_t * event);
	int (*set_sensor_config)(void * self, int sensor, int setting, const void * arg, unsigned size);
	int (*get_sensor_config)(void * self, int sensor, int setting, void * arg, unsigned size);
	int (*write_mems_register)(void * self, int sensor, uint16_t reg_addr, const void * value, unsigned size);
	int (*read_mems_register)(void * self, int sensor, uint16_t reg_addr, void * value, unsigned size);
} inv_device_vt_t;

/** @brief Abtract device object definition
 */
typedef struct inv_device
{
	void *                        instance; /**< pointer to object instance */
	const struct inv_device_vt *  vt;       /**< pointer to object virtual table */
	const inv_sensor_listener_t * listener; /**< pointer to listener instance */
} inv_device_t;

/** @brief Gets WHO AM I value
 *
 *  Can be called before performing device setup
 *
 *  @param[in]  dev     pointer to device object instance
 *  @param[out] whoami  WHO AM I value
 *  @return             0 on success
 *                      INV_ERROR_TRANSPORT in case of low level serial error
 */
static inline int inv_device_whoami(const inv_device_t * dev, uint8_t * whoami)
{
	assert(dev && dev->vt);

	if(dev->vt->whoami)
		return dev->vt->whoami(dev->instance, whoami);

	return INV_ERROR_NIMPL;
}

/** @brief Resets the device to a known state
 *
 *  Will perform an HW and SW reset of device, and reset internal driver states
 *  To know value.
 *  Should be called before setup or when device state is unknown.
 *
 *  @param[in] dev      pointer to device object instance
 *  @return             0 on success
 *                      INV_ERROR_TIMEOUT if reset does not complete in time
 *                      INV_ERROR_TRANSPORT in case of low level serial error
 */
static inline int inv_device_reset(const inv_device_t * dev)
{
        //NRF_LOG_INFO("Here!");
	assert(dev && dev->vt);

	if(dev->vt->reset)
		return dev->vt->reset(dev->instance);

	return INV_ERROR_NIMPL;
}

/** @brief Performs basic device initialization
 *
 *  Except if device's flash memory is outdated, devuie should be able to handle
 *  request after setup() is complete.
 *  If devices's flash memory need to be updated, load_begin()/load_continue()/
 *  load_end() methods must be called first with suitable argument.
 *  
 *  @param[in] dev      pointer to device object instance
 *  @return             0 on success
 *                      INV_ERROR_TIMEOUT if setup does not complete in time
 *                      INV_ERROR_TRANSPORT in case of low level serial error
 */
static inline int inv_device_setup(const inv_device_t * dev)
{
	assert(dev && dev->vt);

	if(dev->vt->setup)
		return dev->vt->setup(dev->instance);

	return INV_ERROR_NIMPL;
}

/** @brief Shutdown the device and clean-up internal states
 *
 *  @param[in] dev      pointer to device object instance
 *  @return             0 on success
 *                      INV_ERROR_TIMEOUT if clean-up does not complete in time
 *                      INV_ERROR_TRANSPORT in case of low level serial error
 */
static inline int inv_device_cleanup(const inv_device_t * dev)
{
	assert(dev && dev->vt);

	if(dev->vt->cleanup)
		return dev->vt->cleanup(dev->instance);

	return INV_ERROR_NIMPL;
}

/** @brief Polls the device for data
 *
 *  Will read device interrupt registers and data registers or FIFOs.
 *  Will parse data and called sensor events handler provided at init time. 
 *  Handler will be called in the same context of this function.
 * 
 *  @warning Care should be taken regarding concurency. If this function is
 *           called in a dedicated thread, suitable protection must be used to
 *           avoid concurent calls to poll() or any other device methods.
 *
 *  @param[in] dev      pointer to device object instance
 *  @return             0 on success
 *                      INV_ERROR_TRANSPORT in case of low level serial error
 *                      INV_ERROR_UNEXPECTED in case of bad formated or 
 *                                           un-handled data frame
 */
static inline int inv_device_poll(const inv_device_t * dev)
{
	assert(dev && dev->vt);

	if(dev->vt->poll)
		return dev->vt->poll(dev->instance);

	return INV_ERROR_NIMPL;
}
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
